mikkelmi2/aipcb/docs/reports/m11.md

# M11 — controlled impedance, card edges, via transitions & high-speed verification: delivery report

**Delivered, and this report is a reconstruction.** All of M11a–M11e, its tests,
`docs/format.md`, `docs/roadmap.md` and [ADR 0010](../decisions/0010-highspeed.md)
were built and committed across five commits (`4599b95`, `fbd048e`, `166fa4f`,
`e33b0ce`, `1e0a6a2`) by one session, which was then terminated by an
infrastructure failure — an API session limit — at the moment it said *"Now the
performance measurements:"*. This report was written afterwards, in a separate
pass over a clean tree at `1e0a6a2`, by someone who did not write the code.

Everything below is either **measured here, on a quiet machine, in this pass**, or
attributed to the ADR and the commit messages that the implementing session wrote.
Where the two disagree, the measurement wins and the disagreement is stated. Where
something could not be determined from the repository, it says so rather than
inventing an account. It is not a live record of how the work went, and it should
not be read as one.

## Deviations, stated loudly

Everything not delivered as the specification wrote it, in one place and at the top.

| Item | What happened |
|---|---|
| *"the M11e report runs clean (no reference-plane crossings, stubs under threshold) on everything that routed"* | **Two of twelve pair objects do not run clean.** Reference continuity and via stubs *are* clean — 629.3 mm projected, **0** plane crossings, worst stub **0.000 mm** against a 0.5 mm threshold, width and gap deviation **0.0** on all twelve. Skew is not: `REFCLKN+REFCLKP` comes out **0.292 mm** and `PCIE_RXN+PCIE_RXP` **0.256 mm** against the **0.125 mm** their class declares, and both are *delivered* rather than handed over. Discussed at length under "The skew question" — it is the one place in this milestone where the delivered result sits closest to the marginal delivery the milestone exists to prevent. |
| The `diff-pair` copper sliver | **Not resolved, and it was expected to be.** The kickoff expected M11d rule 1 to close it. Measured here: the routed, unfilled board still carries exactly **one** `copper_sliver` warning. Rule 1 could not have closed it — it applies only to classes naming an `impedance_diff_ohm`, and `diff-pair`'s `lvds` class names none (measured: `standoff` 1.0, `target_ohm` null). Full verdict below. |
| `standoff_k`'s own default | **Unusable on the milestone's own reference board.** The default is 3; `examples/pcie-sata` sets **1.4**, with the arithmetic written into the source. At k = 3 every pair on that board is refused. The rule works — it refuses correctly and names itself in the hint — but a default that no bundled board can take is a default worth flagging. |
| Net-class field names | **Renamed.** The specification writes `impedance_diff`, `max_skew`, `max_uncoupled` and `class: diff_pair`. The implementation spells the unit into each — `impedance_diff_ohm`, `max_skew_mm` (reused from M7), `max_uncoupled_mm` — and does **not** implement `class: diff_pair` at all, because pair-ness already comes from `diff_pair:` on the nets. Recorded in ADR 0010 under "The naming deviation"; repeated here because a reader following the specification will type four field names that do not exist. |
| A KiCad warning that cannot be removed | **`lib_footprint_mismatch` on every card-edge board.** ADR 0010 Decision 2 gives the board outline one author, which means placing the edge footprint without its own `Edge.Cuts`, which means it is no longer byte-identical to its library copy. Measured: `aipcb check examples/pcie-sata` returns **1 DRC warning and 0 DRC errors**, and that warning is this one. There is no version of this that has both. |
| Two contacts on the reference board are not connected at all | **PERST# and the A1–B17 presence-detect strap are absent from the netlist**, not handed over. Both must cross all three lane pairs and a sig/gnd/pwr/sig stackup has no signal layer left to cross on. The source says so in a comment; `docs/roadmap.md` records it. The consequence for the numbers: `90/90 routed` counts 90 connections that exist, and does not count two a real card would need. |
| No pair was handed over | The milestone's own framing was *"a human finishing 2 of 11 pairs manually is success"*. **Eleven of eleven routed as coupled pairs, and nothing reached M9f.** That is a better result than the bar, but it means the reference board does not exercise the hand-over path at all; the two M11d rules that *can* force a hand-over — the standoff corridor and the coupling budget — are proved by purpose-built fixtures in `tests/test_highspeed.py`, not by the shipped example. |
| AC-coupling capacitor *placement* | **Validated and measured, never moved.** `role: ac_coupling` checks that the two capacitors sit level across the pair's travel and reports how far out they are; the placer does not position them. Recorded in ADR 0010 and `docs/roadmap.md`. |
| Impedance derivation covers outer layers only | **Surface microstrip, and nothing checks that you asked for it.** A class routed on an inner layer between two planes is stripline, a different formula, and today it gets a microstrip width back with no warning. No bundled design does this; nothing stops one. Recorded in `docs/roadmap.md`. |
| "M11d is the only permitted stretcher change" | **`src/aipcb/route/stretch.py` was not touched.** The three rules landed in `route/pairs.py` (+425/−10), the coupled-pair path. Not a deviation from the letter — it is narrower than the guardrail allowed — but a reader looking for M11d in the stretcher will find nothing there. |
| Suite runtime | **Up from 13 m 57 s to 20 m 27 s** (1090 tests, up from 968). Measured here, not estimated. The new board is the expensive part — routing `pcie-sata` costs 36 s each time a test class does not have it cached — but the split between it and the 73 new unit tests was not separately measured. |

Nothing else was descoped.

## What was built

| Piece | Where it lives |
|---|---|
| M11a — the IPC-2141 derivation and the Hammerstad one it does not replace | `impedance.py` |
| — resolving a class's geometry against the declared stackup | `highspeed.py`, `model/layout.py` |
| — validating what comes out of it | `checks/impedance.py` |
| M11b — the card edge as a footprint: stripped `Edge.Cuts`, keepout, fab note | `compile/edge.py`, `compile/zones.py` |
| — outline-versus-footprint agreement, and the error that hands the vertices back | `checks/edge.py` |
| M11c — the pair via-transition generator | `route/transition.py`, `model/highspeed.py` |
| — the AC-coupling audit | `checks/accouple.py` |
| M11d — the three stretcher rules | `route/pairs.py` (+425 lines) |
| M11e — the high-speed verification report | `checks/highspeed.py` |

| New module | Lines |
|---|---|
| `tests/test_highspeed.py` | 1387 |
| `src/aipcb/checks/highspeed.py` | 768 |
| `src/aipcb/route/transition.py` | 657 |
| `examples/pcie-sata/design.yaml` | 589 |
| `src/aipcb/compile/edge.py` | 447 |
| `src/aipcb/checks/edge.py` | 356 |
| `src/aipcb/checks/accouple.py` | 238 |
| `src/aipcb/checks/impedance.py` | 205 |
| `src/aipcb/highspeed.py` | 196 |
| `src/aipcb/impedance.py` | 189 |
| `src/aipcb/model/highspeed.py` | 84 |
| `examples/library/highspeed.yaml` | 181 |

New source blocks, all optional: `transitions:`, `role: edge_connector`,
`role: ac_coupling`, and eight net-class fields. No new commands.

## The eleven pairs, one by one

This is what the milestone cares most about, so it is measured rather than read
off the source. One `aipcb check examples/pcie-sata/design.yaml --json`, on the
tree as committed, read out of `summary.routing.pairs` and `summary.highspeed.pairs`.

Eleven declared pairs become **fourteen coupled routing segments** — the PCIe
transmit lane is split in two by its coupling capacitors, and the receive pair and
the reference clock are each split in two by a via transition — which the M11e
report merges back into **twelve pair objects**.

| # | Pair | Class | Layer | Routed as a pair? | Coupled length | Skew / budget | Uncoupled / budget | Wall hugs | Verdict |
|---|---|---|---|---|---|---|---|---|---|
| 1 | `PCIE_TXP/N` (controller → caps) | `pcie_tx` | F.Cu | **yes** | 8.08 mm | 0.000 / 0.125 mm | 0.51 / 6.0 mm | **2** (`U1.17`, `U1.20`) | **routed, flagged** — rule 2, flag stands |
| 2 | `PCIE_TXP_C/N_C` (caps → fingers) | `pcie_tx` | F.Cu | **yes** | 10.07 mm | 0.000 / 0.125 mm | 0.76 / 6.0 mm | — | **routed within all M11d rules** |
| 3 | `PCIE_RXP/N` | `pcie_rx` | B.Cu + F.Cu | **yes** (both segments) | 18.83 mm | **0.256 / 0.125 mm** | 2.54 / 6.0 mm | **1** (`U1.22`) | **routed, over its skew budget** |
| 4 | `REFCLKP/N` | `pcie_rx` | B.Cu + F.Cu | **yes** (both segments) | 16.68 mm | **0.292 / 0.125 mm** | 2.69 / 6.0 mm | **1** (`U1.14`) | **routed, over its skew budget** |
| 5 | `SATA0_TXP/N` | `sata` | F.Cu | **yes** | 30.93 mm | 0.004 / 0.25 mm | 1.13 / 5.0 mm | — | **routed within all M11d rules** |
| 6 | `SATA0_RXP/N` | `sata` | F.Cu | **yes** | 31.10 mm | 0.199 / 0.25 mm | 0.44 / 5.0 mm | — | **routed within all M11d rules** |
| 7 | `SATA1_TXP/N` | `sata` | F.Cu | **yes** | 30.97 mm | 0.049 / 0.25 mm | 0.44 / 5.0 mm | — | **routed within all M11d rules** |
| 8 | `SATA1_RXP/N` | `sata` | F.Cu | **yes** | 31.41 mm | 0.124 / 0.25 mm | 0.45 / 5.0 mm | — | **routed within all M11d rules** |
| 9 | `SATA2_TXP/N` | `sata` | F.Cu | **yes** | 31.30 mm | 0.053 / 0.25 mm | 0.45 / 5.0 mm | — | **routed within all M11d rules** |
| 10 | `SATA2_RXP/N` | `sata` | F.Cu | **yes** | 30.92 mm | 0.021 / 0.25 mm | 0.44 / 5.0 mm | — | **routed within all M11d rules** |
| 11 | `SATA3_TXP/N` | `sata` | F.Cu | **yes** | 31.12 mm | 0.042 / 0.25 mm | 0.44 / 5.0 mm | — | **routed within all M11d rules** |
| 12 | `SATA3_RXP/N` | `sata` | F.Cu | **yes** | 30.93 mm | 0.004 / 0.25 mm | 1.13 / 5.0 mm | — | **routed within all M11d rules** |

Reading it as the milestone asks:

* **Handed over: none.** `summary.routing.handed_over` is empty; `routed` is 90 of
  90 connections, `failed` 0, in **one** negotiation iteration.
* **Routed within all three M11d rules and inside their own class budgets:
  nine of twelve pair objects** — all eight SATA pairs and the connector-side half
  of the PCIe transmit lane.
* **Routed, with M11d rule 2's flag standing: three** — the controller-side
  transmit pair and the F.Cu halves of the receive pair and the reference clock.
  Each leaves the QFN between the ground pads on either side of its escape, each
  was re-tightened once with those pads' clearance inflated, and re-tightening
  cannot move a pad. **This is the outcome rule 2 specifies in so many words**
  ("attempt one re-tighten … if that fails, the flag stands"), and it is the
  correct treatment: the pair is built, the deviation is named, its distance and
  length are in the report.
* **Routed, over a budget its own class declares: two** — the receive pair and the
  reference clock, on skew. These two are *also* among the three above, so the
  arithmetic across the twelve is 9 clean + 1 flagged only for wall-hugging + 2
  flagged for both. That last pair of pairs is not so easily defended, and it gets
  its own section.
* Every one of the twelve carries its derived geometry **exactly**: 0.2888 mm /
  0.15 mm on the 85 Ω classes, 0.2390 mm / 0.2 mm on the 100 Ω one, with a measured
  width and gap deviation of **0.0** read back off the copper.

The acceptance clause asked for *"≥ the SATA pairs route and tighten within all
M11d rules with 0 DRC violations"*. All eight SATA pairs do, and so do four more
segments; **0 DRC errors** on the filled board.

### The skew question, and whether the treatment is defensible

The specification's own wording is *"any pair that cannot meet the rules is handed
over via M9f with reasons, never delivered marginal"*. Two pairs are delivered
outside a number their class declares, so it is worth being explicit about which
side of that line they fall on.

**What is measured.** Half-conductor lengths, read off the router's own record:

| Pair | Positive half | Negative half | Out of length | Budget | As a fraction of the run |
|---|---|---|---|---|---|
| `REFCLKP/N` | 21.2157 mm | 20.9241 mm | **0.2916 mm** | 0.125 mm | 1.4 % |
| `PCIE_RXP/N` | 20.7427 mm | 20.9982 mm | **0.2555 mm** | 0.125 mm | 1.2 % |

They are exactly the two pairs a via transition splits, and they are the only two
pairs on the board over budget. The transition column itself is *not* the
asymmetry: the four signal vias sit symmetric about the point the source named to
within 7 µm (`REFCLKN` at +0.2749/−0.0072 mm from centre, `REFCLKP` at
−0.2749/+0.0072 mm). What the transition costs is the splay to the opened-out
0.55 mm via pitch at each end plus the two fan-outs it creates where there was one,
and `_match_lengths` reports there is no fan-out leg long enough to meander the
difference into.

**The case for the treatment being correct.** Skew is not one of M11d's three
rules. The three that force a hand-over are the standoff corridor, the wall-hugging
flag and the uncoupled budget; skew is an M11e *reporting* item, severity warning
by default, promotable to an error with `verify: error` on the class. Nothing was
silenced: six warnings across the two pairs, four `diff-pair-skew` and two
`hs-skew`, all carrying the number. The budget was **not** widened to fit — the
source's own comment records that the SATA class's first draft was 0.127 mm, that
one pair missed it by 49 µm, and that the class was rewritten with an argument
rather than tuned until the warning went away. And, on a first-principles estimate
made here: microstrip on this stackup at εr 4.4, h 0.2104 mm, w 0.2888 mm gives
εeff ≈ 3.25 and a delay of ≈ 6.0 ps/mm, so **0.292 mm is ≈ 1.8 ps against a Gen3
unit interval of 125 ps** — about 1.4 % of a UI. That is a number a link budget
absorbs without noticing.

**The case against.** The class declares 0.125 mm. It is not an inherited default;
somebody wrote it. A pair delivered at 2.3× its own declared budget is a pair the
source and the board disagree about, and the mechanism that exists to make that
disagreement fatal — `verify: error` — was available and not used. The acceptance
clause *"the M11e report runs clean … on everything that routed"* is, on the
measurement, **not met**.

**The verdict this report takes.** The treatment is defensible, and the acceptance
clause is still missed. Those are both true and it is worth keeping them apart. It
is defensible because the failure is loud, quantified, tied to a named cause, and
because the alternative on offer was not "a better pair" but "no PCIe lane at all
on a four-layer stackup" — the pre-M11c behaviour, where a pair that had to change
layer was simply refused. What would make it indefensible is the budget being
edited to 0.3 mm, and it was not. But *"runs clean"* is what the milestone asked
for, and 10 of 12 is not 12 of 12; it belongs in the deviations table, which is
where it is.

The honest framing for anyone reading the board rather than the report: **the eight
SATA pairs are finished work. The PCIe lane is routed, measured and annotated, and
a Gen3 sign-off still wants a human and an SI tool** — which is what
`summary.highspeed.method` says in the report itself: *"rule-based geometry checks,
not electromagnetic simulation"*.

## The `diff-pair` copper sliver: an expectation that was not met

The milestone kickoff told the implementing session that M11d's rules were
*expected* to resolve the known copper sliver on `examples/diff-pair`, and to flag
it prominently if they did not. **They did not.** Measured here rather than
inferred:

| Board | Command | `copper_sliver` |
|---|---|---|
| `diff-pair`, routed, **unfilled** | `aipcb route all` then `kicad-cli pcb drc --severity-all` | **1** (warning, F.Cu) |
| `diff-pair`, routed, **filled** | `aipcb check` | **0** |

The track geometry is unchanged by M11. Why rule 1 could not have touched it, from
the code and from the same measurement run: **M11d applies only to a class that
names an `impedance_diff_ohm`, and `diff-pair`'s `lvds` class names none** — its
pair audit comes back with `standoff: 1.0` and `target_ohm: null`, so the standoff
corridor never ran on that board at all. `docs/roadmap.md` adds that the sliver is
between two **GND** tracks rather than between the pair's halves, which would put
it out of rule 1's reach even on a controlled-impedance board.

That last point is the one thing here I **could not verify independently**: KiCad
9.0.8 reports this violation with an empty `items` array and no position, in both
the JSON and the report format, so DRC does not say which copper it is between.
The claim that it is between two GND tracks is the implementing session's, taken
from `docs/roadmap.md` and `tests/test_routing.py`, and this pass could not confirm
or refute it.

The marker in `tests/test_check_loop.py` — `"diff-pair": frozenset({"kicad-copper-sliver"})`
— is **left standing and must stay standing**. It is a permissive allowance rather
than a required outcome, so it is vacuous under `aipcb check` today (which reads
the filled board, where the pour closes the wedge); it is live in
`tests/test_routing.py::ALLOWED_VIOLATIONS`, which reads the unfilled one. Retiring
it would delete the record of a defect that is still in the copper a fabricator
receives before the pour is drawn. To the implementing session's credit it was not
touched.

## The four `pcie-sata` known issues

`tests/test_check_loop.py` gained a `pcie-sata` entry with four codes and the
reasoning written into the file. Measured here, each one:

| Code | Count | What it is, measured |
|---|---|---|
| `diff-pair-wall-hugging` | **3** | M11d rule 2, flag standing after one failed re-tighten. `PCIE_TXN+PCIE_TXP` beside `U1.17` and `U1.20`, both at **0.261 mm for 0.774 mm**; `REFCLKN+REFCLKP` beside `U1.14` at **0.218 mm for 0.899 mm**; `PCIE_RXN+PCIE_RXP` beside `U1.22` at **0.257 mm for 0.796 mm**. Threshold: closer than 3 × the 0.15 mm gap (0.45 mm) for longer than 5 × it (0.75 mm). All three were re-tightened with the offending pads' clearance inflated; the audit records `retightened: true, resolved_by_retighten: false` for each. **This is the outcome rule 2 specifies. Defensible without qualification.** |
| `diff-pair-skew` | **4** | Two pairs, reported twice each — see the reporting wart below. From `_match_lengths` at 0.251 mm (REFCLK) and 0.249 mm (PCIE_RX); from `measure_skew` over the whole conductor at 0.292 mm and 0.256 mm. |
| `hs-skew` | **2** | M11e restating the whole-conductor numbers — 0.292 mm and 0.256 mm — after meanders. **Closer to a marginal delivery than the wall-hugging flag is, and argued out above.** |
| `kicad-lib-footprint-mismatch` | **1** | The card-edge footprint placed without its own `Edge.Cuts`, so it no longer matches its library copy. The unavoidable price of ADR 0010 Decision 2. It is the board's **only** DRC finding, and it is a warning; DRC errors are 0. |

**A reporting wart found while measuring, not fixed.** The same pair is reported
out of budget **three times, with two different numbers** and no label saying why
they differ. `route/pairs.py::_match_lengths` warns per routed *segment* while it is
still trying to meander (0.251 mm for the reference clock); `measure_skew` then
warns again over the *whole conductor*, via barrels included (0.292 mm for the
same pair); and M11e reports the second number a third time as `hs-skew`. Six
warnings for two pairs. Nothing is wrong with any individual number — they measure
different things — but a reader gets "REFCLKN+REFCLKP is 0.251 mm out of length"
and "REFCLKN+REFCLKP is 0.292 mm out of length" three lines apart with no
explanation. Reported here rather than corrected, because this pass documents and
measures the delivered code rather than changing it.

## Per-pad-instance keying, re-verified against the shared-UUID defect

`docs/roadmap.md` records that pads sharing a *number* share a UUID, and M11's
brief warned this was where an edge connector would bite hardest. Re-measured here
on the boards this milestone actually builds:

| Component | Footprint | Pads | Distinct numbers | Distinct pad UUIDs |
|---|---|---|---|---|
| `J1` (the card edge) | `Connector_PCBEdge:BUS_PCIexpress_x1` | **36** | **36** | **36** |
| `J2`–`J5` (SATA) | `Connector_JST:JST_GH_SM07B-GHS-TB…` | 9 | 8 | **8** |
| `U1` | `Package_DFN_QFN:QFN-48-1EP_7x7mm_P0.5mm` | 65 | 50 | **50** |
| `usb-port`'s `J1`, for comparison | `Connector_USB:USB_Micro-B_Amphenol_10103594-0001LF_Horizontal` | 17 | 6 | **6** |

* **The defect does not bite the card edge at all.** KiCad's PCIe x1 footprint
  numbers every contact distinctly, `A1`–`A18` and `B1`–`B18`, so each finger has
  its own identity in the file as well as in the router. That confirms ADR 0010's
  Finding 4 independently.
* **The defect is still there, on the same board.** Each JST connector has two
  shell tabs both numbered `MP` sharing one UUID, and each QFN has sixteen
  exposed-pad sub-pads numbered `49` sharing one. The router tells them apart
  because `route.obstacles` keys on `reference#index` and never on the UUID.
* **`usb-port` is unchanged**: **31 pads carrying 20 distinct UUIDs**, with twelve
  pads numbered `6` sharing one. Exactly the figure M10 recorded, so nothing in M11
  moved it either way.

### What commit `1e0a6a2` actually found

The commit titled *"the keepout the UUID index had not heard of"* is not about pad
UUIDs. It is about the **one zone in this toolchain that nobody declares**: M11b
puts a pour keepout round a card edge's finger field, generated from the
connector's placement rather than written in `pours:`, and nothing mapped its UUID
back to source. Reproduced here by building the index with and without the fix and
running the same synthetic DRC violation through `checks/kicad_reports.py`:

| Index | Where the violation points | Hint |
|---|---|---|
| **as shipped** | `examples/pcie-sata/design.yaml:451:3`, path `('placement', 'J_PCIE')` | the real edge-clearance hint |
| **without the entry** | nowhere — `loc: None`, `path: ()`, `unmapped_uuids: ['07808365-…']` | *"this item is not one aipcb generated — it was probably added by hand in KiCad"* |

Which is exactly the wrong answer about the one piece of copper geometry the
toolchain invented by itself. The zone is in the board as
`"J1 finger field, kept clear of pour"`, 20.9 × 5.5 mm on `F.Cu` and `B.Cu` with
`copperpour not_allowed`, and its UUID `07808365-5859-56df-bdf7-867032aa3787` is
`element_uuid("zone", "fingers", "J1")` — a function of the source, like every
other generated identity. The defect surfaced when the *full* suite ran, not when
the M11b tests did: it takes a DRC violation landing on that zone to see it.

## What else was verified

### The card edge

Measured on the built board: `J1`'s footprint carries **0** `Edge.Cuts` primitives
(they are stripped), the top-level outline carries 16 `Edge.Cuts` graphics, and
`checks/edge.py` reports *"the board outline reproduces all 11 of the footprint's
edge primitives, to within 0.01 mm"*. The finger keepout is present as described
above; the fab note reads *"36 fingers on B.Cu, F.Cu, set back 1.30 mm from the
card's leading edge. The set-back is where the bevel goes"*. The acceptance case
that the missing-notch error must fail *helpfully* is
`test_a_missing_notch_is_an_error_that_hands_the_vertices_back`, which asserts the
hint contains a pasteable `board:` block.

**Not verified here: that the board "opens correctly in KiCad".** This pass has no
GUI. `kicad-cli`'s ERC and DRC both run to completion on it, and `pcbnew` loads it
to fill it, which is the strongest proxy available headlessly.

### The via transitions

Two, both declared in the source, both on the pairs that arrive on the A-side
fingers (on `B.Cu`) and leave the controller on `F.Cu`:

| Transition | Pair | Pitch → via pitch | Return vias | Furthest | Barrel | Stub |
|---|---|---|---|---|---|---|
| 0 | `REFCLKN+REFCLKP` | 0.4388 → **0.55 mm** | **2 of 2** | 0.9999 mm (budget 1.2) | F.Cu–B.Cu | **0.000 mm** |
| 1 | `PCIE_RXN+PCIE_RXP` | 0.4388 → **0.55 mm** | **2 of 2** | 0.9999 mm (budget 1.2) | F.Cu–B.Cu | **0.000 mm** |

Zero stub is the right answer for an outer-to-outer through via and, per commit
`e33b0ce`, it is the answer that had to be *earned* — see the findings below.

### The AC coupling

`C2`/`C3` couple `PCIE_TXN+PCIE_TXP` to `PCIE_TXN_C+PCIE_TXP_C`, measured at
**1.400 mm apart across the route and level along it to within 0.0000 mm**. Both
halves of both segments come out at identical length (8.5937 mm each side before
the caps, 10.8312 mm each side after), which is what "symmetric entry" means when
it is read off the geometry rather than asserted.

### The M11e report on `pcie-sata`

| Measure | Result | Threshold |
|---|---|---|
| Controlled-impedance track projected onto its declared reference | **629.3 mm** | — |
| Reference-plane crossings (splits, voids, net changes) | **0** | any is a finding |
| Worst via stub | **0.000 mm** on `PCIE_RXN` | 0.5 mm |
| Width deviation, all 12 pair objects | **0.0** | 10 % |
| Gap deviation, all 12 pair objects | **0.0** | 10 % |
| Pairs over their coupling budget | **0** (worst 2.69 mm against 6.0) | per class |
| Pairs over their skew budget | **2** | per class |

Commit `fbd048e` records 550.1 mm of controlled-impedance track; the measurement
here is 629.3 mm, because that commit predates M11c and the two transitions it
adds. Both numbers are right for the tree they were taken on.

### The impedance derivation, checked against a second implementation

The ADR's arithmetic was re-derived here from IPC-2141 by hand rather than trusted:

| Target | Gap | `solve_width` | Independent recomputation of `Zdiff` |
|---|---|---|---|
| 85 Ω | 0.15 mm | **0.2888 mm** | 85.008 Ω |
| 100 Ω | 0.20 mm | **0.2390 mm** | 100.001 Ω |
| 85 Ω | 0.20 mm | **0.3220 mm** | 85.002 Ω |

The module and the hand recomputation agree to three decimal places, and the widths
are the ones the board actually carries. The Hammerstad/IPC disagreement ADR 0010
calls "8 %" measures **8.4 %** at 0.322 mm on this stackup (92.18 Ω against
85.00 Ω). The declared stack sums to 0.1004 mm of copper plus 1.4858 mm of
dielectric plus 0.02 mm of mask = **1.606 mm**, which is the 1.6 mm the source
declares.

### Everything that was already working

Measured in this pass, all eleven examples:

| Example | Build byte-stable | Byte-identical to its golden | `filled_polygon` in build output | Check errors | DRC errors | Routed |
|---|---|---|---|---|---|---|
| `congestion` | yes | yes | 0 | 0 | 0 | 4/4 |
| `diff-pair` | yes | yes | 0 | 0 | 0 | 11/11 |
| `enclosure` | yes | yes | 0 | 0 | 0 | 32/32 |
| `ldo-supply` | yes | yes | 0 | 0 | 0 | 13/13 |
| `led-blinker` | yes | yes | 0 | 0 | 0 | 13/13 |
| `mcu-4layer` | yes | yes | 0 | 0 | 0 | 36/36 |
| `overconstrained` | yes | yes | 0 | 0 | 0 | 1/4¹ |
| `pcie-sata` | yes | yes | 0 | 0 | 0² | 90/90 |
| `qfn-fanout` | yes | yes | 0 | 0 | 0 | 41/41 |
| `routing-demo` | yes | yes | 0 | 0 | 0 | 10/10 |
| `usb-port` | yes | yes | 0 | 0 | 0 | 24/24 |

¹ `overconstrained` is the example that cannot be finished; three connections are
handed over and stay as ratlines, exactly as before M11.
² One DRC *warning*: `lib_footprint_mismatch`, discussed above.

The backward-compatibility claim is stronger than "byte-stable": `git diff
b7d9c5e..HEAD -- tests/golden/` shows **only `tests/golden/pcie-sata/` was added**
and no pre-M11 golden was touched, so all ten earlier examples rebuild
byte-identically to files frozen before this milestone existed. Every example's
build output still contains **zero** `filled_polygon` records, which is M10's
stability policy holding under a new generator.

The only non-`info` diagnostics anywhere outside `pcie-sata` are the two already
known: `qfn-fanout`'s deliberate `plane-fragmented` and `usb-port`'s
`diff-pair-not-coupled` honest refusal.

## Performance

Measured on 2026-08-21 on the tree at `1e0a6a2`, one run each, on all eleven
examples, with nothing else running — no test suite, no other job. KiCad 9.0.8.
This table is what M12 measures regressions against.

### The pipeline, end to end

`aipcb`'s own commands, cold per invocation. `route` and `check` are *incremental*
(`route all` minus `build`, and `check` minus `route all`), because each command
re-runs the stages before it. **M10's numbers in brackets where they exist.**

| Example | `validate` | `build` | route | check | `export` |
|---|---|---|---|---|---|
| `congestion` | 1.75 s *(1.72)* | 1.77 s *(1.78)* | 0.19 s *(0.15)* | 0.75 s *(0.76)* | 2.33 s *(2.30)* |
| `diff-pair` | 2.31 s *(2.34)* | 2.44 s *(2.43)* | 0.58 s *(0.54)* | 2.08 s *(2.18)* | 3.83 s *(3.76)* |
| `enclosure` | 3.58 s *(3.50)* | 3.68 s *(3.54)* | 4.54 s *(4.55)* | 2.22 s *(2.25)* | 5.03 s *(4.93)* |
| `ldo-supply` | 2.90 s *(2.85)* | 2.94 s *(2.97)* | 0.40 s *(0.38)* | 2.15 s *(2.18)* | 4.34 s *(4.27)* |
| `led-blinker` | 2.49 s *(2.49)* | 2.57 s *(2.53)* | 0.75 s *(0.78)* | 2.17 s *(2.18)* | 3.92 s *(3.86)* |
| `mcu-4layer` | 4.19 s *(4.11)* | 4.23 s *(4.17)* | 10.44 s *(10.42)* | 2.74 s *(2.65)* | 5.88 s *(5.80)* |
| `overconstrained` | 1.76 s *(1.74)* | 1.78 s *(1.75)* | 0.24 s *(0.21)* | 0.71 s *(0.82)* | 2.33 s *(2.31)* |
| **`pcie-sata`** | **5.23 s** | **5.29 s** | **36.93 s** | **2.15 s** | **6.91 s** |
| `qfn-fanout` | 2.80 s *(2.78)* | 2.88 s *(2.94)* | 5.71 s *(5.60)* | 2.40 s *(2.44)* | 4.24 s *(4.22)* |
| `routing-demo` | 2.48 s *(2.47)* | 2.54 s *(2.55)* | 0.85 s *(0.78)* | 2.14 s *(2.22)* | 3.91 s *(3.87)* |
| `usb-port` | 3.49 s *(3.43)* | 3.54 s *(3.46)* | 2.83 s *(2.90)* | 2.23 s *(2.21)* | 4.82 s *(4.81)* |
| **total, 11** | **32.98 s** | **33.66 s** | **63.46 s** | **21.74 s** | **47.54 s** |
| the same ten M10 measured | 27.75 s *(27.43)* | 28.37 s *(28.12)* | 26.53 s *(26.33)* | 19.59 s *(19.88)* | 40.63 s *(40.12)* |

**No stage regressed.** On the ten examples M10 measured, `validate` moves +1.2 %,
`build` +0.9 %, `route` +0.8 %, `export` +1.3 % and `check` **−1.5 %**. Every
per-example difference is within 0.15 s; the three largest are `enclosure`'s build
(+0.14 s), `overconstrained`'s checking (−0.11 s) and `qfn-fanout`'s routing
(+0.11 s), which is what one run each on one machine looks like rather than a
trend. A design that names no `impedance_diff_ohm` runs none of M11's new code,
and the numbers say so.

### `pcie-sata`, prominently

It is the most expensive board in the repository by a wide margin — **44.4 s** of
wall clock for `aipcb check`, against 17.4 s for the next one (`mcu-4layer`). Of
that, 39.9 s is the work itself and the remaining ≈4.5 s is interpreter start plus
the cold library resolution every command pays. Where the 39.9 s goes, measured in
one process so the stages are comparable:

| Stage | Time | Share of the 39.9 s in-process check |
|---|---|---|
| `build` | 1.14 s | 2.9 % |
| **routing (total)** | **35.56 s** | **89.1 %** |
| — of which: transition generation (M11c) | 0.027 s | 0.07 % |
| — of which: pair centre-line tightening, first pass (14 calls) | 4.493 s | 11.3 % |
| — of which: **M11d rule 2 wall-hug scans (14 calls)** | **0.014 s** | **0.03 %** |
| — of which: **M11d rule 2 re-tighten rounds (3 calls)** | **0.125 s** | **0.31 %** |
| stitching | 0.034 s | 0.1 % |
| plane analysis (M10d) | 0.013 s | 0.03 % |
| **M11e high-speed analysis** | **0.111 s** | **0.28 %** |
| zone fill (`pcbnew`) | 1.65 s | 4.1 % |
| `kicad-cli sch erc` | 0.39 s | 1.0 % |
| `kicad-cli pcb drc` | 0.89 s | 2.2 % |
| `kicad-cli pcb export gerbers` | 0.19 s | — (export only) |

**What the M11d re-tightening rounds cost: 0.139 seconds**, on a board where three
pairs trip rule 2 — 0.35 % of the check, 0.4 % of the routing. **What the M11e
analysis costs: 0.111 seconds** for 629.3 mm of track projected onto two planes at
50 µm steps, plus the geometry audit, the skew read-back, the stub arithmetic and
the coupling audit. Both are, in practice, free.

**One caveat, and it matters.** M11d **rule 1 is not separable** from the number
above. The standoff corridor is not an extra pass — it widens the corridor handed
to A\*, which changes the congestion penalty and therefore the search on every
controlled-impedance connection. There is no way to time it without routing the
board twice with two different `standoff_k`, and this pass did not change the
example to do so. What *can* be said is that **rule 2 costs 0.14 s** on the
board that trips it three times, and that rule 3's budget check — a maximum over a
list of per-half lengths — is too small to time separately and was not. And that
35.6 s of routing on
a 90-connection four-layer board is in line with `mcu-4layer`'s 10.0 s for 36
connections and `qfn-fanout`'s 5.7 s for 41.

### Where the time goes, all eleven examples

`aipcb`'s own stages on the left, what `kicad-cli` and `pcbnew` cost on the right,
measured in one process so the library caches are warm after the first example —
which is why `build` here is a fraction of the `build` column above. The ≈2.5 s
difference is the same fixed floor M10 identified: resolving parts against KiCad's
on-disk libraries, paid once per process by every command, and still nobody has
looked at it.

| Example | build | route | transitions | stitching | planes | high speed | | fill (`pcbnew`) | ERC | DRC | gerbers |
|---|---|---|---|---|---|---|---|---|---|---|---|
| `congestion` | 0.89 s | 0.18 s | — | — | — | — | | — | 0.20 s | 0.54 s | 0.17 s |
| `diff-pair` | 0.35 s | 0.56 s | — | — | 2 ms | — | | 1.26 s | 0.23 s | 0.57 s | 0.18 s |
| `enclosure` | 0.78 s | 4.49 s | — | 0.02 s | 3 ms | — | | 1.22 s | 0.30 s | 0.67 s | 0.18 s |
| `ldo-supply` | 0.44 s | 0.39 s | — | — | 3 ms | — | | 1.20 s | 0.26 s | 0.59 s | 0.18 s |
| `led-blinker` | 0.11 s | 0.72 s | — | — | 3 ms | — | | 1.20 s | 0.24 s | 0.65 s | 0.19 s |
| `mcu-4layer` | 0.06 s | 10.05 s | — | 0.03 s | 10 ms | — | | 1.62 s | 0.33 s | 0.70 s | 0.19 s |
| `overconstrained` | 0.02 s | 0.20 s | — | — | — | — | | — | 0.20 s | 0.53 s | 0.18 s |
| **`pcie-sata`** | **1.14 s** | **35.56 s** | **0.03 s** | **0.03 s** | **13 ms** | **0.11 s** | | **1.65 s** | **0.39 s** | **0.89 s** | **0.19 s** |
| `qfn-fanout` | 0.28 s | 5.65 s | — | 0.03 s | 6 ms | — | | 1.22 s | 0.26 s | 0.78 s | 0.20 s |
| `routing-demo` | 0.04 s | 0.78 s | — | — | 4 ms | — | | 1.20 s | 0.24 s | 0.63 s | 0.18 s |
| `usb-port` | 0.04 s | 2.78 s | — | 0.03 s | 3 ms | — | | 1.22 s | 0.30 s | 0.61 s | 0.18 s |

Against M10's equivalent table, every column on every pre-M11 example is within
measurement noise of where it was: `mcu-4layer`'s routing 10.20 → 10.05 s,
`qfn-fanout`'s 5.69 → 5.65 s, the fill flat at 1.20–1.65 s everywhere, ERC and DRC
unmoved. The only two entries that changed by more than 0.1 s are `ldo-supply`'s
build (0.32 → 0.44 s) and `qfn-fanout`'s (0.44 → 0.28 s), in opposite directions,
which is what per-process cache ordering looks like rather than a regression in
either.

Three things worth naming:

* **The high-speed analysis is free**, at 0.11 s on the only board that runs it —
  the same order as M10's plane analysis, and for the same reason: it is geometry
  over polygons somebody else already computed.
* **`pcie-sata`'s `build` is genuinely 1.14 s** and not a cache artefact — it is the
  eighth example in that process, so the caches are warm. Twelve components, a
  36-pad edge footprint, a 65-pad QFN and the outline-versus-footprint comparison
  cost more than any other board's build.
* **Routing still dominates everything**, now more than ever: 61.4 s of the 88.1 s
  total across eleven boards, 35.6 s of it one board. M11 did not change that and
  did not make it worse.
* **M10's "fixed ≈2.5 s floor" is not fixed.** Subtracting each warm build above
  from its cold counterpart in the first table gives 0.88 s (`congestion`), 1.76 s
  (`overconstrained`), 2.46–2.60 s (four boards), 2.90 s (`enclosure`), 3.50 s
  (`usb-port`), 4.15 s (`pcie-sata`) and **4.17 s (`mcu-4layer`)**. It tracks how
  many distinct KiCad footprint libraries a design touches, not a constant. It is
  still the largest single cost on **seven of the eleven** examples — everywhere
  routing does not dominate — and it is still unexamined.

## The empirical findings

Eight are in [ADR 0010](../decisions/0010-highspeed.md), written by the session
that measured them. The ones that changed a decision, with what this pass could
confirm:

**The two impedance formulas in this codebase disagree by 8 %** (Finding 1).
Confirmed here at **8.4 %** on the reference stackup. The controlled-impedance path
uses IPC-2141 for both the derivation *and* the audit that later checks it, because
an audit that recomputes the target with a different formula audits the arithmetic
rather than the board. Hammerstad stays on the M8 `estimate_gap` path so no
pre-M11 board changes geometry — which the byte-identical goldens confirm.

**`layout.stackup.layers` was decorative and had to stop being** (Finding 2). The
block had been in the schema since M1 and nothing derived geometry from it; the
uniform-dielectric fallback gives 0.48 mm where the prepreg under `F.Cu` is
0.2104 mm, a factor of 2.3 and a 40 % error in the derived width. A declared stack
is now honoured, and only when it is *complete* — a partial declaration is ignored
rather than half-believed, because it looks authoritative and is not.

**Emitting both outline authors produces a board KiCad rejects** (Finding 3). Two
`invalid_outline: self-intersecting` errors plus ten `copper_edge_clearance` ones,
all twelve gone when the footprint's copy is stripped.

**A return via placed by eye costs the pair its coupling** (Finding 5). Placed at
0.925 mm from the transition centre against the 1.007 mm the pair's corridor needs,
the receive pair could not tighten, fell back to two separately routed nets, and
those took detours that cost eight further pairs their coupling. **82 µm, and 9 of
14 coupled runs.** The generator computes the distance instead of choosing it, and
the shipping board places its return vias at 0.9999 mm.

**KiCad normalises a through via's recorded span — and that is the finding that
made the via-stub number real** (Finding 6; commit `e33b0ce`). A via written
`(layers "F.Cu" "In2.Cu")` with a through drill comes back from `pcbnew` written
`(layers "F.Cu" "B.Cu")`. That is not wrong — a through via *is* drilled the whole
way — but it erases the one thing a stub calculation needs, which is where the
signal stopped. **Every stub measured off the filled board therefore came out at
exactly zero: comfortable, and false.** The stub is now taken from the router's own
record of what it drilled, and the filled board is used only for what it is
authoritative about, which is copper. The 0.000 mm in the table above is now zero
because the barrel really does end where the signal does; it is a corrected
measurement rather than an unchanged one, and a test
(`test_a_transition_to_an_inner_layer_leaves_the_rest_of_the_barrel`) makes the
non-zero case fail if the shortcut ever comes back.

**"Parallel" is load-bearing in rule 2.** The first implementation measured the
length of centre-line inside a feature's skirt, which counts going past the end of
a pad as hugging it — 1.11 mm on the QFN escape where the parallel part is the
pad's own 0.875 mm, under the 1.0 mm threshold. The stretch is now counted only
while the distance holds to within one gap of its closest approach.

**An `Edge.Cuts` arc costs the router its clearance** (Finding 7). Arcs are
approximated by 24 chords, and a chord runs inside its arc by the sagitta — 8.13 µm
on the 0.95 mm keying notch. KiCad reported ten `copper_edge_clearance` errors at
0.1419 mm against 0.1500 mm asked for; 0.1500 − 0.1419 = 0.0081 mm, the sagitta to
two significant figures. `RoutingEnvironment.arc_slack` now adds the worst sagitta
on the board to the edge keep-out.

**A fabricator needs web between holes, not daylight** (Finding 8). Two GND vias
0.3250 mm apart left 0.1255 mm of web against a 0.2495 mm minimum;
`merge_overlapping_holes` merged holes that *overlapped*, and the test is now the
drill plus the minimum web.

## Defects found

Six. Four fixed, two recorded and not chased:

* **An `Edge.Cuts` arc's chord approximation ate the edge clearance.** Fixed
  (Finding 7). Surfaced because `pcie-sata` is the first board to hug an arc.
* **Same-net via merging used overlap where it needed web.** Fixed (Finding 8).
  Surfaced from a DRC violation on the same board.
* **Via stubs measured off the filled board were all zero, and wrongly so.** Fixed
  by reading the router's record instead (Finding 6). Surfaced because a test
  asserted a *non-zero* stub for an inner-layer transition and got zero.
* **The card-edge pour keepout had no source mapping.** Fixed in `1e0a6a2`.
  Surfaced when the full suite ran, not when M11b's own tests did.
* **`_repair` can produce a route that crosses another net.** *Not fixed.* Found on
  `PRSNT` before that net was dropped: the second-pass repair in
  `route/plan.py::_repair` routed it across two already-placed `REFCLK` tracks and
  KiCad reported two `tracks_crossing` errors. The repair builds its private field
  from the base environment *plus* everything placed so far, so the copper it
  crossed *was* in the obstacle set — something between that field and the realized
  geometry is not honouring it. Recorded in `docs/roadmap.md` rather than left as a
  surprise. It does not manifest on any bundled example today: `pcie-sata` runs 16
  `route-repaired` second passes and comes back with 0 DRC errors. **It is router
  work, it is unexplained, and it is the most serious thing in this report that is
  still open.**
* **The skew reporting wart** described above: one pair, three warnings, two
  different numbers, no label. Found in this measuring pass; not fixed, because
  this pass documents rather than changes.

## Deliberately not built

Recorded in [`docs/roadmap.md`](../roadmap.md) and ADR 0010:

* **Electromagnetic simulation and eye-diagram prediction.** M11e is rule-based
  geometry and says so in its own first line, in `summary.highspeed.method` and in
  the README. Exporting geometry to a solver is M12's subject.
* **Full environment-controlled tightening** beyond the three M11d rules.
* **Back-drilling and blind/buried-via optimisation** for stub elimination. The stub
  is measured and reported; removing it is a fabrication process nothing here
  should commit somebody to by default.
* **Placing the AC-coupling capacitors.** Validated and measured, not moved.
* **Unifying the two impedance formulas.** Kept apart deliberately, because
  changing the old one moves the geometry of every board built before M11.
* **Stripline.** An inner-layer pair gets a microstrip width and no warning.

## Suite state

| Check | Result |
|---|---|
| `pytest -q` | **exit 0** — **1089 passed, 1 skipped**, **20 m 27 s** (1090 collected, up from 968) |
| `ruff check .` | **All checks passed** |
| `mypy --strict src/aipcb` | **Success: no issues found in 75 source files** (66 before M11) |

The one skip is `test_sexpr_corpus`'s, as it has been since M1. The suite grew by
**122 tests and 6.5 minutes**; `tests/test_highspeed.py` is new and holds 73 test
methods across thirteen classes, and the rest is the parametrised per-example
classes gaining an eleventh example that takes 36 s to route.

The acceptance cases the specification names each have a fixture built to make the
answer knowable:

| Acceptance case | Test |
|---|---|
| the missing keying notch must fail *helpfully* | `test_a_missing_notch_is_an_error_that_hands_the_vertices_back` — asserts the hint contains a pasteable `board:` block with the notch's own vertices |
| return vias within spec, stub computed against the stackup | `test_return_vias_are_placed_within_spec`, `test_an_outer_to_outer_through_via_has_no_stub`, `test_a_transition_to_an_inner_layer_leaves_the_rest_of_the_barrel` |
| pair-cap-pair as one object, symmetric entry, budget | `test_the_example_couples_symmetrically`, `test_the_pairing_comes_from_the_netlist`, `test_moving_one_capacitor_along_the_route_is_reported` |
| wall-hugging: the re-tighten resolves it, or the flag appears | `test_a_pair_beside_a_wall_is_re_tightened_away_from_it` (a header 1.8 mm away, resolved) and `test_the_wall_hugging_rule_fires_and_says_what_it_found` (the reference board, flag standing) |
| a wrong width warns at validation *and* in the audit | `test_a_deliberately_wrong_width_is_reported_twice`, `test_a_class_may_promote_its_findings_to_errors` |
| the M11d refusals | `test_an_uncoupled_budget_that_cannot_be_met_is_a_refusal`, `test_a_standoff_the_board_cannot_give_refuses_and_names_itself`, `test_the_standoff_applies_only_to_controlled_impedance_classes` |
| the generator regime | `test_a_second_run_into_the_same_directory_is_byte_identical`, `test_the_transition_vias_are_not_duplicated_by_a_second_run`, `test_the_uuid_space_is_a_function_of_the_source` |
| the shared-pad-UUID defect, both ways | `test_the_pcie_fingers_do_not_share_pad_numbers`, `test_the_sata_shells_do_share_one_and_the_router_still_tells_them_apart` |

One existing test class changed deliberately: `TestCheckLoop.KNOWN_ISSUES` gained a
`pcie-sata` entry with four codes and the reasoning written into the file. The
`diff-pair` entry was **not** touched, which is the right call — see the sliver
verdict above.

## What M12 needs to know

M12 is SI simulation, and **it will simulate only the pairs that actually routed**,
so the pair-by-pair table above is its direct input. Concretely:

* **Twelve pair objects are available to simulate**, all coupled, all carrying their
  derived geometry exactly. Nine are inside every budget their class declares; three
  carry a standing wall-hugging flag with the offending feature, its distance and
  the parallel length named; two are over their skew budget by a measured amount.
  Nothing is handed over, so there is no "unrouted pair" case to handle on this
  board — and equally, no example in the repository exercises the M9f hand-over of
  a *controlled-impedance* pair. If M12 needs one, it will have to build it.
* **`summary.highspeed` in `aipcb check --json` is the machine-readable form**, with
  `method` stating in the payload itself that this is not simulation. It carries
  per-pair target and actual width and gap, coupled and uncoupled lengths, skew, the
  reference-gap list and the via-stub list with positions.
* **The reference plane is *declared*, never inferred.** `reference:` on the class;
  `pcie_tx` and `sata` name `In1.Cu` (GND), `pcie_rx` names `In2.Cu` (P3V3, which is
  an AC ground for a decoupled rail and, more usefully, a continuous one). A solver
  wanting the real return path should read that field rather than guessing at the
  nearest plane.
* **The stub number comes from the router, not the board.** Finding 6 above. Any
  M12 code that reads via spans off a `pcbnew`-round-tripped board will get
  `F.Cu`/`B.Cu` for everything and compute a stub of zero for every via on the
  board. This is the single most likely way for M12 to produce a comfortable, false
  number.
* **A board with no `pours:` gets `hs-reference-unchecked` rather than a silent
  pass.** The reference check needs filled copper and therefore ADR 0009's `pcbnew`
  subprocess.
* **`analyse_highspeed(tree, netlist, audits, skew, vias=…, filled=…)` is a pure
  function of a parsed board plus the router's audit records.** It costs 0.11 s on
  the largest board here. A second consumer of the same inputs is cheap.
* **The geometry M12 would export is microstrip only.** Nothing checks that a
  controlled-impedance class is on an outer layer, and an inner-layer pair silently
  gets a microstrip width. If M12 exports geometry for a solver, that is the first
  place the solver and this toolchain will disagree.

Open questions this milestone leaves:

* **`_repair` crossing another net** — unexplained, recorded, not reproducible on
  any bundled example. It is a routing correctness question and it outranks
  everything else on this list.
* **The skew reporting wart** — three warnings, two numbers, one pair.
* **Is 0.125 mm the right intra-pair skew budget for a Gen3 class?** The board
  declares it and misses it by 2.3× on two pairs; the estimate above puts the miss
  at ≈1.8 ps against a 125 ps UI. Either the budget is too tight for what this
  router can deliver through a via transition, or the transition needs to give
  length back. Nobody has decided which, and the report currently just says the
  number.
* **The per-process library-resolution cost**, which M10 called a "fixed ≈2.5 s
  floor". Measured across eleven examples here it is **not fixed**: subtracting the
  warm in-process build from the cold command gives 0.88 s on `congestion`, 2.50 s
  on `ldo-supply`, 3.50 s on `usb-port` and **4.17 s on `mcu-4layer`** — it scales
  with how many distinct KiCad footprint libraries a design touches. It is still the
  largest single cost on seven of the eleven examples, and nobody has looked at it
  in two milestones.
* **Nothing checks that `stackup.planes` and `pours:` agree** — M10 raised it, M11
  made it matter (a `reference:` layer is now validated to be *poured*, which is
  half the check), and it is still not closed in general.
