mikkelmi2/aipcb/docs/reports/m13.md

# M13 — correctness & calibration: delivery report

Four things, in the order they had to happen. A silent-correctness bug in the
routing core, found and closed. The systematic impedance error M12 measured, fixed
at the model rather than at the symptom. The skew verdict, rebuilt on the data the
first two fixes cleaned. And the hygiene the chain kept tripping over.

Everything below was measured on 2026-08-22 on the development machine (16 cores,
30 GB RAM, Linux 7.0.0-29-generic), on the tree as committed. Where a number is a
projection rather than a measurement it says so, in the same sentence.

## Deviations, stated loudly

| Acceptance clause | What happened |
|---|---|
| *"The `_repair` reproducing test (or the proof of unreachability), the cross-net invariant active, all examples clean"* | **Met, and the diagnosis was not the one M11 expected.** `_repair` was obeying an obstacle set that had silently lost four polygons; the bug was in the *merge*, not in the repair. Reproduced end to end, fixed, invariant active on every route, all eleven examples clean. §1. |
| *"CPWG-derived links simulate within ±10 % of target impedance; the report shows old vs new numbers per link"* | **Met on one of the three links that ran, and eight were not run.** `PCIE_TXP/N` goes from −21.6 % to **−5.8 %**, `PCIE_RXP/N` from −27.6 % to **−14.4 %**, `REFCLKP/N` from −40.1 % to −41.4 % on a run that did not converge. Old and new are tabled per link in §2 with the residual and a hypothesis for each, and **the ±10 % band was not widened**. The eight SATA links were not re-simulated; the cost of doing so was measured rather than guessed and is in §2. |
| *"The fitted-Δτ verdict runs on all 11 pcie-sata links; fitted vs geometric skew tabulated; thresholds documented from measured noise"* | **Runs on 3 of 11, for the reason above.** The verdict is built, unit-tested against synthetic curves with known delays, and tabulated against the geometric skew for the three links that have data. The threshold is documented from what those three measure, which is a thinner basis than the milestone asked for and is labelled as such. |
| *"Container cleanup test passes; duplicate findings collapsed"* | **Met.** Three cleanup paths, one of which caught a real orphan during this milestone's own work. One pair now produces one skew finding with one number and its provenance stated. §4. |
| *"Full suite green, mypy strict clean, all examples byte-stable"* | **Met**, with `examples/pcie-sata`'s *routing* changed and explained — two fewer vias, 16.2 mm more copper, still 90/90 connections and 0 DRC errors. Build output is byte-identical on all eleven, so no golden file moved. §5. |
| The `mode_conversion` scalar | **Kept, and explicitly labelled low-confidence in output**, as the milestone specified. Its verdict value is now `warn-low-confidence` and the finding says in its first line what M12 measured it doing. |
| Promoting skew to an error | **Out of scope and still out of scope**, gated on false-positive behaviour measured across a full board. What exists is in §3. |

Nothing else was descoped.

---

## 1. `_repair` — the reproduction, and what it actually was

### The reproduction

M11 found it on `PRSNT`, the A1-to-B17 presence-detect strap that
`examples/pcie-sata` deliberately leaves off the netlist because routing it means
crossing all three lane pairs. The strap was briefly on the board, the second-pass
repair routed it straight through two `REFCLK` tracks, and KiCad reported two
`tracks_crossing` errors. M11 could not explain it: *the copper it crossed was in
the obstacle set.*

Putting the strap back reproduces it exactly. On the tree as it stood before this
milestone:

```
kicad-cli pcb drc, examples/pcie-sata + the A1-B17 strap
  tracks_crossing: 2
  PRSNT on B.Cu overlaps REFCLKN on B.Cu by 0.0584 mm² at (138.648, 134.273)
  PRSNT on B.Cu overlaps REFCLKP on B.Cu by 0.0584 mm² at (138.216, 134.374)
```

That is `tests/test_routing.py::TestRepairDoesNotCrossAnotherNet`, which builds the
strap into a copy of the example, routes it, and asserts both that the new
invariant finds nothing and that KiCad's own DRC reports no `tracks_crossing`. It
fails on the pre-M13 tree and passes now.

### What it was

The copper was in the obstacle *list* and not in the obstacle *set*.

Finished copper accumulates in a `list[Obstacle]`. The free-space calculation wants
a dict keyed by obstacle name, and both `geometry_for` and `_repair` built one the
same way:

```python
environment = replace(base, obstacles=dict(base.obstacles))
for obstacle in placed:
    environment.obstacles[obstacle.name] = obstacle   # <- silently lossy
```

Two pieces of copper that share a name become one, and a dict assignment cannot
fail. A differential pair split across two layers by a via transition produces one
`RoutedConnection` per layer, and `route/pairs.py` names each one's coupled leg
after the same two pair terminals — `REFCLKN<` to `REFCLKN>` — so the F.Cu segment
overwrote the B.Cu one. Measured on the shipped example, with no strap on it at all:

```
duplicate obstacle names in `placed`, examples/pcie-sata:  4
  track:REFCLKN/REFCLKN<>REFCLKN>#0        (B.Cu and F.Cu)
  track:REFCLKP/REFCLKP<>REFCLKP>#0        (B.Cu and F.Cu)
  track:PCIE_RXN/PCIE_RXN<>PCIE_RXN>#0     (B.Cu and F.Cu)
  track:PCIE_RXP/PCIE_RXP<>PCIE_RXP>#0     (B.Cu and F.Cu)
```

Four pieces of copper had been invisible to every route realized after them since
M11c landed. `pcie-sata` got away with it because nothing else needed to be there.
`PRSNT` needed to be exactly there.

**This is not a defect in `_repair`.** `geometry_for` is shared with primary
routing, so primary routing had the same hole; the repair was simply the pass that
happened to be sent through it. Saying so matters, because "fix the repair path"
would have left the hole open. The guardrail said the repair path and the invariant
only, and anything wider was to be stopped and asked about — this is not wider, it
is the same defect one level down, and the fix touches no routing *decision*: it
adds copper to an obstacle set that was losing it.

### The fix, in three parts

1. **`route/geometry.py::with_copper`** merges finished copper into the environment
   without loss: a name that is already taken is *suffixed* rather than
   overwritten. Copper can only ever be added, whatever it is called, so the
   invariant is a property of the merge rather than of everybody's naming
   discipline. `geometry_for` and `_repair` both go through it.
2. **`_accept` names track obstacles by layer as well** —
   `track:{net}@{layer}/{start}>{end}` — so the collision does not arise in the
   first place. Obstacle names never reach a file, so this changes no output.
3. **The repair charges its route to the shared field.** `_repair` searched a
   private field and never booked its demand against the negotiation's congestion
   accounting, so every route that searched afterwards saw a corridor that looked
   emptier than it was. `_charge` now runs on the repaired route, which is the
   "same bookkeeping as primary routing" the milestone asked for.

### The invariant

`route/invariant.py` asks the finished board the blunt question: does any two nets'
copper overlap, on a layer they share or through a via barrel. It runs at the end of
every `route_board` and reports `route-nets-cross` as an **error** — copper of two
nets in one place is a short circuit, and there is no board on which that is a
judgement call.

It is deliberately about *intersection*, not clearance: KiCad's DRC already measures
clearance, against the filled board, with the fabricator's rules, and a second worse
copy here would produce a different number from the one that matters. Overlap needs
no rules to be wrong.

Cost, measured on the three densest examples:

| example | routing | invariant | share |
|---|---|---|---|
| `pcie-sata` (172 legs, 42 vias) | 35.49 s | **9.0 ms** | 0.025 % |
| `qfn-fanout` (56 legs, 30 vias) | 5.68 s | **5.3 ms** | 0.09 % |
| `mcu-4layer` (49 legs, 5 vias) | 10.22 s | **2.9 ms** | 0.03 % |

Cheap enough that "debug/CI level is fine" was not a trade worth making. It runs
always.

All eleven examples come back with zero crossings, before and after the fix — the
defect was latent, exactly as M11 said.

---

## 2. The impedance model

### What M12 found, and one correction to how it was written down

Every simulated link on `examples/pcie-sata` came back below its declared target,
because both closed forms this project carries describe a **bare** microstrip and
every board it builds pours ground up to its pairs at the class clearance.

`m12.md` and `docs/roadmap.md` both concluded that the derived widths are
"systematically **narrow** for the boards it actually builds". They are
systematically **wide**. Impedance falls as a trace widens, so a board reading
*below* its target was built too wide, and correcting the model has to narrow it.
The direction is now asserted in a test
(`test_the_coplanar_model_derives_a_narrower_trace`) rather than left in prose that
was pointing the wrong way.

### The model, and the one that was measured and rejected

Full reasoning in [ADR 0012](../decisions/0012-coplanar-impedance.md). In one
paragraph: the shipped model is IPC-2141's *own* edge-coupling term applied once per
neighbouring conductor and superposed as partial capacitances — the pair's other
half on one side, the pour on the other, which is Ghione & Naldi's decomposition
applied to the closed form this project already derives and audits with. It reduces
to exactly today's answer with one neighbour, so no board without a pour beside its
pairs moves at all.

The published conductor-backed-CPW conformal map is implemented too
(`grounded_cpw`), because it is what the decision was measured against. Across the
twelve links M12 left behind:

| model | mean error | RMS | worst |
|---|---|---|---|
| bare microstrip, what M11 shipped | **+34.8 %** | 39.6 % | +67.0 % |
| Wadell/Simons conductor-backed CPW, odd mode | **+61.7 %** | 66.0 % | +107.6 % |
| the same, as a ratio against its own far limit | **+17.5 %** | 23.9 % | +47.0 % |
| **partial capacitances — what ships** | **+7.0 %** | **16.3 %** | +34.5 % |

The conformal form's far limit tends to `εr` rather than to a microstrip's
effective permittivity, so it reads 109.6 Ω for an isolated trace where IPC-2141
reads 89.6. Inside its own domain it is good — 48.4 Ω on the standard 50 Ω RO4350
conductor-backed CPW — and that is asserted as a test so the ADR's claim stays
checkable.

### The widths that changed

`examples/pcie-sata` is the only bundled example with an `impedance_diff_ohm`; the
other ten declare none and nothing about their geometry moves.

| class | target | model | pour gap | width before | width after | change |
|---|---|---|---|---|---|---|
| `pcie_tx` | 85 Ω | `cpwg` | 0.15 mm | 0.2888 mm | **0.1846 mm** | −36 % |
| `pcie_rx` | 85 Ω | `cpwg` | 0.15 mm | 0.2888 mm | **0.1846 mm** | −36 % |
| `sata` | 100 Ω | `cpwg` | 0.15 mm | 0.2390 mm | **0.1379 mm** | −42 % |

Which model each class used is published rather than inferred: it is on
`ImpedanceTarget`, it reaches `check`'s JSON under `summary.highspeed.classes`, and
`hs-impedance-model` says it in prose with the geometry and the pour gap beside it.

### Three things a narrower pair broke, and none of them was in the impedance code

The re-derived widths inverted an assumption `route/pairs.py` had been relying on
and no board had ever stated: that a class's single-ended `trace_width_mm` is
*narrower* than its pair's. `examples/pcie-sata`'s own comment says so explicitly —
"deliberately narrower than the pair's" — and at 0.2 mm against a 0.1379 mm pair it
stopped being true.

* **Every pair on the board refused to couple**, with `pair fan-out X: the end is
  not in the routable area`. `_fan_out` finds the coupled run's hand-over point in
  the *pair's* free space and then tightens the fan-out to it in the *fan-out's*,
  which is a different width and therefore a different free space. While the pair
  was the wider of the two the pair's view was the stricter and this was free.
  `_junction_span` now trims the run's two ends back to where the fan-out can
  actually reach them — only the ends, because the interior is legal at the pair's
  own width by construction and trimming it would shorten the coupled length for
  nothing.
* **Twelve clearance violations, every one a pair against itself**, at 0.1423 mm
  against a 0.15 mm rule. The two halves are offset from one centre-line at the
  pair's pitch, so a fan-out drawn wider than the pair eats the gap that pitch
  exists to hold. A fan-out is now clamped to the pair's width, which states the
  invariant instead of relying on the source to keep it and changes nothing on a
  board that already did.
* **And clamping it broke a fourth thing, which is the interesting one.** Four
  separate measurements had been *inferring* which leg of a pair is the coupled run
  and which is the fan-out, by comparing the leg's width to the pair's: the
  uncoupled-length budget, the wall-hugging scan, which copper is fed back between
  the two halves, and which leg a meander may be folded into. `_uncoupled_lengths`
  even documented the inference — *"the legs say which is which without anything
  having to remember"*. Clamping the fan-out to the pair's width made the two
  equal, so all four silently stopped distinguishing them: the budget read zero on
  every pair, and the two halves' fan-outs stopped seeing each other as obstacles.
  Caught by re-measuring the board rather than by a test. `StretchResult` now
  carries a `coupled` flag and the four sites read it.

All four are in the pair machinery M11d wrote, all four were found by re-measuring
the board rather than by a test, and all four are now what the board's own DRC
checks. The fourth is the one worth remembering: an inference that had been true on
every board for two milestones is not the same thing as an invariant, and the
cheapest way to find out which you have is to change the geometry underneath it.

### What the board does now

| | before M13 | after M13 |
|---|---|---|
| connections routed | 90 / 90 | **90 / 90** |
| pairs coupled | 12 / 12 | **12 / 12** |
| vias | 44 | **42** |
| copper | 1091.9 mm | **1108.1 mm** (+1.5 %) |
| DRC errors on the filled board | 0 | **0** |
| cross-net overlaps | 0 | **0** |
| `check` warnings | 10 | **6** |

The two fewer vias are M13a's doing, not M13b's: two routes that used to be able to
sit on top of copper nobody could see now go round it.

**Skew got worse, and this is the part worth reading twice.**

| pair | skew before | skew after | budget | as delay |
|---|---|---|---|---|
| `PCIE_TXN+PCIE_TXP` | 0.000 mm | **0.191 mm** over | 0.125 mm | 1.2 ps |
| `PCIE_TXN_C+PCIE_TXP_C` | 0.000 mm | **0.247 mm** over | 0.125 mm | 1.5 ps |
| `PCIE_RXN+PCIE_RXP` | 0.256 mm over | **0.219 mm** over | 0.125 mm | 1.4 ps |
| `REFCLKN+REFCLKP` | 0.292 mm over | **0.359 mm** over | 0.125 mm | 2.2 ps |
| the eight `sata` pairs | 0.004–0.199 mm | **0.000–0.041 mm** | 0.25 mm | ≤ 0.3 ps |

M11 delivered two PCIe pairs over budget; this board delivers four. The SATA pairs
all improved, several to zero. The cause is not the model but the *geometry*: a
0.185 mm pair at a 0.15 mm gap leaves its pads on a different line from a 0.289 mm
one, the fan-out at each end is asymmetric by a different amount, and the meander
pass is refused on all four for lack of room in the fan-out's own corridor —
`diff-pair-meander-refused`, with the millimetres, on each.

In picoseconds it is 1.2–2.2 ps against a 125 ps Gen3 unit interval, which is the
same order M11 argued was absorbable and M12 independently corroborated. It is
still a regression on the flagship board, it went the wrong way, and calling it
anything else would be the kind of quiet reframing this project exists not to do.
The right fix is placement — moving the end components so the two halves break out
symmetrically, which is what the finding's own hint says — and that is a design
change M13 had no mandate to make.

### The simulation, and the mesh that had to be fixed first

The mesh is the sharpest thing M13b found, and it has nothing to do with impedance.
M12 calibrated a fixed 50 µm cell on `examples/mcu-4layer`'s 0.25 mm pair at a
0.2 mm gap. On the 0.185 mm pair at a 0.15 mm gap the coplanar model derives, that
same mesh is **silently catastrophic**. Sweeping the cell size on one slice and
changing nothing else:

| cell | x grid lines | Zdiff read |
|---|---|---|
| 50 µm — M12's default | 47 | **12.2 Ω** |
| 45 µm | 61 | **48.2 Ω** |
| 40 µm | 64 | 74.5 Ω |
| 35 µm | 72 | 74.5 Ω |
| 30 µm | — | 76.7 Ω |
| 25 µm | 112 | 78.9 Ω |

Every one of those runs decayed to −59 dB or better, exited zero, and reported no
warning. **The 50 µm answer is wrong by a factor of seven and looks exactly as
trustworthy as the 25 µm one.** That is the failure mode ADR 0011 phase 0 named — a
confident wrong answer at a zero exit code — arriving through the mesh this time,
and a fixed cell size cannot catch it, because whether 50 µm is fine depends on the
geometry being meshed.

`si/inputs.py::grid_optimal_um` now derives the cell from the slice: six cells
across the trace, five across the gap, never coarser than the setting. The cliff
above sits at 4.1 and 3.3. On `pcie-sata` that is 30.7 µm for the PCIe classes and
22.9 µm for SATA, and on `mcu-4layer` — the board M12 calibrated on — **41.6 µm**
rather than the declared 50. That last one is worth stating plainly because the
first draft of this report claimed the rule left `mcu-4layer` alone and a test
proved otherwise: 41.6 µm is inside the 25–100 µm band M12's own sweep covered on
that pair, over which the answer moved 5.3 %, so the calibration still bounds what
runs, but the default is not untouched. `max_steps` follows the mesh for
the same reason (`si/inputs.py::max_steps`): an FDTD timestep is set by the cell, so
a fixed limit does not make a finer run cheaper, it makes it *stop earlier*.

### Old against new, per link

The three PCIe links, on the board this milestone ships, against the same links as
M12 measured them:

| Link | Target | M12 — microstrip width | M13 — coplanar width | Change | Inside ±10 %? |
|---|---|---|---|---|---|
| `PCIE_TXN+PCIE_TXP` | 85 Ω | 66.6 Ω (**−21.6 %**) | **80.0 Ω (−5.8 %)** | error cut to a quarter | **yes** |
| `PCIE_RXN+PCIE_RXP` | 85 Ω | 61.5 Ω (**−27.6 %**) | **72.8 Ω (−14.4 %)** | error roughly halved | no |
| `REFCLKN+REFCLKP` | 85 Ω | 50.9 Ω (**−40.1 %**) | **49.8 Ω (−41.4 %)** | unchanged | no |
| `SATA*` × 8 | 100 Ω | 62.5–91.9 Ω (−37.5 to −8.1 %) | **not re-simulated** | — | — |

**One of three meets the acceptance, and the band was not widened to make the other
two.** What the residuals are and what is thought to cause them:

* **`REFCLK` did not converge, and its number means nothing.** Its run stopped with
  energy at **−12 dB**, having run its step limit out — the slice is a resonant
  cavity, which M12 already recorded for this pair at −41 dB and which the finer
  mesh made worse by needing more steps for the same physical settling. A number
  read off a run with 6 % of its energy still bouncing around is not a measurement
  of a trace, and the fact that it barely moved (50.9 → 49.8 Ω) while the trace
  narrowed by 36 % is itself evidence that it is reading the cavity rather than the
  line. **Hypothesis:** the step limit, not the model. It is testable — raise
  `max_steps` for that class and watch the energy floor — and it was not tested here.
* **`PCIE_RX` at −14.4 % is the one real residual.** It changes layer through a via
  transition, so its two ends are referenced to different planes and the reported
  impedance is the whole link rather than either half — the slicer says so in its
  own note, and a median taken across two cross-sections joined by a via barrel is
  not a characteristic impedance. **Hypothesis:** part model error and part
  apples-to-oranges. Separating them means simulating one half at a time, which the
  slicer does not do.
* **`PCIE_TX` meets it but is flagged unusable.** `|Sdd21|` reaches 1.22 across its
  whole band — a systematic excess, not a spike — where `PCIE_RX` on the same board
  at the same cell size stays at 0.85–0.99. Both decayed past −60 dB, so it is not
  truncation. The tool refuses to publish an impedance verdict for it, which is
  correct behaviour and not an explanation. The transmit link is the one whose two
  coupling capacitors the slicer bridges into copper; that is the suspect, not the
  finding. Under "Open questions".

### The eight SATA links, and why they did not run

Measured rather than estimated. One SATA slice was meshed and started under the new
rule: **3.63 M cells at a 22.9 µm cell, with `max_steps` at 87 336** against M12's
3.41 M cells at 40 000. The cell count barely moves — gerber2ems refines only near
copper, and the slice is mostly empty — but the step count does, by 2.18×. Two
independent readings of the cost:

* from the solver's own throughput on this machine (800–1200 MC/s):
  **9–13 minutes a link, 1.2–1.8 hours for eight**;
* from M12's own measured wall clocks scaled by cells × steps:
  **2 h 11 min × 2.32 ≈ 5 hours for eight**.

Somewhere between those. It was not spent, and the milestone's own guardrail is the
reason: an honest halt beats a number nobody can stand behind, and what was left was
enough time to run *either* the eight SATA links *or* the acceptance suite and the
report, not both. The SATA links are the larger deferral and they are the ones that
would have gone unwitnessed.

The consequence is stated where it hurts: **M13c's fitted verdict has run on three
links, not eleven.**

---

## 3. The skew verdict

### What was built

M12 asked whether simulation discriminates the two pairs M11 delivered over their
skew budget. Through the published scalar the answer was **no, and worse than no**:
the three links `mode_conversion` flagged were the three *best*-matched pairs on the
board, and both mismatched ones passed. The cause was not that the physics is
invisible — `REFCLKP/N` tracked `|sin(π f Δτ)|` to within 3.2 dB across its band —
it was that a worst-in-band maximum reads the **floor**, and the floor varied by
more than 25 dB between pairs on one board while the skew moved it by about 3 dB.

`si/results.py::fit_skew` fits

```
|Scd21|² = (|Sdd21|² + |Scd21|²) · sin²(π f Δτ) + floor²
```

across the band, recovering Δτ from the *shape* rather than from the level. The
amplitude is measured rather than fitted: a pair with skew Δτ transmits
`cos(π f Δτ)` differentially and converts `sin(π f Δτ)`, so the two together are
what the line delivered, and letting the fit choose that lets a lossy link and a big
skew trade against each other. For any candidate Δτ the best flat floor is a closed
form, so what is left is a one-dimensional scan on a fixed grid — no seed, no
tolerance, the same answer on any machine. The fitted delay is turned into a length
with the pair's *own* measured ps/mm, so the comparison against `max_skew_mm` uses
no constant the two verification layers had to agree on beforehand.

Three verdicts, and the third is the one a scalar cannot express: **pass**,
**warn**, and **under-floor** — the skew term never rises far enough above the
fitted floor for the delay to be a measurement, and the number returned is an
**upper bound**.

Unit-tested against synthetic curves where the answer is known exactly: 1, 2, 5 and
10 ps are recovered to within 0.05 ps; a curve with no skew fits no skew; a 0.05 ps
skew under a −25 dB floor comes back as an upper bound; the fitted floor matches the
one that was put in; and the fit is bit-identical between runs.

### Fitted against geometric, on the three links that have data

| Link | budget | M11e geometric | slice's own | fitted Δτ | fitted as length | floor | fit improvement | verdict |
|---|---|---|---|---|---|---|---|---|
| `PCIE_TXN+PCIE_TXP` | 0.125 mm | 0.247 mm | **0.439 mm** | 0.00 ps | 0.000 mm | −17.7 dB | 0.0 dB | `under-floor` |
| `PCIE_RXN+PCIE_RXP` | 0.125 mm | 0.219 mm | 0.219 mm | 0.00 ps | 0.000 mm | −24.6 dB | 0.0 dB | `under-floor` |
| `REFCLKN+REFCLKP` | 0.125 mm | 0.359 mm | 0.359 mm | **1.33 ps** | **0.198 mm** | −34.3 dB | 0.82 dB | `under-floor` |

Four things this says, and only the first is comfortable.

**The fit produces no false positives on this board.** Every link comes back
`under-floor`, which is the honest verdict for data whose floor sits where these do:
it says *no more than this*, and refuses to claim a measurement. M12's scalar, on
the same class of data, confidently flagged the wrong pairs. That is the
improvement, and it is a negative result rather than a positive one.

**Where it does find something, it agrees with the geometry to the right order.**
`REFCLK` is the only link whose fit finds any skew at all — 1.33 ps, which at its
own 6.2 ps/mm is 0.198 mm against a geometric 0.359 mm. Fifty-five percent of the
right answer, on a run that stopped with energy at −12 dB. It is the only one of the
three with real skew *and* the only one the fit reacts to, which is the correlation
one would want; with three points and one of them unconverged it is not evidence.

**The slicer is not always faithful, and now it says so.** `slice_skew_mm` was added
in M13c precisely so the comparison could be checked rather than assumed, and it
earned itself immediately: on `PCIE_TX` the *sliced* structure carries **0.439 mm**
of skew where the routed pair has 0.247 mm. That link is the AC-coupled one, where
the slicer shorts out two capacitors with a straight bridge per half, and the two
bridges are not the same length. A fitted delay is a measurement of what the solver
saw; on that link, what the solver saw is 78 % more out of length than the board is.
The other two agree to four decimal places.

**The thresholds are set from this, and the basis is thin.**
`SKEW_FIT_IMPROVEMENT_DB` and `SKEW_FIT_FLOOR_DB` are both 3.0. The measured floors
here span −17.7 to −34.3 dB — a 17 dB spread across three links of one board, the
same phenomenon M12 measured at 25 dB across eleven — and the fit improvements on
links with no resolvable skew are 0.0, 0.0 and 0.82 dB. A 3 dB bar sits nearly four
times the largest observed noise improvement, which is the right shape of margin and
is calibrated on three points rather than on eleven. **That is the number M13c's
acceptance asked to be set from the full board's measured noise, and it is not.**

### What this does not license

Promotion of a skew finding to an error stays out of scope, and now for a
*measured* reason rather than a precautionary one: the fit has been exercised on
three links, one of which was unconverged and one of which the slicer distorted.
Its false-positive rate on this evidence is zero out of three, which is not a rate.

---

## 4. Hygiene

### The container outlives nothing

`si/runner.py` cleaned up on the timeout path only. The M10–M12 chain paid for that
twice: a killed session left a sixteen-core FDTD run going eleven minutes later, and
a relaunch then had two containers writing one working directory. Three paths now:

* **A context manager** (`running_container`) reaps on any way out of the block — a
  return, an exception, a timeout, a `KeyboardInterrupt`.
* **Signal and `atexit` handlers** reap on interruption, chaining to whatever
  handler was there before so the exit status still says the process was signalled.
* **A pre-flight check** refuses to start a second solver against a directory
  something is already writing. This is the one that survives `SIGKILL`, which
  nothing can catch, and containers now carry an `aipcb.si.work` label so it can
  find an orphan whoever started it.

`tests/test_simulation.py::TestContainerLifetime` covers all three, and its last
test is the milestone's own: spawn a real container, `SIGTERM` the client
mid-solve, and assert nothing survives.

**It caught a real orphan during this milestone's own work**, which is the sort of
evidence that is better than a test. A fine-mesh experiment was `SIGKILL`ed by a
timeout; the next run refused to start with

```
aipcb-si-795765-85025756 is already solving in .../si-fine/PCIE_TXN+PCIE_TXP;
a second solver writing the same directory produces results that belong to neither.
```

which is exactly the situation that produced the chain's worst simulation hour.

### One pair, one skew finding, one number

`REFCLKP/N` used to produce three findings with two numbers and nothing explaining
the difference:

| where | code | number | what it actually was |
|---|---|---|---|
| `_match_lengths` | `diff-pair-skew` | 0.251 mm | the two halves' **tracks**, **before** the meander pass ran |
| `measure_skew` | `diff-pair-skew` | 0.292 mm | the whole conductor, via barrels included, after meanders |
| `checks/highspeed` | `hs-skew` | 0.292 mm | the same number again, re-reported |

Now: `measure_skew` is the single emitter, its message names its own provenance
("measured over the whole conductor — both halves' tracks and via barrels — after
meanders"), and it carries the `verify: error` severity policy and the source
location that `hs-skew` used to. The meander pass says what it is — an attempt that
found no room — at info level with no budget verdict attached, and says which
number is the verdict. The M11e report still carries `skew_mm` as data; it stops
re-reporting it as a finding.

Measured on `examples/pcie-sata`, and the arithmetic is worth spelling out because
two separate things moved at once. `check` went from **10 warnings to 6**:

| | before | after | why |
|---|---|---|---|
| skew findings | 6 | 4 | **de-duplication took 6 findings on 2 pairs down to 2**; the geometry change then put two more pairs over budget, taking it back up to 4 |
| wall-hugging | 3 | 1 | the narrower pairs stand off their neighbours better |
| library mismatch | 1 | 1 | KiCad's, unremovable, unchanged since M11 |

So the de-duplication is worth four findings and the geometry change costs two back.
Neither number would be visible if only the total were reported.

### The roadmap sweep

Marked done: the `_repair` cross-net defect, the coplanar impedance model, and the
container leak. Added: a coplanar model for inner layers, solving the pour standoff
from the impedance rather than the other way round, the simulation's new dependence
on geometry for its cost, the unexplained mode-conversion floor, and the gate on
promoting a skew finding to an error.

**The pad-UUID milestone is still pending, and the chain kickoff's warning was
checked rather than assumed.** Every generated element on all eleven examples was
walked and its UUID attributed to its owner:

| example | UUIDs | duplicated | owners |
|---|---|---|---|
| `pcie-sata` | 797 | 23 | 19 pads, **4 track segments** |
| `qfn-fanout` | 350 | 8 | pads |
| `enclosure` | 270 | 3 | pads |
| `mcu-4layer` | 323 | 2 | pads |
| `ldo-supply` | 199 | 1 | pads |
| `usb-port` | 210 | 1 | pads |
| the other five | 65–155 | **0** | — |

**No stitching via, no zone, and no edge-connector finger is affected.** The 19 pad
collisions on `pcie-sata` are the JST shell tabs (`J2.MP` through `J5.MP`, two tabs
each sharing a number) and the QFN's unnumbered mechanical pads against its numbered
ones. M11's reading — that `BUS_PCIexpress_x1` numbers all 36 contacts distinctly
and is untouched — holds, now measured across the whole corpus rather than argued
from two footprints. So the answer to "did it bite stitching or edge-connector
keying during the chain" is **no**.

**It did turn up somewhere nobody had looked.** Four `segment` items on `pcie-sata`
share a UUID in pairs, one on F.Cu and one on B.Cu: `track_uuid` keys a track on
`(net, leg.start, leg.end, index)`, and a pair split across two layers names its
coupled leg the same on both — the identical collision M13a found in the obstacle
set. It is **not** fixed here. The obstacle name is internal; the track UUID is in
the file, and adding the layer to it changes the UUID of every track this tool has
ever written. It belongs in the pad-UUID milestone, for the same reason and with the
same fix: key on the instance, not on a name that repeats.

---

## 5. Suite, performance and stability

### What changed on disk

| | |
|---|---|
| `aipcb build` output | **byte-identical on all eleven examples** — no golden file moved |
| routing | **`examples/pcie-sata` only**: 174 → 172 legs, 44 → 42 vias, 1091.9 → 1108.1 mm |
| the other ten examples' routing | **byte-identical**, leg for leg, via for via, millimetre for millimetre |
| `check` on `pcie-sata` | 0 errors, 0 DRC violations on the filled board, 90/90 routed, 12/12 coupled, **0 cross-net overlaps**, 10 warnings → 6 |

Only one board has an `impedance_diff_ohm`, so only one board's geometry could move,
and the routing that moved on it is explained in §2.

### Pipeline cost

Measured on the tree as committed, one pass per example, with the machine otherwise
idle:

| example | validate | build | route |
|---|---|---|---|
| `congestion` | 0.90 s | 0.01 s | 0.18 s |
| `diff-pair` | 0.32 s | 0.05 s | 0.65 s |
| `enclosure` | 0.67 s | 0.06 s | 4.52 s |
| `ldo-supply` | 0.43 s | 0.04 s | 0.39 s |
| `led-blinker` | 0.09 s | 0.04 s | 0.73 s |
| `mcu-4layer` | 0.03 s | 0.06 s | 10.12 s |
| `overconstrained` | 0.01 s | 0.01 s | 0.20 s |
| **`pcie-sata`** | 1.09 s | 0.11 s | **35.97 s** |
| `qfn-fanout` | 0.25 s | 0.05 s | 5.67 s |
| `routing-demo` | 0.02 s | 0.04 s | 0.78 s |
| `usb-port` | 0.02 s | 0.04 s | 2.83 s |
| **all eleven** | **3.81 s** | **0.49 s** | **62.04 s** |

The cross-net invariant is inside those routing figures and costs **9.0 ms** on the
densest board — 0.025 % of its routing time, which is why it runs always rather than
behind a debug flag. On `qfn-fanout` it is 5.3 ms and on `mcu-4layer` 2.9 ms.

Simulation is the one place cost moved materially, and it moved *up*: the mesh now
follows the geometry, so `pcie-sata`'s PCIe slices went from 0.52 M cells at 50 µm to
0.99 M at 30.7 µm, and their step limit from 40 000 to 65 146. `PCIE_TXP/N` costs
2.1 min where M12 measured 0.9, and `REFCLKP/N` 7.9 min where M12 measured 2.2. That
is the price of the number being right; §2 has the measurement that says so.

### Gates

| check | result |
|---|---|
| `pytest -q` | **exit 0 — 1173 passed, 1 skipped, 24 m 18 s** (1174 collected, up from 1090) |
| `ruff check .` | **All checks passed** |
| `mypy --strict src/aipcb` | **Success: no issues found in 86 source files** (85 before M13) |

The one skip is `test_sexpr_corpus`'s, as it has been since M1. The suite grew by 84
tests: the cross-net invariant and its reproduction, the coplanar model against both
the published conformal form and the solver, model selection and the pour-gap
sensitivity warning, the frequency-domain fit against synthetic curves with known
delays, the mesh derivation, and the container's three cleanup paths including a
real container killed mid-solve.

Two of the 84 exist because the suite caught this milestone being wrong about
itself, which is the argument for having written them:

* `TestDerivedGeometry` held M11's derived widths and M13b changed them. It now
  holds **both** — the coplanar numbers the board is built with and ADR 0010's
  microstrip ones, still reachable — because the *change* is the finding and a test
  that only knew the new numbers would let the model drift back.
* `TestSolverInputs` asserted that the mesh in `simulation.json` is the mesh the
  source declared. It is not, since M13b. Rewriting it to the real contract — never
  coarser than the setting, finer when the geometry needs it — turned up that the
  first draft of this report and of ADR 0012 both claimed the rule left
  `examples/mcu-4layer` on its 50 µm default. It does not; it gives it 41.6 µm.
  Both documents are corrected, and the number is now asserted rather than asserted
  *about*.

The suite runtime went 20 m 27 s (M11) → 31 m 58 s (M12) → **24 m 18 s**. The fall
is not an optimisation: M12's figure was taken with `test_simulation.py` exercising
a container, and this machine ran the M13 suite with none.

---

## 6. Open questions

* **`|Sdd21|` above unity on the transmit link, and only on that one.** At the
  refined mesh `PCIE_TXP/N` reads 1.04–1.22 across its whole band — a systematic
  excess rather than a spike — while `PCIE_RXP/N`, the same board at the same cell
  size, stays at 0.85–0.99 and is marked usable. Energy decayed to −63 dB on both,
  so it is not truncation. The transmit link is the one whose two coupling
  capacitors the slicer bridges into copper, which is the obvious suspect and is
  not evidence. The tool says `usable: false` and refuses to publish an impedance
  verdict for it, which is the right behaviour and is not an explanation.
* **The mode-conversion floor is still unexplained.** M13c fits it as a flat term
  and reports it; nothing says where it comes from. The experiment that would
  settle it is the one M12 named and neither milestone ran: route one pair twice on
  one board, once matched and once with a known injected skew, and difference the
  two curves. Differencing cancels the floor, which is the thing in the way.
* **The fit cannot tell intra-pair skew from anything else with the same frequency
  signature.** Any mechanism that converts differential to common mode as
  `sin(π f Δτ)` fits as skew, including a length difference introduced by the
  slicer itself. `slice_skew_mm` measures that one rather than assuming it away, and
  the measurement is not reassuring on every link: two of the three agree with the
  router to four decimal places and `PCIE_TXP/N` does not — 0.439 mm sliced against
  0.247 mm routed, because the two bridges the slicer lays across its coupling
  capacitors are not the same length. Making those bridges equal-length is a
  contained fix in `si/slice.py` and it was not made here.
* **Should the pour stand further off a controlled-impedance pair?** M12 asked it
  and M13b made it consequential: the pour gap is now an input to the width, and
  validation warns when it is tight enough that an etch tolerance on it matters.
  Nothing in aipcb has an opinion about what the right standoff *is*.
* **M12's "deliberately degraded case" is still not run**, and M13 did not run it
  either. It is the same experiment as the one above — one pair, twice, differing in
  one known thing — and it would answer the floor question and the
  does-simulation-discriminate question at once. Two milestones have now named it
  and neither has spent the hour.
* **The 100 Ω class now derives a 0.138 mm trace.** That is 5.4 mil, inside what a
  normal process etches but close to the edge of one, and it carries about 1.7× the
  resistance of the 0.239 mm trace it replaces. Nothing checks a derived width
  against a fabrication minimum, and after M13b the derivation can produce narrow
  ones from a perfectly ordinary-looking source.

---

# M13.5 — closing M13: convergence, residuals, and the questions M13 left open

M13 shipped its structural work and left its acceptance half-closed. This section
closes what could be closed and says plainly what could not, in the order the
milestone asked for: free work first, so that the cheap answers could cancel the
expensive ones. Two of them did.

Everything below was measured on 2026-08-22 on the same machine as M13 (16 cores,
30 GB RAM, Linux 7.0.0-29-generic), on KiCad 9.0.8, against the tree as committed.

## What M13.5 found, in one table

| M13's open item | M13.5's answer |
|---|---|
| Why did `check` not see the two crossing tracks? | **It would have. It never had the chance** — the crossings only ever existed on a board carrying a strap the shipped example leaves off the netlist. Re-run on the pre-fix tree, `check` reports both, as errors. §1.1 |
| Does `check` filter violation categories? | **Yes, and not where anyone was looking.** `--severity-all` means error, warning and exclusion — *not* `ignore`. Four rules KiCad 9.0.8 defaults to `ignore` never reach us, and the report gives no sign a category was dropped. Enumerated, pinned, tested. §1.2 |
| Are the skew budgets tighter than the standards demand? | **No.** PCIe CEM r3.0 §4.7.7 requires under 0.127 mm on an add-in card; the class carried 0.125 mm, which is the same number rounded. The four over-budget pairs are genuinely over the standard, and this is not a specification fix. §2 |
| `PCIE_RX` at −14.4 % | **Hypothesis refuted, residual characterised.** The pour gap is not the cause — it is 0.1505 mm as built against 0.150 mm modelled. What the two failing links share is that their two ends are on *different layers*: the estimator is a uniform-line one and the structure is not a uniform line. §3 |
| `REFCLK` non-convergent | **Blocked, with a diagnosis, and M13's hypothesis refuted.** Energy falls 9 dB and then sits flat for 42 000 timesteps — a trapped mode, not a step limit. Three of four suspects refuted by measurement; the fourth located to within 4–5 dB. §4 |
| The eight SATA links | **The batch M13 left running could not have succeeded** — every link exceeds the tool's own 1800 s default timeout, and it reported `failed 1800.0 s` rather than a number. Re-run with the timeout raised; coverage is stated exactly rather than claimed. §5 |

An unplanned finding, from the measurement in §3 rather than from any of the
questions: **`aipcb check` was not a function of the source.** Checking one unchanged
design three times into one `--out` directory took it from 1108 mm of copper and
90/90 routed to 2462 mm and 59/90, inventing a clearance error on the way. Found,
explained and fixed. §1.4

## Acceptance, clause by clause

| Clause | What happened |
|---|---|
| *"The check-visibility finding: explained, fixed if a gap existed, with the deliberate-crossing test in the suite"* | **Explained, and the gap was not the one the question assumed.** `check` reports a deliberate crossing as an error and always could; what it cannot see is any rule KiCad holds at `ignore`, which `--severity-all` excludes. Four such rules enumerated and pinned. Six tests added, including the deliberate crossing. §1 |
| *"Skew budgets verified against the actual standards, corrected or confirmed, the four pairs' status resolved as spec-fix or scoped roadmap item"* | **Verified against PCIe CEM r3.0 §4.7.7 and Serial ATA r3.5 Tables 54/57. PCIe corrected to the standard's own 0.127 mm (from 0.125, geometry-neutral); SATA confirmed at 0.25 mm.** No spec fix was available — the four pairs are genuinely 1.5–2.8× over the requirement, and they are a scoped roadmap item with the numbers attached. §2 |
| *"RX: hypothesis tested and outcome recorded (closed or characterised)"* | **The pour-gap hypothesis is refuted by measurement (0.1505 mm built against 0.150 modelled) and the residual is characterised, not closed.** The two links that miss the band are exactly the two whose ends are on different layers, and the estimator assumes a uniform line. The output now says so. §3 |
| *"REFCLK: converged with a meaningful number, or blocked-with-diagnosis at the stated iteration budget"* | **Blocked-with-diagnosis, at five of a budget of eight stated before the first run.** The divergence signature is a flat plateau, not a slow decay, which refutes M13's own recorded hypothesis. Three of four suspects refuted by measurement; the fourth located to within 4–5 dB. §4 |
| *"The M13 impedance and fitted-skew tables updated to full 11-link coverage (with whatever numbers are honest)"* | **Not met: 4 of 11 simulated, 1 of those 4 usable.** Two measured reasons rather than a scheduling one. First, a SATA link exceeds `aipcb simulate`'s own 1800 s default timeout, so M13's batch reported `failed 1800.0 s` rather than results. Second — and this is why the remaining seven were not simply queued — the one that did run came back `usable: false` at `\|Sdd21\| = 1.33`, making it **three non-physical extractions out of four links** on this geometry. The tables carry the coverage they have and say so in the same sentence. §5 |
| *"Suite green, mypy strict clean, byte-stable, committed and pushed"* | **Met.** §6. `.kicad_pcb` and `.kicad_sch` byte-identical on all eleven; `.kicad_pro` moved on all eleven, by the four pinned severities and nothing else. |
| Guardrail: *"no stretcher, router, or meander work"* | **Honoured.** No routing code was touched and no copper moved. The one behavioural fix outside measurement is `check` building fresh, which the guardrail's "check-integrity fixes" clause covers and which §1.4 justifies. |

---

## 1. What `check` can and cannot see

### 1.1 The crossing tracks: the pipeline was not the problem

M13a's fix was confirmed by KiCad reporting 2 `tracks_crossing` before and 0 after,
and the obvious next question was why a board the chain had checked repeatedly had
been carrying two shorts. It had not been.

`PRSNT` is not in `examples/pcie-sata`'s netlist. The strap exists only in the
reproduction M11 built by hand and M13a turned into a test, so no board `check` ever
ran on had `PRSNT` copper on it, and none of them had a crossing. M13's own report
says as much in passing — *"all eleven examples come back with zero crossings,
before and after the fix — the defect was latent"* — and the latency is the whole
answer.

Measured rather than argued. A worktree at `61e9129`, the commit before M13a, with
the strap added to the source and the *real* `aipcb check` run over it:

```
aipcb check, examples/pcie-sata + the A1-B17 strap, on the pre-M13a tree
  error    kicad-tracks-crossing            x2
  ...
  errors: 2      drc ran: True   counts: {'error': 2, 'warning': 1}
  raw kicad violations: {'tracks_crossing': 2, 'lib_footprint_mismatch': 1}
```

Two errors, correct category, correct severity, mapped back to the source like
everything else. **There was no gap here**, and `tests/test_check_loop.py::
TestNothingIsSilentlyFiltered::test_two_crossing_tracks_are_reported_as_an_error`
is what stops that answer from rotting: it lays two tracks of different nets across
each other on `routing-demo` and asserts an error comes back out of the real
`run_drc` with a hint attached.

### 1.2 The filter that is real, and is one level down

Asking the question properly turned up a different answer to it.

`kicad-cli pcb drc --severity-all` does not mean *all severities*. The report it
writes says what it included:

```
included_severities: ['error', 'warning', 'exclusion']
```

`ignore` is not in that list. A rule KiCad holds at `ignore` is dropped **inside
KiCad**, before any JSON reaches this project, and nothing in the report admits that
a category was suppressed — `included_severities` reads the same either way.

Proven by making a real violation disappear. Two crossing tracks on `routing-demo`,
then `tracks_crossing` pinned to `ignore` in the project file:

| | reported |
|---|---|
| as generated | `kicad-shorting-items` ×1, `kicad-solder-mask-bridge` ×3, **`kicad-tracks-crossing` ×1**, 5 errors |
| `tracks_crossing: ignore` | `kicad-shorting-items` ×1, `kicad-solder-mask-bridge` ×3, — , 4 errors |

Same `included_severities` both times. One error fewer, and no explanation anywhere.

**So which rules is KiCad 9.0.8 holding at `ignore`?** Nothing in `kicad-cli` will
say, and `pcbnew`'s Python bindings do not expose the severity map (checked). Two
independent readings instead:

* KiCad ships 37 project templates and demos that carry a full `rule_severities`
  map, giving a catalogue of **60 DRC rule names** and what KiCad writes for each.
  Four come out `ignore`: `footprint_filters_mismatch` (37 of 37),
  `missing_courtyard` (29), `npth_inside_courtyard` (26), `pth_inside_courtyard`
  (25).
* Then measured directly, by building a board that violates the rule and running
  DRC with and without the pin:

| rule | violations built | reported by default | reported when pinned |
|---|---|---|---|
| `missing_courtyard` | 6 footprints stripped of their courtyard | **0** | 6 |
| `pth_inside_courtyard` | 14 through-holes inside a courtyard | **0** | 14 |

`missing_courtyard` is the one that matters. `courtyards_overlap` is how a placement
is checked for legality, and a footprint with no courtyard opts out of it silently —
so the rule that would have told you the check is not running is itself not running.

**The fix.** Every generated `.kicad_pro` now pins
`aipcb.compile.project.DRC_SEVERITIES`: those four rules at `warning`, unconditional,
whether or not the design needs any other rule changed. It is `warning` and not
`error` because all four are advisory about how a board was drawn.

**What it changed on the corpus: one finding, on the flagship board.** All eleven
examples were re-run with the four rules pinned:

| example | newly visible |
|---|---|
| ten of the eleven | nothing |
| `pcie-sata` | `footprint_filters_mismatch` ×1, warning, on `U1` |

And it is a true positive. `U1`'s *symbol* is a connector stand-in — KiCad ships none
for a PCIe-to-SATA controller, which the example's own header says — so its footprint
filters read `Connector*:*_1x??_*` while the part declares
`Package_DFN_QFN:QFN-48-1EP_7x7mm_P0.5mm_EP5.15x5.15mm`. KiCad has been able to say
"that symbol was not meant for that footprint" the whole time and was holding the
rule at `ignore`. It is now in `KNOWN_ISSUES` with that explanation rather than
suppressed.

The first pass at this measurement said "nothing, anywhere", and it was wrong: it
counted `payload["violations"]` and a schematic-parity finding arrives in
`payload["schematic_parity"]`. The suite caught it — `test_examples_check_clean`
failed on `pcie-sata` — which is the second time in two milestones that the tests
have caught the report being wrong about its own measurement.

The rule names are written down in the test suite as `KICAD_DRC_RULES` with the
version and the date attached, per ADR 0009's discipline, because they are KiCad's
and they will move.

### 1.3 Two other things the enumeration turned up

**A hint that had never once fired.** `_HINTS` was keyed on `courtyard_overlap`.
KiCad's rule is `courtyards_overlap`, plural. From M4 to M13.5 the hint for the most
common placement violation was attached to a rule name that does not exist. Fixed,
and `test_every_hint_names_a_rule_kicad_actually_has` now checks every key against
the catalogue.

**Copper outside the board outline is invisible to DRC.** Measured on 9.0.8: the
same two crossing tracks, moved outside `Edge.Cuts`, produce no `tracks_crossing`,
no `clearance` and no `copper_edge_clearance` — only `track_dangling`, which is
about their ends rather than about where they are. Nothing in aipcb puts copper
there and this is not a bug report; it is a test
(`test_copper_outside_the_outline_is_invisible_to_drc`) so that a change which
starts to would not be verified by a DRC that cannot see it.

### 1.4 The one that was actually broken: `check` was not a function of the source

The step-3 measurement below wanted the pour gap along each pair, so it ran `check`
into a directory and read the filled board. The first attempt crashed after the
board was written; the second ran into the same directory and produced a board with
three long straight tracks on it that no router had drawn.

That is not a measurement artefact. Checking the same unchanged design repeatedly
into one `--out` directory:

| run | copper | routed | DRC errors |
|---|---|---|---|
| 1 | 1108.4 mm | 90 / 90 | 0 |
| 2 | **1852.7 mm** | **68 / 90** | **1** (`clearance`) |
| 3 | **2462.3 mm** | **59 / 90** | **1** |

`check` routes the board it builds and writes the copper into it. The next build
read that copper back, and `compile/preserve.py` says in its own header that
`segment`, `via` and `zone` items are *"never generated, and so always belong to a
human"* — so it kept them, and the router then routed the design again on top of
them.

**That sentence was true when it was written and stopped being true twice**: at M7,
when routing started writing segments and vias, and at M10, when the source started
declaring zones. Nothing noticed, because nothing had ever checked the same design
twice into one place. It is the same failure mode this repository's `CLAUDE.md`
warns about for external tools, arriving from inside.

The fix is one argument: `check` builds with `fresh=True`. A check is a question
about the source, so it has to be a function of the source alone. Preserving a
human's edits across a rebuild is still `aipcb build`'s job and is untouched.
`TestCheckIsAFunctionOfTheSource` asserts the board, the routing summary and the DRC
counts are identical across two consecutive checks; before the fix it fails on the
first assertion.

---

## 2. The skew budgets, against the standards themselves

M13 turned two over-budget pairs into four and the milestone asked whether the
budgets were the problem. They are not, and the answer took no simulation at all.

### PCIe

**PCI Express Card Electromechanical Specification, Revision 3.0 (2013-07-21),
§4.7.7, "Skew within the Differential Pair":**

> The differential pair shall be routed such that the skew within differential
> pairs is less than 0.127 mm (5 mils) for the add-in card and 0.254 mm (10 mils)
> for the system board.

`examples/pcie-sata` is an add-in card — it has PCIe edge fingers and lives in a
slot — so **0.127 mm** is the number. The class carried 0.125 mm, which is the
standard's figure rounded down with nothing recording what it was rounded from. The
source now says 0.127 with §4.7.7 quoted beside it. Checked before making the
change: routing is byte-identical at both values (same SHA-256 over the whole
board), so this moved no copper and did not invalidate the simulation batch that was
running at the time.

**So the four pairs are genuinely over the standard**, by 1.5× to 2.8×:

| pair | as built | PCIe CEM add-in-card limit | over by |
|---|---|---|---|
| `PCIE_TXN+PCIE_TXP` | 0.191 mm | 0.127 mm | 1.50× |
| `PCIE_TXN_C+PCIE_TXP_C` | 0.247 mm | 0.127 mm | 1.95× |
| `PCIE_RXN+PCIE_RXP` | 0.219 mm | 0.127 mm | 1.72× |
| `REFCLKN+REFCLKP` | 0.359 mm | (see below) | — |

**This is not a specification fix, and one argument has to be withdrawn.** M11 and
M12 both reached for "1.2–2.2 ps against a 125 ps unit interval is absorbable", and
M13 repeated it. §4.7.7's stated rationale is common-mode conversion and therefore
**EMI**, not timing: 0.127 mm is about 0.8 ps in this laminate, so the standard is
already asking for something far tighter than a timing argument would produce, and
answering it with a timing argument answers a question it is not asking. The four
pairs need geometric work — placement, so the two halves break out symmetrically —
and that is on the roadmap with these measurements attached, not done here.

**REFCLK is not covered by §4.7.7 at all**, and the check turned up a second thing.
§4.7's budgets are the *Link's* — the data lanes. The reference clock is routed
"according to best-known clock routing rules", and §2.1.1 says its timings assume
**nominal 100 Ω** differential. `examples/pcie-sata` carries REFCLK in the `pcie_rx`
class at **85 Ω**. That is a real mismatch between the board and the standard, it is
not a skew question, and fixing it means giving REFCLK its own net class — a
geometry change M13.5 had no mandate to make. On the roadmap, and §4 below reads
REFCLK's simulated impedance in that light.

### SATA

**Serial ATA Revision 3.5 Gold (2020-07-01) gives no intra-pair skew figure for a
PCB trace**, which is the first useful thing to know: the number usually quoted as
"the SATA skew spec" is one of three other things.

| what | where | limit |
|---|---|---|
| `tskewTx` — the transmitter's own differential skew, at the mated connector | Table 54, Gen1i/Gen2i/Gen3i | **20 ps max** |
| `tskewRx` — what a receiver must tolerate | Table 57, Gen3i | 30 ps |
| mated cable assembly intra-pair skew | §6.12 | ≤ 10 ps |

A board trace between silicon and connector spends out of the first. The class
budget of 0.25 mm is about **1.6 ps** in this laminate — under a twelfth of the
transmitter's entire budget. So the budget is conservative by design rather than
wrong, it is **confirmed rather than loosened**, and the eight SATA pairs meet it
with room to spare at 0.000–0.041 mm as built. The class comment now carries the
table numbers instead of the rule of thumb it used to cite.

### One more thing the standard says, which changes how §3 reads

**PCIe CEM r3.0 §4.7.8:** an 8.0 GT/s data pair's PCB differential impedance "must
be in the range of **70 Ω to 100 Ω**". The project's own ±10 % band on an 85 Ω
target is 76.5–93.5 Ω — *tighter than the standard*. `PCIE_RX` at 72.8 Ω misses the
project's band and sits inside the standard's. That does not make the residual
uninteresting, and §3 does not treat it as closed; it does mean the board this
milestone is arguing about would pass the requirement it was designed against.

---

## 3. `PCIE_RX` at −14.4 %: one hypothesis, refuted, and what the residual actually is

The milestone asked for **one** hypothesis, tested with the minimum simulation.
Two were available for free and both were answered without starting a solver.

### The pour gap is not the cause

The coplanar model is handed `clearance_mm` — 0.15 mm — as the gap to the pour. What
the built board has, measured off the filled copper by sampling each pair's
centre-line every 0.1 mm and taking edge-to-edge distance to the `GND` pour on the
same layer:

| pair | layer | as-built width | pour gap: min | median |
|---|---|---|---|---|
| `PCIE_TXP/N` | F.Cu | 0.1846 mm | 0.1505 mm | 0.1505 mm |
| `PCIE_RXP/N` | B.Cu | 0.1846 mm | 0.1505 mm | 0.1505 mm |
| `PCIE_RXP/N` | F.Cu | 0.1846 mm | 0.1505 mm | 0.1518–0.1558 mm |
| `REFCLKP/N` | B.Cu | 0.1846 mm | 0.1505 mm | 0.1505 mm |
| all eight `SATA*` | F.Cu | 0.1379 mm | 0.1505 mm | 0.1505 mm |

**0.1505 mm against a modelled 0.150 mm, on every pair and every layer** — 0.3 %
out, in the direction that would make the impedance *higher* rather than lower. The
widths are the derived ones to four decimal places. The model's inputs are the
board's geometry, and the hypothesis is refuted.

A second free check went with it: `pcie_tx` sits on F.Cu over In1 and `pcie_rx` on
B.Cu over In2, and if those two dielectrics differed the two classes could not
correctly derive the same width. The stackup is symmetric — `prepreg_top` and
`prepreg_bottom` are both 0.2104 mm of 7628 — so that is not it either.

### What the two failing links do share

Read off the solver inputs rather than argued:

| link | port layers | reference planes | result |
|---|---|---|---|
| `PCIE_TXN+PCIE_TXP` | 0, 0, 0, 0 | 1, 1, 1, 1 | 80.0 Ω, **−5.8 %** |
| `PCIE_RXN+PCIE_RXP` | **3, 0, 3, 0** | **2, 1, 2, 1** | 72.8 Ω, −14.4 % |
| `REFCLKN+REFCLKP` | **0, 3, 0, 3** | **1, 2, 1, 2** | 49.8 Ω, −41.4 % (unconverged) |
| `SATA*` × 8 | 0, 0, 0, 0 | 1, 1, 1, 1 | §5 |

**The two links whose two ends are on different layers are exactly the two that miss
the band, and the ones that stay on one layer do not.** Two out of two, and nought
out of one among the PCIe links that keep both ends on F.Cu.

That matters because of what the estimator is.
`si/results.py::analyse` reads a **median input impedance** over a band trimmed to a
whole number of standing-wave periods. That recovers the characteristic impedance of
a *uniform* line from the ripple its own length puts on the input impedance. A link
that changes layer half way along is not a uniform line: it is roughly 2.6 mm on
F.Cu over In1, a via barrel, and 16.8 mm on B.Cu over In2 — a cascade of two
sections referenced to two different planes. The median of what port 1 sees through
that is not either section's Z₀, and calling it one is a category error rather than
an inaccuracy.

The slicer already knew — its own note on both slices says *"the pair changes layer,
so its two ends are referenced to different planes; the impedance reported is the
whole link, not either half"* — but the number went out to the report and the ±10 %
verdict anyway, and M13's table presented it as a trace impedance beside `PCIE_TX`'s.

### The measurement that would have settled it, and why it cannot

The S-parameters are already on disk, so a TDR — the step response of Γ_dd,
inverse-transformed — costs nothing and separates a cascade into its sections. It
was run. It cannot answer this question:

* the sweep stops at 8 GHz, so the step's rise time is ~63 ps, which is **4.5–5 mm**
  of spatial resolution in this laminate;
* the F.Cu section is **2.6 mm** long.

The section under suspicion is half the size of the smallest thing the data can
resolve. What the profiles do show is that neither link has any sustained region at
72.8 Ω — both sit near 87–88 Ω at the port and swing above it — which is consistent
with two ~85 Ω sections and a discontinuity, and is not evidence enough to say so.

### Outcome: characterised, open, and no longer mislabelled

The residual is **not closed**. What changed is that it is no longer reported as a
trace impedance:

* `si/slice.py` gains `Slice.spans_layers` and `Slice.spans_planes`, both in
  `slice.json`;
* `Metrics.spans_layers` carries it into `result.json`;
* and a link whose ends are on different layers now emits, in its own output, *"the
  two ends of this pair are on different layers, so the span measured here contains
  a via transition and a change of reference plane; the impedance below is the whole
  link's and is not the characteristic impedance of either section"*.

The number is still published, because it is a real measurement of the whole link.
What stops is offering it as something to compare against a fabricator's coupon.

Verified end to end by re-running `aipcb simulate` over M13's own three PCIe
directories. Every slice digest still matches, so all three are cache hits and the
whole thing costs no solver time at all:

```
PCIE_RXN+PCIE_RXP   spans_layers=True    budget=0.127   Z=72.78
    -> the two ends of this pair are on different layers, so the span measured
       here contains a via transition and a change of reference plane; ...
PCIE_TXN+PCIE_TXP   spans_layers=False   budget=0.127   Z=80.05
REFCLKN+REFCLKP     spans_layers=True    budget=0.127   Z=49.78
    -> ...
```

`result.json` is now rewritten on a cache hit as well as on a fresh run. The metrics
are recomputed every time — they are derived from the S-parameters, not from the
run — so a stored copy that was written by older analysis code was quietly
disagreeing with what the tool would say today. Every cached result on this machine
was still claiming there was nothing unusual about a link that changes layer. The
`digest` and the `run` block are the run and do not move.

**What would actually close it** is a slicer that can cut one side of a transition
and port it on its own — which is the thing M13 said the slicer does not do, still
does not do, and is now on the roadmap with the reason written next to it. The
cheaper half-step, and the one worth doing first, is to widen the sweep: at 20 GHz
the TDR resolution would be under 2 mm and this would be a five-minute question.

---

## 4. `REFCLK`: blocked, with a diagnosis, and M13's hypothesis refuted

**The iteration budget was set at eight reduced-settings runs before any were
started**, per the milestone. Five were used. What they bought is a diagnosis rather
than a converged number, so REFCLK's simulation is recorded as
**blocked-with-diagnosis** and the −41.4 % in M13's table stays what it was: a number
read off a run with 6 % of its energy still in the box.

### What "does not converge" actually looks like, from data M13 already had

Nobody had plotted it. The solver logs on disk carry an energy sample every few
hundred timesteps, and the shape settles the question before any new run:

| | `PCIE_TXN+PCIE_TXP` (converges) | `REFCLKN+REFCLKP` (does not) |
|---|---|---|
| peak energy | 9.25e-16 at ts 11 661 | 1.45e-15 at ts 15 488 |
| then | −8.8, −24.3, −26.7, −36.2, −41.0, −47.6, −52.8, −58.6, **−64.3 dB** | −6.1, −8.8, −9.2, −9.0, −8.8, −9.2, −9.1, −9.4, −8.6, −10.2, −9.1, **−10.2 dB** |
| shape | monotonic exponential decay over ~40 000 steps | **falls 9 dB, then flat for 42 000 steps** |

REFCLK does not decay slowly. It decays for about 7 000 timesteps, loses roughly 90 %
of its peak energy — the part that leaves through the ports — and then **stops**. The
remaining tenth sits in the box, oscillating between −8.3 and −10.8 dB, for the
entire rest of the run.

**This refutes M13's stated hypothesis.** M13 wrote: *"the step limit, not the model.
It is testable — raise `max_steps` for that class and watch the energy floor."* It is
not the step limit. Forty thousand more steps of a flat line is a flat line, and the
evidence for that was already in the log file M13 wrote. Raising `max_steps` would
have cost about eight minutes a run and produced the same −10 dB.

What it is, is a **trapped mode**: about a tenth of the injected energy is in a
resonance with no path to a port and nothing to dissipate it. FDTD in a lossless
structure will hold that forever.

### The iterations, and the rule that made them cheap

Reduced-settings iteration was mandatory, and two of the three levers the milestone
named turned out not to exist:

* **A coarser mesh is not available.** `si/inputs.py::grid_optimal_um` is defined as
  *never coarser than the setting*, so raising `grid_optimal_um` in the source does
  nothing — the geometry's own demand wins. Setting it to 60 µm left the cell at
  30.7 µm and, because `max_steps` scales with the ratio, quietly multiplied the step
  limit by 1.95 instead. That is correct behaviour and it means the mesh cannot be
  used as a reduced setting from the design file.
* **A narrower band breaks the measurement rather than cheapening it.** Sweeping to
  4 GHz produced `"the swept band is shorter than one standing-wave period on this
  pair"` and a group delay of **−35 ps** over 19.7 mm of conductor — the tool's own
  "the ports are not measuring the trace" note, correctly fired.

What does work is the step limit, applied to an already-generated slice. Every run
below re-exports the same slice with one thing changed and `max_steps` cut, so the
mesh, the band, the ports and the stackup are byte-identical to M13's own run.

| # | what changed | steps | energy at ts ≈ 20 000 | verdict |
|---|---|---|---|---|
| i1 | `grid_optimal_um` 60, band 0.1–4 GHz | 15 635 | — | **the levers do not work**; band too narrow to measure |
| i2 | *nothing* — control at reduced steps | 20 000 | −6.96 dB | reproduces M13's trace **sample for sample** |
| i3 | all 17 foreign-net items deleted | 20 000 | −5.87 dB | no better than the control |
| i4 | the same, run long enough to see the plateau | 48 000 | **−10.11 dB at ts 47 916** | **plateaus exactly as the control does** (−10.22 dB at ts 64 372) |
| i5 | `In2.Cu` tied to `GND`, foreign copper kept | 48 000 | see below | the last suspect |

i2 is worth its two and a half minutes on its own: its energy trace is
value-for-value identical to the first 20 000 steps of M13's full run, which is what
makes the reduced runs admissible as evidence at all.

### What has been ruled out, and at what cost

**Foreign floating copper in the slice: not the trap.** REFCLK's slice carries the
whole transmit quartet — `PCIE_TXN`, `PCIE_TXP`, `PCIE_TXN_C`, `PCIE_TXP_C`, twelve
segments — with the AC-coupling capacitors *not* bridged, because the slicer bridges
only the pair under test. Each is an open-ended conductor over ground with no port
and no loss, which is a textbook half-wave resonator in the middle of the swept band,
and it was the obvious suspect. Deleting all seventeen foreign items changes the
energy trace by under 1 dB and does not change the plateau. Two runs, about five
minutes.

**Boundary proximity: not the trap, and free.** All three PCIe slices put their pair
exactly **1.592 mm** from the outline — it is the launch margin, uniform by
construction — so the link that converges and the link that does not are equally far
from the wall. No simulation needed.

**The step limit: refuted before spending anything**, from the trace above.

### What is left, and what M13.5 did with it

The structural difference between `REFCLKP/N` and `PCIE_RXP/N` — same class, same
width, same gap, same layers, one converges and one does not — is what remains:

| | `REFCLKN+REFCLKP` | `PCIE_RXN+PCIE_RXP` |
|---|---|---|
| slice | 5.260 × 25.297 mm | 4.435 × 25.297 mm |
| `GND` vias inside the slice | **5** | **7** |
| planes | `GND` on F.Cu, B.Cu, In1.Cu · `P3V3` on In2.Cu | the same |
| final energy | **−10.2 dB** | −49.9 / −61.3 dB |

`In2.Cu` carries `P3V3` and, inside the slice, is connected to nothing at all: a
floating plate between two grounded ones, with the pair's own via barrel passing
through its antipad. That is the classic way to excite a parallel-plate mode, and
the only thing that damps it is stitching — of which REFCLK's window has five vias
and RX's has seven.

### i5: the floating plane holds some of it, and not all of it

`In2.Cu`'s zone was renamed from `P3V3` to `GND` in the slice — one net, nothing else
touched, so the plate stops floating and joins the two that are already grounded.

| | control (i2/i4 and M13's run) | i5, `In2.Cu` tied to `GND` |
|---|---|---|
| ts 20 000 | −7.48 dB | −8.66 dB |
| ts 24 000 | −8.88 dB | **−14.11 dB** |
| ts 32 000 | −8.34 dB | −14.18 dB |
| ts 45 000 | −9.98 dB | −15.07 dB |
| final | **−10.2 dB** | **−14.1 / −15.6 dB** |

**It is worth about 4–5 dB, and it is still a plateau.** The floating plane holds a
share of the trapped energy — roughly two thirds of what was stuck comes out once it
is grounded — and something else holds the rest. Convergence needs about −40 dB;
this is −15.

So the honest position, at five of eight budgeted iterations:

> **`REFCLKN+REFCLKP` is blocked, with a diagnosis.** The −41.4 % in M13's table is
> read off a run with 6 % of its energy still in the box and remains unusable. The
> failure is a trapped resonance, not an insufficient step limit — which is the
> opposite of what M13 recorded. Of the four suspects the milestone named, three are
> refuted by measurement (step limit, foreign copper in the slice, boundary
> proximity) and the fourth — a resonant structure inside the slice — is confirmed as
> *present* and only partly located: the un-grounded `In2.Cu` plane accounts for
> 4–5 dB of it.

Stopping here rather than spending the remaining three iterations is deliberate. The
next experiment is a board question rather than a solver one — REFCLK's slice has
**five** `GND` stitching vias where `PCIE_RXP/N`'s has **seven**, for the same
transition depth through the same stack — and answering it properly means changing
copper, which this milestone was told not to do. It is on the roadmap with this
measurement attached.

### One observation that is not evidence, and is worth writing down

M12 simulated the same pair at a 50 µm mesh on a wider trace and its energy reached
**−41.2 dB**. M13's run reaches −10.2. Three things changed between them — the mesh
(50 → 30.7 µm), the trace (0.289 → 0.185 mm) and the routing (44 → 42 vias) — so
this attributes to nothing. It is recorded because it means the trapped mode is not
a permanent feature of this geometry: there is a configuration of this same pair, on
this same board, that does converge, and M12 has it.

---

## 5. The eight SATA links, and the cost that made them impossible

M13 deferred the eight SATA links and left a batch running for them. **That batch
could not have succeeded**, and finding out why is the useful part of this section.

### The batch M13 left running failed, twice, at exactly 1800.0 s

It was still going when this session opened, an hour and fifty minutes in, with
nothing to show:

```
simulating pcie-sata into .../final
  SATA0_RXN+SATA0_RXP      failed  1800.0 s
  SATA0_TXN+SATA0_TXP      failed  1800.0 s
```

1800 s is `si/runner.py::DEFAULT_TIMEOUT_S`. Every SATA link was going to hit it.

**Why the estimate was wrong.** M13 measured the slice — 3.63 M cells at 22.9 µm,
`max_steps` 87 336 — and projected 9–13 minutes a link from the solver's throughput.
Two things the projection missed:

* **a pair is two solver runs, not one.** gerber2ems excites each half of the pair
  in turn, so the 87 336 steps are paid twice;
* **throughput is not 800–1200 MC/s on a slice this size.** Measured here on a
  SATA slice: **335 MC/s with the machine to itself**, 237 MC/s while anything else
  was running. In the units that matter it is **79 timesteps a second**.

So a SATA pair is 174 672 timesteps at 79 steps a second — **about 37 minutes on an
idle sixteen-core machine**, against a per-pair budget of 30. The projection was out
by a factor of three to four, and the failure mode was not "slow" but "reported
nothing at all": a timeout produces no `result.json`, so the next run re-slices and
starts again from zero.

The arithmetic that matters for anyone planning the next batch: **eight SATA links
is about five hours**, and it is five hours whether or not the timeout is set high
enough to let them finish.

Nothing warns about this before a batch starts, and everything needed to warn is
known at slice time: the cell count, the step limit and the machine's own measured
throughput are all in hand before the container is launched. On the roadmap.

### Where the eleven links stand

The batch was relaunched with `--timeout 7200` on the tree as committed. The geometry
is byte-identical to M13's — the only source change is §2's skew budget, and that was
checked to move no copper *before* it was made — so every slice digest still matches
and the three PCIe links come back as cache hits at no solver cost at all.

**One SATA link was re-simulated before the machine was needed for the suite, and
it came back unusable.** That is the more useful half of this section:

```
SATA0_RXN+SATA0_RXP   3 216 s   Zdiff 165.15 ohm against a 100 ohm target (+65.1 %)
                                energy -33.9 dB, |Sdd21| = 1.33, usable: false
```

(3 216 s and not the 37 minutes projected above because the test suite was running
beside it for most of that; the 79 timesteps a second the projection uses was
measured with the machine to itself. Either way it is past 1800 s.)

`|Sdd21|` above unity is more energy out than went in, so the extraction is not
physical and the tool refuses to publish an impedance verdict for it — correctly.
Two things about it are worth stating plainly.

**It is off in the opposite direction from every M12 number.** M12's SATA links read
62.5–91.9 Ω against 100 — *below* target, which is what the bare-microstrip model
error predicts. This reads 165 Ω. That is not a model error in either direction; it
is an extraction that has stopped meaning anything.

**And it is now three links out of four.** On the M13b geometry, of everything
simulated to date:

| link | `usable` | why not |
|---|---|---|
| `PCIE_RXN+PCIE_RXP` | **true** | — |
| `PCIE_TXN+PCIE_TXP` | false | `\|Sdd21\|` 1.23 |
| `REFCLKN+REFCLKP` | published as `warn` | `\|Sdd21\|` 1.13, energy −12 dB |
| `SATA0_RXN+SATA0_RXP` | false | `\|Sdd21\|` 1.33, energy −34 dB |

M13 recorded the transmit link's `|Sdd21| > 1` as a single odd result with the
AC-coupling bridges as its suspect. **It is not a single odd result.** Three of the
four links measured on this geometry fail the same physical sanity check, and the
one that passes is the one whose energy decayed furthest (−61 dB). The common thread
is incomplete decay, not coupling capacitors — which puts it in the same family as
§4 rather than in the family M13 filed it under, and makes "simulate the other seven
SATA links" the wrong next move. **The next move is to find out why energy stopped
leaving these slices after M13b changed the mesh and the trace width**, because
until that is answered a bigger batch buys more unusable numbers at 37 minutes each.

This is on the roadmap, and it is the single most consequential thing M13.5 found in
§§4–5.

**Coverage is not eleven, and saying otherwise would be the reframing this project
exists not to do.** What is measured, and what is not:

| Link | Target | M12 | M13 | M13.5 | spans layers? | inside ±10 %? |
|---|---|---|---|---|---|---|
| `PCIE_TXN+PCIE_TXP` | 85 Ω | 66.6 Ω (−21.6 %) | **80.0 Ω (−5.8 %)** | unchanged, cached | no | **yes**, but `usable: false` (\|Sdd21\| 1.23) |
| `PCIE_RXN+PCIE_RXP` | 85 Ω | 61.5 Ω (−27.6 %) | **72.8 Ω (−14.4 %)** | unchanged, cached; now labelled | **yes** | no — and §3 says what the number is |
| `REFCLKN+REFCLKP` | 85 Ω | 50.9 Ω (−40.1 %) | 49.8 Ω (−41.4 %) | **blocked-with-diagnosis**, §4 | **yes** | no, and the number is not a measurement |
| `SATA0_RXN+SATA0_RXP` | 100 Ω | 91.9 Ω (−8.1 %) | not run | **165.2 Ω, `usable: false`** | no | **no verdict** — the extraction is not physical |
| `SATA*` × 7 | 100 Ω | 62.5–91.9 Ω | not run | **not run** | no | — |

**So the acceptance clause "all 11 links" is not met, at 4 of 11 simulated and 1 of
those 4 usable.** The seven that did not run are about **four and a half hours** of
solver time at the measured rate, and on the evidence of the one that did, that time
would mostly buy `usable: false`.

### The fitted-vs-geometric table, at the coverage it actually has

M13c's acceptance asked for this on all eleven links and got three. M13.5 does not
change that number, so the table below is M13's three with the corrected budget —
and the honest headline is that **the fit still has three points and one of them is
unconverged, so its false-positive rate is still nought out of three, which is still
not a rate.**

| Link | budget | geometric | slice's own | fitted Δτ | fitted as length | floor | fit improvement | verdict |
|---|---|---|---|---|---|---|---|---|
| `PCIE_TXN+PCIE_TXP` | 0.127 mm | 0.247 mm | **0.439 mm** | 0.00 ps | 0.000 mm | −17.7 dB | 0.0 dB | `under-floor` |
| `PCIE_RXN+PCIE_RXP` | 0.127 mm | 0.219 mm | 0.219 mm | 0.00 ps | 0.000 mm | −24.6 dB | 0.0 dB | `under-floor` |
| `REFCLKN+REFCLKP` | 0.127 mm | 0.359 mm | 0.359 mm | **1.33 ps** | **0.198 mm** | −34.3 dB | 0.82 dB | `under-floor` |
| the eight `SATA*` | 0.25 mm | 0.000–0.041 mm | — | — | — | — | — | not simulated |

Two things M13.5 adds to it rather than to the numbers.

**The budget column is now the standard's**, not a rounded version of it (§2), and it
moves no verdict: 0.219 mm was over 0.125 and is over 0.127.

**The geometric column is the one worth trusting on the four PCIe pairs**, and §2 is
why. The fit says `under-floor` on all three, which is the correct refusal for data
whose floor sits at −17 to −34 dB; the router's own measurement says 0.191–0.359 mm
against a standard that asks for 0.127. The verification layer that can currently
answer the question is the geometric one, and the frequency-domain one is not yet
able to contradict it — which is a thinner claim than "they agree", and is what the
evidence supports.

---

## 6. What changed, what it cost, and the gates

### Output

| | |
|---|---|
| `.kicad_pcb` and `.kicad_sch` | **byte-identical on all eleven examples** |
| `.kicad_pro` | **moved on all eleven** — the four pinned `rule_severities`, and nothing else. Goldens regenerated; the diff is six added lines per project |
| routing | **unchanged on all eleven** — `examples/pcie-sata` stays at 90/90 connections, 12/12 coupled, 42 vias, 1108.1 mm, 0 DRC errors, 0 cross-net overlaps |
| `examples/pcie-sata/design.yaml` | `max_skew_mm` 0.125 → 0.127 on the two PCIe classes, with PCIe CEM r3.0 §4.7.7 quoted; the SATA class's skew comment replaced with SATA 3.5's own table numbers. **No copper moved** — verified by SHA-256 over the routed board at both values before the edit was made |

`check` on `pcie-sata` now reports **7 warnings and 0 errors** where M13 reported 6
and 0, measured:

| code | count |
|---|---|
| `hs-skew` | 4 |
| `diff-pair-wall-hugging` | 1 |
| `kicad-lib-footprint-mismatch` | 1 |
| **`kicad-footprint-filters-mismatch`** | **1 — new, and §1.2 is why** |

That one warning is the only behavioural change to `check`'s output anywhere in the
corpus. Four rules were promoted out of `ignore` across eleven examples and exactly
one of them had anything to say.

### Source

| file | what |
|---|---|
| `compile/project.py` | `DRC_SEVERITIES`, pinned into every generated project |
| `checks/kicad_reports.py` | `courtyards_overlap` spelling fixed; hints for `tracks_crossing`, `shorting_items` and the three courtyard rules |
| `checks/loop.py` | `check` builds `fresh=True` |
| `si/slice.py` | `Slice.spans_layers`, `Slice.spans_planes`, both into `slice.json` |
| `si/results.py`, `si/run.py` | `Metrics.spans_layers`, and the note a layer-spanning link now carries |

### Gates

| check | result |
|---|---|
| `pytest -q` | **exit 0 — 1 181 passed, 1 skipped, 30 m 31 s** (1 182 collected, up from 1 174) |
| `ruff check .` | **All checks passed** |
| `mypy --strict src/aipcb` | **Success: no issues found in 86 source files** |

The one skip is `test_sexpr_corpus`'s, as it has been since M1. The 30 m 31 s is not
comparable to M13's 24 m 18 s: a SATA solver was running beside it for the first
forty per cent of the run, which is stated here rather than quietly reported as a
regression.

The suite grew by **eight**, and every one of them exists because something in this
milestone was found by measuring rather than by testing:

| test | what it holds |
|---|---|
| `test_two_crossing_tracks_are_reported_as_an_error` | the milestone's own: two nets' copper in one place comes back as an error, with a hint |
| `test_copper_outside_the_outline_is_invisible_to_drc` | the limit of that claim, pinned so a change that starts putting copper there is noticed |
| `test_a_footprint_without_a_courtyard_is_reported` | the gap that was real, and is closed |
| `test_the_project_pins_the_rules_kicad_would_ignore` | the pins are unconditional, on a design that needs no other rule changed |
| `test_every_hint_names_a_rule_kicad_actually_has` | catches the `courtyards_overlap` class of mistake against KiCad 9.0.8's own 60-rule catalogue |
| `test_checking_twice_changes_nothing` | `check` is a function of the source; fails on the first assertion before §1.4's fix |
| `test_which_pairs_span_layers_is_a_property_and_not_prose` | which links span layers is readable, not inferred from a sentence |
| `test_a_layer_spanning_link_says_its_number_is_not_a_trace_impedance` | the caveat is attached, and the number itself is untouched by it |

### Simulation time spent, per step, against M12's baseline

M12's eleven links cost **7 837 s of solver time — 2 h 11 min**. M13.5's spend, by
the milestone's own work order:

| step | what it needed | solver time |
|---|---|---|
| 1 — check visibility | building boards and running `kicad-cli` | **0 s** |
| 2 — skew budgets | reading two published standards | **0 s** |
| 3 — the `PCIE_RX` residual | measuring the built board, and a TDR over S-parameters already on disk | **0 s** |
| 4 — `REFCLK` convergence | five reduced-settings runs: 319 s, 150 s, 137 s, 1 178 s, 957 s | **2 741 s — 46 min** |
| 5 — the SATA links | one link re-simulated; three cached PCIe links re-analysed at no cost | **3 216 s — 54 min** |

**Three of the five steps cost nothing**, which was the point of the ordering the
milestone imposed: the pour-gap hypothesis, the boundary-proximity suspect and M13's
own step-limit hypothesis were all settled by measuring something that already
existed. The one step that cost is the one that had to.

The reduced-settings rule is why step 4 is 46 minutes and not several hours. M13's
one full REFCLK run is 474 s; the whole diagnostic campaign is 2 741 s, and two of
its five runs — the two that refuted M13's own hypothesis and the foreign-copper
one — cost **150 s and 137 s** between them, because they ran 20 000 steps on a
slice that had already been generated. Iterating at full cost would have been about
eight minutes a hypothesis at best and, for the two long runs, forty.

The i1 line is worth reading as a cost as well as a result: 319 s spent discovering
that two of the three reduced-settings levers the milestone named do not exist on
this tool. That is the cheapest way to find it out and it is written down in §4 so
nobody spends it again.

---

## 7. What M13.5 leaves open

* **`REFCLK`'s trapped mode is located to within 4–5 dB, and not fully.** The
  floating `In2.Cu` plane holds about two thirds of what is stuck — grounding it in
  the slice moves the plateau from −10 dB to −15 dB — and something else holds the
  rest. The next experiment is a board question rather than a solver one: REFCLK's
  slice carries **five** `GND` stitching vias around its transition where
  `PCIE_RXP/N`, which converges to −50 dB through the same stack, carries **seven**.
  Testing it means changing copper, which is why M13.5 stopped.
* **The impedance estimator assumes a uniform line and nothing enforced it.** M13.5
  made a layer-spanning link *say* its number is the whole link's. It did not make
  the tool able to measure either section, and it did not stop the ±10 % verdict
  being taken against a number the estimator does not apply to. Widening the sweep to
  20 GHz would let a TDR separate them from data the existing pipeline already
  produces; that is the cheap half and it was not done.
* **Energy is not leaving these slices, and it is not one link's problem.** Three
  of the four links measured on the M13b geometry report more energy out than went
  in. §4 shows one of them trapping a tenth of its energy in a resonance; §5 shows
  the pattern is general. Nothing in M13.5 explains why M13b's change of mesh and
  trace width should have done this, and it is the question that gates every
  remaining simulation on this board.
* **`aipcb simulate` has no cost model.** M13 projected 9–13 minutes a SATA link and
  the real figure exceeds the tool's own 1800 s default timeout. The slice knows its
  cell count and its step limit before the container starts, so it could say so.
* **The four over-budget PCIe pairs still need geometry.** M13.5 confirmed the budget
  against the standard rather than moving it, which converts an open question into a
  scoped piece of work and does not do the work.
* **`preserve.py`'s premise is fixed where it bit and not where it lives.** `check`
  no longer merges, so the corruption is gone; the module still says `segment`, `via`
  and `zone` are "never generated" and `aipcb build` still believes it. A build over
  a routed board will preserve aipcb's own copper as though a human drew it. Nothing
  in the corpus does that today, and it is the next place this premise will bite.
* **M12's "deliberately degraded case" is still not run.** Three milestones have now
  named it. It would settle the mode-conversion floor and the
  does-simulation-discriminate question at once, and it is still an hour nobody has
  spent.

---

# M13.6 — one hypothesis, one invariant: slice grounding and check idempotence

M13.5 left three findings pointing the same way: `REFCLK` trapping a tenth of its
energy in a resonance, three of four impedance extractions non-physical, and a
SATA batch that could not finish inside its own timeout. The milestone named one
suspect — **the slice generator drops the stitching vias, so every simulation runs
against a board that does not exist** — and asked for it to be tested against the
artifacts rather than against the code.

It was, and the answer is **half of each**. The mechanism is real — the slicer
does lose stitching vias, 22 of the 41 that lie inside the eleven slice windows,
and on four slices including `REFCLK` it loses every one — but it loses them to a
half-millimetre clip band rather than to anything that deletes them, and it says
nothing when it does. The premise is wrong: `In2.Cu` is a `P3V3` **supply** plane
by declaration, no stitching via ties it on the board either, and what actually
leaves it floating in the model is that the slice cuts away its supply, its pads
and its decoupling. Two defects, sitting on top of each other, and neither one is
the whole of what the brief described.

Fixing both closes `REFCLK`. Fixing either alone does not.

## What M13.6 found, in one table

| question | answer |
|---|---|
| Do the slices drop M10's stitching vias? | **Yes — 22 of 41, and all of them on four slices.** `REFCLK`'s slice has two stitching vias inside its window on the board and carries none. Not by deletion: `_assemble` keeps a via only if its centre is inside the rectangle *inset by 0.5 mm*, and unlike the launch corridor, which drops vias and reports how many, this band reports nothing. §2.1 |
| Is `In2.Cu` tied to ground on the real board? | **No, and it was never meant to be.** The design declares `In2.Cu` a `P3V3` *supply* plane, and the `stitching:` block ties `GND` between `F.Cu` and `B.Cu`. The brief's premise was wrong about this board, and no amount of stitching would have grounded that plane. §2.1 |
| Then what leaves it floating? | **The cut.** A supply plane is a reference because it is decoupled to ground, and the slice keeps neither the decoupling, nor the pads, nor the supply. On all eleven slices `In2.Cu` touches no via, no pad and no port — 79 to 367 mm² at no defined potential — while the `pcie_rx` class names it as its `reference:`. §2.2 |
| Does fixing them close `REFCLK`? | **Yes, and only both together.** Four runs at 32 000 steps, one change at a time: control plateaus at −7 to −10 dB, a boundary fence alone at −9.5 to −10.8, tying `In2.Cu` alone at −13.6 to −15.1 (which reproduces M13.5's i5 independently), and the two together decay −9.8 → −18.8 → −29.3 → **−39.9 dB and still falling**. §2.3 |
| Is `check` a function of its source? | **Yes, on the flagship board too**, and the sweep found no sibling. `check` ×3 on `pcie-sata` gives byte-identical boards; `build`, `export --build-dir`, `simulate --dry-run` and `sync-placement` all repeat exactly. §1 |

## Acceptance, clause by clause

| Clause | What happened |
|---|---|
| *"Idempotence test in the suite (check × 3 identical), sibling sweep done, reverification note written"* | **Met.** Three-run tests on `usb-port` and on `pcie-sata`; four siblings swept and **no other command found reading its own output**; `docs/reports/reverification-note.md` written, and it re-measures the flagship's published figures rather than asserting they were fine. A guard test fails if a twelfth command joins without declaring which side of the line it is on. §1 |
| *"The grounding hypothesis tested against artifacts with the outcome recorded — confirmed-and-fixed, or refuted-with-next-hypothesis-tested"* | **Confirmed in mechanism, refuted in premise, and both halves fixed.** 22 of 41 stitching vias were being lost to a silent clip band, all of them on four slices including `REFCLK`; and `In2.Cu` is a `P3V3` supply plane that no stitching via ties on the board either, left floating in every slice by the cut. §2 |
| *"Both probe links physical, or an honest stop with diagnosis"* | **Both physical.** `REFCLK` decays 63.7 dB where it plateaued at 10.2, and `SATA0_RX` goes from 165.15 Ω / `usable: false` to 108.26 Ω with every verdict passing. §3 |
| *"If batched: 11/11 links with physical extractions (`\|Sdd21\| ≤ 1` everywhere), tables updated, REFCLK convergence story closed"* | **Batched, and met at ten of eleven.** All eleven ran, both tables are at full coverage for the first time, and `REFCLK` is closed — energy −63.7 dB against −10.2, and the run ends on decay rather than on the step limit. `PCIE_TX` remains `usable: false` at 1.220, and §4.3 is what that turned out to mean. On the literal `≤ 1`: no run this pipeline produces meets it, including its known-good ones, and §3.3 says why. §4 |
| *"Timeout parameterized from measured runtimes"* | **Met.** `simulation.timeout_s`, defaulting to 7200 s, with the three measurements it is sized from written beside the constant and the design carrying it explicitly. `--timeout` now overrides the design rather than shadowing a constant. §6 |

## 1. The idempotence invariant, and the sweep for siblings

Free, and first, because it guards everything the rest of the milestone measures.

### 1.1 `check` three times, on the board the drift was found on

M13.5 fixed `check` and pinned it with a two-run test on `examples/usb-port`. Two
runs is not the invariant: the pre-fix drift *grew* on every repeat — 1108 mm,
1853 mm, 2462 mm — so a fix that stopped only the first repeat would have passed.
Three runs is what says the answer is stationary, and `pcie-sata` is where the
drift was measured.

```
aipcb check examples/pcie-sata/design.yaml --out <one directory>, three times
  run 1   sha256 0e8f21b1...   1108.092 mm   90/90   42 vias   0 errors, 7 warnings   44.82 s
  run 2   sha256 0e8f21b1...   1108.092 mm   90/90   42 vias   0 errors, 7 warnings   44.56 s
  run 3   sha256 0e8f21b1...   1108.092 mm   90/90   42 vias   0 errors, 7 warnings   44.47 s
```

Byte-identical boards, and the same numbers M13 and M13.5 both published — which
is the useful part: **the flagship board's recorded figures were not taken on an
accumulated board.** `docs/reports/reverification-note.md` says which measurements
could have been, what it took to trigger, and what supersedes what.

Two tests now hold this: `test_checking_three_times_changes_nothing` on `usb-port`
(the cheap one, in the default suite) and
`test_checking_the_flagship_board_three_times_changes_nothing` on `pcie-sata`
(behind `AIPCB_FULL_CORPUS=1`, because it is 45 s a run).

### 1.2 The sibling sweep: four other commands, and nothing else broken

The defect class is *a command reading its own previous output as input*, and the
way it hides is that nobody runs the same command twice into the same place. So
every command that writes into a directory a later run may read was run twice or
three times into one directory and its output compared.

| command | the way it could bite | measured |
|---|---|---|
| `build --out X` ×3 | since M10 the source declares zones, and `preserve.py` calls a zone a human's | **identical**. The UUID guard holds: an item whose UUID the fresh board already carries is ours, so declared zones do not double |
| `export --out Y --build-dir X` ×3 | `--build-dir` keeps the intermediate board a later run reads | **identical** board and, modulo KiCad's own creation-date stamp, identical fabrication files |
| `simulate --out X --dry-run` ×3 | `--out` keeps the slice, the solver inputs and the fabrication package, overwritten in place | **identical** slice bytes, identical `slice.json`, identical digest. This one matters more than it looks: the digest is the cache key, so a slice that moved between two runs of one design would hand back a cached number measured on different geometry |
| `sync-placement` ×2 | it reads a board and could rewrite the source | **writes nothing**, and says the same thing twice |

**No sibling was found.** That is the honest result and it is worth stating
plainly: the M13.5 defect was specific to `check` routing the board it built.

What is new is not a fix but a *guard*. `tests/test_idempotence.py` carries the
four tests above plus
`test_the_sweep_covers_every_command_that_writes_where_it_reads`, which reads
`aipcb --help` and fails if a command appears that is neither covered by a two-run
test nor declared read-only. A twelfth command cannot join quietly.

## 2. The grounding hypothesis: confirmed in mechanism, refuted in premise

### 2.1 What the slices actually contain

The eleven slices were regenerated (`aipcb simulate --dry-run`, no solver) and
measured rather than reasoned about. Each slice board was filled with KiCad's own
filler — the same `pcbnew` path `export` uses, so this is the copper the Gerbers
carry — and every via pad intersected against every zone's filled polygon.

`REFCLKN+REFCLKP`, the convergence case, as generated before M13.6:

| via | net | size | `F.Cu/GND` | `In1.Cu/GND` | `B.Cu/GND` | `In2.Cu/P3V3` |
|---|---|---|---|---|---|---|
| (136.775, 125.024) | GND | 0.4 | 100 % | 100 % | 100 % | **0 %** |
| (138.625, 124.976) | GND | 0.4 | 100 % | 100 % | 100 % | **0 %** |
| (139.300, 124.800) | GND | 0.4 | 100 % | 100 % | 100 % | **0 %** |
| (137.949, 144.124) | GND | 0.4 | 0 % | 55 % | 0 % | **0 %** |
| (138.629, 144.118) | GND | 0.4 | 0 % | 57 % | 0 % | **0 %** |
| (137.975, 124.993) | REFCLKN | 0.4 | — | — | — | **0 %** |
| (137.425, 125.007) | REFCLKP | 0.4 | — | — | — | **0 %** |

(Percentages are the overlap of the via's pad with that layer's fill.)

The **size** column is the whole finding, and it is the one M13.5 walked past. M10
drills its stitching at 0.6 mm; a fanout or transition via is 0.4 mm. Every ground
via in `REFCLK`'s slice is 0.4 mm. **The slice contains none of M10's stitching
vias at all** — the "five `GND` vias" M13.5 counted, and this milestone's brief
inherited, are transition vias that happen to be on the ground net.

Counted against the routed board, over all eleven slices:

| | inside a slice rectangle, on the board | reached the slice |
|---|---|---|
| **stitching vias** (0.6 mm) | 41 | **19** |
| other `GND` vias (0.4 mm) | 51 | 39 |
| all `GND` vias | 92 | 58 — of which 4 were removed by the launch corridor, **which says so**, and 30 went silently |

And per slice, for the stitching alone:

| slice | in the rectangle | in the slice | |
|---|---|---|---|
| `PCIE_RXN+PCIE_RXP` | 2 | **0** | converges; reads −14.4 % |
| `PCIE_TXN+PCIE_TXP` | 0 | 0 | none were there to lose |
| `REFCLKN+REFCLKP` | 2 | **0** | the non-convergent one |
| `SATA1_TXN+SATA1_TXP` | 4 | **0** | and no ground via of any size |
| `SATA2_RXN+SATA2_RXP` | 3 | **0** | |
| `SATA0_TXN+SATA0_TXP` | 8 | 3 | |
| `SATA3_RXN+SATA3_RXP` | 7 | 3 | |
| the remaining four | 15 | 13 | |

**So the hypothesis is confirmed in its mechanism.** The slice generator does drop
stitching vias, 22 of 41 of them, and on four slices — `REFCLK` among them — it
drops every one. The mechanism is not the one the brief guessed at, though: no
code deletes them. `_assemble` keeps a via when its centre lies inside the slice
rectangle *inset by 0.5 mm*, and a via in that band is simply never picked up. The
launch corridor drops vias too and reports how many; this band reports nothing, so
`REFCLK`'s slice said `0 via(s) were removed` while carrying none of the stitching
inside its own window.

**The premise underneath the hypothesis is wrong, and that matters more.** The
brief says "On the real board, In2 is not floating — M10's stitching vias tie it to
ground." The design says otherwise, in two places:

```yaml
planes:
  - layer: In2.Cu
    net: P3V3
    reason: Supply distribution, and the reference for the two pairs that land on
      the A-side fingers and therefore run on B.Cu.

stitching:
  - net: GND
    between: [F.Cu, B.Cu]
```

`In2.Cu` is a **supply** plane, deliberately, and the stitching grid ties `GND`.
No via on this board ties `In2.Cu` to ground and none was ever meant to. What ties
it on the assembled board is its own net — the supply, the controller's power
pins, and the decoupling across it — and the slice keeps none of the three. So the
dropped stitching is real and is *not* what leaves `In2.Cu` floating. Those are two
separate defects that happen to sit on top of each other.

### 2.2 The two defects, stated separately

**One: the clip band eats real vias, silently.** Thirty `GND` vias, 22 of them
stitching, across eleven slices. `SATA1_TX` is where it shows: its slice is
7.638 mm tall, M10's grid is anchored at multiples of 8 mm in board coordinates,
its window fell between two rows, and all four stitching vias inside its rectangle
were in the clip band. That model went to the solver with its `F.Cu` pour, its
`B.Cu` pour, its `In1.Cu` plane and its `In2.Cu` plane **mutually isolated** — four
sheets of copper where the board has one conductor, under a 100 Ω microstrip whose
reference was connected to nothing at all.

**Two: a plane the slice cannot connect is left floating.** On all eleven slices
`In2.Cu` carries `P3V3` and touches no via, no pad and no port — between 79 and
367 mm² of copper at no defined potential, between two grounded planes, with the
pair's own via barrel through its antipad. The `pcie_rx` net class, which carries
`PCIE_RX` *and* `REFCLK`, names that exact layer as its `reference:`. The slice was
simulating the two layer-spanning links over a return path that was not connected
to anything, and no amount of stitching would have fixed it, because stitching is
`GND` and this plane is not.

### 2.3 The next hypothesis, and the four runs that settled it

The evidence gives the hypothesis the milestone anticipated: **the slice boundary
cuts the plane's ground tie, and how many ties survive is decided by where a
7.6 mm window happens to land on an 8 mm grid.** Two candidate treatments, and the
discipline of M13.5's RX work says to test them one at a time, at reduced steps, on
a slice that has already been generated:

* **a boundary fence** — a ring of `GND` vias just inside the slice outline, which
  is the standard way to terminate a model cut out of a larger board, and which
  makes the number of ties a property of the geometry instead of a coincidence;
* **tying the declared planes** — `In2.Cu`'s zone renamed to `GND`, which is
  M13.5's i5 generalised from one experiment to a rule.

All four runs below are the same `REFCLK` slice with one thing changed and
`max_steps` cut from 65 146 to 32 000. Energies are the final sample of each of
the two excitations:

| # | change | at ts 20 000 | 24 000 | 28 000 | final | shape |
|---|---|---|---|---|---|---|
| e0 | *nothing* — control | −6.7 / −8.0 | −8.2 / −7.7 | −8.1 / −7.7 | **−7.5 / −9.9** | plateau |
| e1 | fence only | −6.4 / −7.5 | −10.0 / −6.3 | −10.8 / −8.9 | **−9.6 / −9.5** | plateau |
| e3 | `In2.Cu` tied only | −9.3 / −12.0 | −13.7 / −14.6 | −12.7 / −14.4 | **−13.6 / −15.1** | plateau |
| e2 | **fence and tie** | −9.8 / −9.6 | −18.8 / −20.3 | −29.3 / −29.5 | **−39.9 / −39.5** | **still falling** |

Four runs, 888 s of solver time — 15 minutes — and they say something neither
alone would have.

**e0 reproduces the control**, which is what makes the rest admissible: −6.7 to
−8.0 dB at ts 20 000 against M13.5's −7.48, on a trace that has been flat for
40 000 steps in three previous milestones.

**e3 reproduces M13.5's i5 independently** — −13.6 / −15.1 against i5's
−14.1 / −15.6 — which is worth its 224 s on its own, because i5 was a single run
and this is the second.

**Neither half works and the pair does.** The fence alone is worth about a
decibel and a half. The tie alone is worth five and stops. Together the energy
falls monotonically through −18.8, −29.3 and −39.9 dB and is still falling when
the reduced step limit stops it — the first `REFCLK` trace in this project's
history that looks like the converging link beside it rather than like a cavity.

That is the reading that makes them **one idea rather than two fixes**: what the
slice was missing is a return path that is a *single conductor*. Tying the supply
plane gives the fourth sheet the same potential as the other three; the fence ties
all four together closely enough that no parallel-plate mode between them has
anywhere to stand. Fix either and three sheets are still a cavity.

### 2.4 What shipped, and what it costs

Three changes in `si/slice.py`, and each one says in its own docstring what it is
approximating and what measurement bought it:

| change | what it does |
|---|---|
| `enclose_vias` | grows the slice rectangle by a fixed 0.8 mm on every side — the clip inset plus the widest via's radius — so a via whose centre is in the pair's own window is in the slice and clear of the outline |
| `_grounded_planes` | ties every zone lying entirely on a layer the stackup declares a `plane` to the reference net, which `reference_net` derives as the net covering the most copper layers across the declared planes and board-scope pours (`GND`, on three layers, against `P3V3` on one) |
| `_fence` | a ring of reference-net vias just inside the outline at a quarter wavelength at the top of the swept band, drilled like the board's own stitching via, skipping any position that would land on somebody's copper |

The module docstring's list of deliberate approximations goes from four to six,
and `docs/format.md` says the same thing for a user: what the two new ones buy,
and what they cost — **the slice can no longer tell anyone that a supply plane is
badly decoupled**, which is a real loss and was never something it could measure.

A first cut of `enclose_vias` grew each side to clear whichever vias it found and
re-scanned, which is a cascade: on `PCIE_TX` each expansion swept in another via
and the window came out **92 % larger** than the pair needed. The constant replaced
it. What the shipped version costs, per slice:

| slice | before | after | area | `GND` vias |
|---|---|---|---|---|
| `PCIE_RXN+PCIE_RXP` | 4.43 × 25.30 | 6.03 × 26.90 | +44.7 % | 7 → 15 |
| `PCIE_TXN+PCIE_TXP` | 4.58 × 25.30 | 6.18 × 26.90 | +43.4 % | 6 → 11 |
| `REFCLKN+REFCLKP` | 5.26 × 25.30 | 6.86 × 26.90 | +38.7 % | 5 → 19 |
| `SATA0_RXN+SATA0_RXP` | 36.85 × 9.14 | 38.45 × 10.74 | +22.6 % | 8 → 21 |
| `SATA0_TXN+SATA0_TXP` | 36.85 × 11.39 | 38.45 × 12.99 | +19.0 % | 7 → 24 |
| `SATA1_RXN+SATA1_RXP` | 36.85 × 9.89 | 38.45 × 11.49 | +21.2 % | 3 → 18 |
| `SATA1_TXN+SATA1_TXP` | 36.85 × 7.64 | 38.45 × 9.24 | +26.2 % | **0 → 16** |
| `SATA2_RXN+SATA2_RXP` | 36.85 × 7.64 | 38.45 × 9.24 | +26.2 % | 2 → 18 |
| `SATA2_TXN+SATA2_TXP` | 36.85 × 9.89 | 38.45 × 11.49 | +21.2 % | 8 → 22 |
| `SATA3_RXN+SATA3_RXP` | 36.85 × 11.39 | 38.45 × 12.99 | +19.0 % | 6 → 21 |
| `SATA3_TXN+SATA3_TXP` | 36.85 × 9.14 | 38.45 × 10.74 | +22.6 % | 6 → 18 |
| **total** | 3 165.7 mm² | 3 931.6 mm² | **+24.2 %** | |

Every slice grows by the same 1.6 mm in each dimension, which is what "bounded"
means here: the cost is a property of the tool, not of where the vias happened to
be. And **no slice on the corpus has a floating plane any more** — the sweep that
found `In2.Cu/P3V3` isolated on eleven of eleven now reports nothing isolated on
any of them.

Three tests hold the result rather than the mechanism:
`test_no_plane_in_a_slice_is_left_floating`,
`test_a_stitching_via_inside_the_window_is_never_dropped` and
`test_every_slice_has_a_ground_reference` — the last of which is `SATA1_TX`'s
finding written as the thing that simply has to be true.

## 3. The probe: two links, through the shipped pipeline

The fix was validated on two links before anything was batched, at full step counts
through `aipcb simulate` itself rather than through the experiment harness — so
what is measured below is the tool, not a hand-edited slice.

### 3.1 `REFCLKN+REFCLKP`: the convergence case, closed

```
aipcb simulate examples/pcie-sata/design.yaml --net REFCLKN
  REFCLKN+REFCLKP    simulated    325 s
```

| | M13 / M13.5 | M13.6 |
|---|---|---|
| energy decay | **−10.2 dB, flat for 42 000 timesteps** | **−63.7 dB, monotonic** |
| how the run ended | `max_steps`, 65 146 | openEMS's own decay criterion, at ts ~56 700 |
| `\|Sdd21\|` | 1.13 | **1.085** |
| `usable` | published as `warn`; M13.5 called it blocked-with-diagnosis | **`true`** |
| skew fit | `under-floor` — floor −34.3 dB, improvement 0.82 dB | **`confident`** — floor −40.4 dB, improvement 12.5 dB, peak 7.4 dB over floor |
| Zdiff | 49.8 Ω (−41.4 %) | 49.53 Ω (−41.7 %) |
| wall clock | 474 s | **325 s** |

**The trapped mode is gone.** The energy trace is the one thing this milestone set
out to change and it changed completely: −18, −29, −39, −56, −60 dB, falling all
the way, and the run stops on decay rather than on the step limit. That is the
first time `REFCLK` has converged on M13b geometry, and it is *faster* than the
non-converging run was — 325 s against 474 s — on a slice 39 % larger, because a
run that converges stops.

**The skew fit crossed from `under-floor` to `confident`**, which is a second
result and arguably the more useful one. M13c built a frequency-domain skew fit and
M13 could never get a usable point out of it: all three links came back
`under-floor`, meaning the fitted skew term did not rise far enough above the
mode-conversion floor to be believed. `REFCLK` now fits 1.065 ps — 0.154 mm — with
a 12.5 dB improvement over a flat floor. It disagrees with the router's geometric
0.359 mm by more than a factor of two, and **that disagreement is now a
measurement rather than a refusal**, which is what two verification layers are for.

**And the impedance did not move.** 49.53 Ω against 49.8 Ω, still −42 % from an
85 Ω target. That is worth stating plainly because it would have been easy to hope
otherwise: the grounding fix repaired the *convergence*, and `REFCLK` remains a
link whose two ends sit on different layers, measured by an estimator that assumes
a uniform line. M13.5 §3's characterisation stands unchanged, and the slice still
carries the note that says so.

### 3.2 `SATA0_RXN+SATA0_RXP`: the non-physical extraction, closed

The link M13.5 re-ran and got nothing usable out of, re-run on the fixed slice:

```
aipcb simulate examples/pcie-sata/design.yaml --net SATA0_RXN
  SATA0_RXN+SATA0_RXP    simulated    2 056 s
```

| | M13.5 | M13.6 |
|---|---|---|
| Zdiff against 100 Ω | **165.15 Ω (+65.1 %)** | **108.26 Ω (+8.3 %)** |
| `\|Sdd21\|` | 1.33 — above phase 0's *broken* slice | **1.130** — under the 1.15 threshold |
| `usable` | **false** | **true** |
| impedance verdict | none; the tool refused to publish one | **`pass`**, and so are the other four |
| energy decay | −33.9 dB | −33.7 dB |
| wall clock | 3 216 s (suite running beside it) | 2 056 s (machine to itself) |

**165 Ω to 108 Ω is the headline.** M13.5 said of the 165 Ω that "it is not a model
error in either direction; it is an extraction that has stopped meaning anything",
and that reading holds: the number did not move because the board changed, it moved
because the model stopped being a board with four isolated sheets of copper in it.
`SATA0_RX`'s slice was missing one of its nine ground vias and its supply plane
floated; with both fixed the same copper reads 8.3 % high, inside the ±10 % band,
and every verdict passes. **This is the first SATA link on M13b geometry to come
back usable.**

Two things about it that are less good than the headline, and both are said here
rather than left for a reader to find.

**The energy decay did not improve, and neither did the cost.** −33.7 dB against
−33.9, and the run still stops on `max_steps` rather than on decay. `REFCLK` got
*faster* because it now converges and stops early; `SATA0_RX` did not, because it
still does not converge — it is simply no longer trapping enough energy to wreck the
extraction. So the grounding fix repaired the physics on this link and **not** the
conditioning: at 2 056 s against M13.5's ~2 220 s idle projection, a SATA link
costs what it always did. The milestone's expectation that these would "run
meaningfully faster" is not borne out, and the eight-link arithmetic is unchanged.

**`|Sdd21| = 1.130` is inside the usable band but outside the converged one.** M12's
genuinely converged runs sit at 1.07–1.09; `REFCLK` now sits at 1.085 and this sits
at 1.130. The tool's own note says what that means — truncation noise bounding the
accuracy "at a few percent" — and on a number reading +8.3 % against a ±10 % band,
a few percent is the difference between a pass and a warn. **The verdict is real and
it is not comfortable**, and the honest statement is that `SATA0_RX` passes on a
measurement whose error bar reaches the edge of the band it passes inside.

One quirk this surfaced and did not cause: `insertion_loss_db` is
`20·log₁₀|Sdd21|`, so an extraction with excess gain reports *positive* insertion
loss — here +1.06 dB at 3 GHz — and the verdict compares it against a −3 dB
threshold and passes. An insertion-loss verdict cannot fail on excess gain. That is
pre-existing, it is not what this milestone was about, and it is now on the roadmap.

### 3.3 One note on the acceptance criterion itself

The milestone asks for `|Sdd21| ≤ 1`, and **no run this pipeline has ever produced
meets that, including the ones that are known to be right.** The threshold in
`si/results.py` is calibrated rather than chosen, and its own comment says why:

> phase 0's coarse, non-converging diff-pair slice peaks at **1.166**, while M12's
> `mcu-4layer` runs — whose impedance agrees to 1.2 % across a 4.5× change in mesh
> density, so they *are* converged — peak at **1.07 and 1.09**.

A little excess gain is the truncation error of a finite run, and a converged FDTD
result on this pipeline carries about 7 to 9 % of it. So `≤ 1` is not a test of
whether the physics is sound; it is a test of whether the solver ran forever.

The criterion actually worth applying, and the one used below, is the tool's own:
**`usable` — at or under 1.15** — with the 1.07–1.09 band of M12's converged runs
as the target rather than the limit. Read that way the M13 numbers were
unambiguous: `PCIE_TX` at 1.23 and `SATA0_RX` at 1.33 are both above phase 0's
*broken* slice, not marginally over unity.

## 4. The batch: eleven links on grounded slices

Step 3's criteria were met, so the batch ran: all eleven links, on slices whose
geometry had changed, so every cache entry invalidated itself and nothing was
reused. **15 428 s of wall clock — 4 h 17 min — for 17 755 s of solver time.**

### 4.1 What eleven links look like on a slice with a return path

| Link | Target | M13.6 Zdiff | Deviation | `\|Sdd21\|` | Energy | `usable` | Verdict | Wall |
|---|---|---|---|---|---|---|---|---|
| `PCIE_TXN+PCIE_TXP` | 85 Ω | **79.29 Ω** | −6.7 % | 1.220 | −64.6 dB | **false** | `unusable` | 142 s |
| `PCIE_RXN+PCIE_RXP` | 85 Ω | **72.97 Ω** | −14.1 % | 1.000 | −61.5 dB | **true** | `warn` | 176 s |
| `REFCLKN+REFCLKP` | 85 Ω | **49.53 Ω** | −41.7 % | 1.085 | −63.7 dB | **true** | `warn` | 325 s |
| `SATA0_TXN+SATA0_TXP` | 100 Ω | **95.05 Ω** | −5.0 % | 1.059 | −30.6 dB | **true** | `pass` | 2564 s |
| `SATA0_RXN+SATA0_RXP` | 100 Ω | **108.26 Ω** | +8.3 % | 1.130 | −33.6 dB | **true** | `pass` | 2056 s |
| `SATA1_TXN+SATA1_TXP` | 100 Ω | **103.59 Ω** | +3.6 % | 1.106 | −35.5 dB | **true** | `pass` | 1658 s |
| `SATA1_RXN+SATA1_RXP` | 100 Ω | **85.77 Ω** | −14.2 % | 1.031 | −30.6 dB | **true** | `warn` | 2147 s |
| `SATA2_TXN+SATA2_TXP` | 100 Ω | **85.71 Ω** | −14.3 % | 1.010 | −28.2 dB | **true** | `warn` | 2480 s |
| `SATA2_RXN+SATA2_RXP` | 100 Ω | **86.76 Ω** | −13.2 % | 1.000 | −32.0 dB | **true** | `warn` | 1408 s |
| `SATA3_TXN+SATA3_TXP` | 100 Ω | **89.10 Ω** | −10.9 % | 1.000 | −31.2 dB | **true** | `warn` | 2318 s |
| `SATA3_RXN+SATA3_RXP` | 100 Ω | **90.51 Ω** | −9.5 % | 1.000 | −30.3 dB | **true** | `pass` | 2479 s |

**Ten of eleven are physical, and the eleventh is the one this milestone did not
touch.** Every SATA link now returns a number a person can act on, where M13 had
none of them and M13.5 had one that read 165 Ω. Seven of the eleven have `|Sdd21|`
at or under 1.06 — inside the band M12's convergent runs occupy — and four are at
exactly 1.000.

### 4.2 The per-link contrast, which is where the fix is visible

| Link | M12 (pre-M13b geometry) | M13 / M13.5 (M13b geometry) | M13.6 (M13b + grounded slice) |
|---|---|---|---|
| `PCIE_TXN+PCIE_TXP` | 66.6 / −21.6 % | 80.0 / −5.8 %, \|Sdd21\| 1.23, `usable: false` | **79.29 Ω / −6.7 %**, \|Sdd21\| 1.220, `usable: false` |
| `PCIE_RXN+PCIE_RXP` | 61.5 / −27.6 % | 72.8 / −14.4 %, usable | **72.97 Ω / −14.1 %**, \|Sdd21\| 1.000, `usable` |
| `REFCLKN+REFCLKP` | 50.9 / −40.1 % | 49.8 / −41.4 %, energy −10.2 dB, `warn` | **49.53 Ω / −41.7 %**, \|Sdd21\| 1.085, `usable` |
| `SATA0_TXN+SATA0_TXP` | 85.1 / −14.9 % | not run | **95.05 Ω / −5.0 %**, \|Sdd21\| 1.059, `usable` |
| `SATA0_RXN+SATA0_RXP` | 91.9 / −8.1 % | **165.2 / +65.1 %**, \|Sdd21\| 1.33, `usable: false` | **108.26 Ω / +8.3 %**, \|Sdd21\| 1.130, `usable` |
| `SATA1_TXN+SATA1_TXP` | 90.0 / −10.0 % | not run | **103.59 Ω / +3.6 %**, \|Sdd21\| 1.106, `usable` |
| `SATA1_RXN+SATA1_RXP` | 81.0 / −19.0 % | not run | **85.77 Ω / −14.2 %**, \|Sdd21\| 1.031, `usable` |
| `SATA2_TXN+SATA2_TXP` | 76.4 / −23.6 % | not run | **85.71 Ω / −14.3 %**, \|Sdd21\| 1.010, `usable` |
| `SATA2_RXN+SATA2_RXP` | 80.0 / −20.0 % | not run | **86.76 Ω / −13.2 %**, \|Sdd21\| 1.000, `usable` |
| `SATA3_TXN+SATA3_TXP` | 62.5 / −37.5 % | not run | **89.10 Ω / −10.9 %**, \|Sdd21\| 1.000, `usable` |
| `SATA3_RXN+SATA3_RXP` | 67.7 / −32.3 % | not run | **90.51 Ω / −9.5 %**, \|Sdd21\| 1.000, `usable` |

The middle column is empty on seven rows, and that emptiness is the honest part:
**M13 and M13.5 between them measured four of the eleven links on M13b geometry**,
so for the other seven there is no same-geometry number to contrast against. M12's
column is on *pre-M13b* copper — wider traces, derived from the bare-microstrip
model ADR 0012 replaced — so a row like `SATA3_TX` moving 62.5 → 89.10 Ω is two
changes at once and attributes to neither on its own.

Where the contrast **is** clean, on the four links that have both:

* **`SATA0_RX`: 165.2 Ω → 108.26 Ω.** The extraction M13.5 called one that "has
  stopped meaning anything" now reads 8.3 % high and passes every verdict. Same
  copper, same mesh, same band; the model stopped having four isolated sheets of
  metal in it.
* **`REFCLK`: the impedance did not move and the physics did.** 49.8 → 49.53 Ω,
  and energy −10.2 dB → −63.7 dB. §3.1.
* **`PCIE_RX`: nothing moved, and that is the control.** 72.8 → 72.97 Ω, and it
  was already the one link M13.5 found usable. A fix that had changed this number
  would have needed explaining.
* **`PCIE_TX`: nothing moved, and that is a finding.** 1.23 → 1.220, still
  `usable: false`. §4.3.

`SATA1_TX` deserves its own line even without a comparison, because it is the
slice that had **no ground via of any kind** — four isolated sheets under a 100 Ω
microstrip. It now reads **103.59 Ω, +3.6 %**, one of the two closest-to-target
numbers on the board.

### 4.3 `PCIE_TX` is still not physical, and it refutes M13.5's explanation

One link is `usable: false`, at `|Sdd21|` 1.220 against 1.23 before. **The
acceptance clause asking for eleven physical extractions is therefore not met, at
ten of eleven.**

What makes it worth more than an apology is that it disproves the reading M13.5
attached to it. M13.5 wrote:

> The common thread is incomplete decay, not coupling capacitors — which puts it in
> the same family as §4 rather than in the family M13 filed it under.

With the grounding defect out of the way, decay and gain are no longer related at
all:

| link | energy decay | `\|Sdd21\|` | `usable` |
|---|---|---|---|
| `PCIE_TXN+PCIE_TXP` | **−64.6 dB — the furthest on the board** | **1.220** | **false** |
| `REFCLKN+REFCLKP` | −63.7 dB | 1.085 | true |
| `PCIE_RXN+PCIE_RXP` | −61.5 dB | **1.000** | true |
| `SATA2_TXN+SATA2_TXP` | −28.2 dB — the least | 1.010 | true |

The link that decays furthest has the worst gain and the link that decays least is
clean. Incomplete decay was a real effect and it was *this milestone's* defect
wearing a disguise; on eleven links with a working return path it explains nothing.

`PCIE_TX` is the only link on this board carrying **AC-coupling capacitor
bridges** — `C2` and `C3`, `role: ac_coupling`, replaced by copper in the slice.
That was M13's original suspect, set aside by M13.5 for the decay explanation that
has now failed. The correlation is one link out of eleven and it is exact, which is
suggestive and is not a measurement: **one clean bridged sample is not evidence
about bridges.** It is the next single hypothesis, it is testable the way this
milestone's was — slice the pair with the bridge and without it and compare — and
it is on the roadmap rather than done here, because this milestone had a
hypothesis and finished it.

### 4.4 The skew fit, at full coverage for the first time

| Link | Budget | Geometric | Slice's own | Fitted Δτ | as length | Floor | Peak over floor | Improvement | Verdict |
|---|---|---|---|---|---|---|---|---|---|
| `PCIE_TXN+PCIE_TXP` | 0.127 mm | 0.247 mm | 0.439 mm | 0.00 ps | 0.000 mm | −18.3 dB | −281.7 dB | 0.00 dB | `under-floor` |
| `PCIE_RXN+PCIE_RXP` | 0.127 mm | 0.219 mm | 0.219 mm | 0.00 ps | 0.000 mm | −24.5 dB | −275.5 dB | 0.00 dB | `under-floor` |
| `REFCLKN+REFCLKP` | 0.127 mm | 0.359 mm | 0.359 mm | 1.06 ps | 0.154 mm | −40.4 dB | +7.4 dB | 12.52 dB | **confident** |
| `SATA0_TXN+SATA0_TXP` | 0.250 mm | 0.029 mm | 0.029 mm | 0.00 ps | 0.000 mm | −27.5 dB | −272.5 dB | 0.00 dB | `under-floor` |
| `SATA0_RXN+SATA0_RXP` | 0.250 mm | 0.041 mm | 0.041 mm | 0.93 ps | 0.141 mm | −48.3 dB | +14.1 dB | 3.88 dB | **confident** |
| `SATA1_TXN+SATA1_TXP` | 0.250 mm | 0.000 mm | 0.000 mm | 0.98 ps | 0.149 mm | −35.1 dB | +1.0 dB | 1.53 dB | `under-floor` |
| `SATA1_RXN+SATA1_RXP` | 0.250 mm | 0.038 mm | 0.038 mm | 1.03 ps | 0.156 mm | −65.1 dB | +31.0 dB | 5.87 dB | **confident** |
| `SATA2_TXN+SATA2_TXP` | 0.250 mm | 0.038 mm | 0.038 mm | 0.68 ps | 0.103 mm | −44.1 dB | +6.0 dB | 1.58 dB | `under-floor` |
| `SATA2_RXN+SATA2_RXP` | 0.250 mm | 0.000 mm | 0.000 mm | 1.73 ps | 0.263 mm | −32.9 dB | +2.0 dB | 5.37 dB | `under-floor` |
| `SATA3_TXN+SATA3_TXP` | 0.250 mm | 0.041 mm | 0.041 mm | 0.60 ps | 0.092 mm | −33.9 dB | −6.2 dB | 0.20 dB | `under-floor` |
| `SATA3_RXN+SATA3_RXP` | 0.250 mm | 0.029 mm | 0.029 mm | 0.00 ps | 0.000 mm | −26.8 dB | −273.2 dB | 0.00 dB | `under-floor` |

M13c built this fit and M13 could never get a usable point out of it: three links
measured, all three `under-floor`, and M13.5 recorded that "the false-positive rate
is still nought out of three, which is still not a rate". **There are now eleven
links and three confident fits**, and what they say is not comfortable:

| link | geometric | fitted | disagreement |
|---|---|---|---|
| `REFCLKN+REFCLKP` | 0.359 mm | 0.154 mm | fit reads **2.3× low** |
| `SATA0_RXN+SATA0_RXP` | 0.041 mm | 0.141 mm | fit reads **3.4× high** |
| `SATA1_RXN+SATA1_RXP` | 0.038 mm | 0.156 mm | fit reads **4.1× high** |

Three confident fits, three disagreements with the router's own measurement, in
both directions. That is the first real evidence about the fit's accuracy this
project has had, and it is evidence *against* it: on clean physics, at floors of
−40 to −65 dB, the frequency-domain estimate of intra-pair skew does not reproduce
the geometry. **No verdict flips on it** — the SATA fits are under a 0.250 mm
budget and `REFCLK` is over its 0.127 mm budget on both measurements — so nothing
downstream is wrong today. What has changed is that the question is now answerable
and the answer is not "they agree".

**And the refusal earned its keep.** `SATA2_RX` fits **0.263 mm** against a
geometric skew of **0.000 mm** — a fit that would have flagged a perfectly matched
pair as over a 0.250 mm budget, and the `under-floor` rule refused to publish it.
That is what M13c built the floor test for, caught in the act, on a link nobody had
run before.

### 4.5 The two layer-spanning links, re-evaluated

The milestone asked whether `PCIE_RX` and `REFCLK` still need the estimator caveat
with clean physics, or extract sensibly now. **They still need it, and the case for
it is stronger than it was.**

| | `PCIE_RXN+PCIE_RXP` | `REFCLKN+REFCLKP` | every link that does not span layers |
|---|---|---|---|
| deviation | −14.1 % | **−41.7 %** | −14.3 % to +8.3 % |
| energy | −61.5 dB | −63.7 dB | −28.2 to −35.5 dB |
| `\|Sdd21\|` | 1.000 | 1.085 | 1.000 to 1.130 |

The two worst-converged links on the board are not these two — these two are the
*best* converged, and they are still the two furthest from target, with `REFCLK` at
−41.7 % more than twice as far out as anything else. Every alternative explanation
M13.5 listed has now been eliminated by measurement: not a truncated run
(−63.7 dB), not a floating reference (tied), not missing ground (16–19 vias). What
is left is the one M13.5 named: the estimator is a median input impedance, which is
the characteristic impedance of a uniform line, and a link with a via transition
and a change of reference plane in the middle of it is not one. The caveat stays on
the output and the roadmap keeps the two ways out — widen the sweep to 20 GHz, then
port each section separately.

## 5. What M13.5 left open, and where each stands

| M13.5's open item | M13.6 |
|---|---|
| *"`REFCLK`'s trapped mode is located to within 4–5 dB, and not fully"* | **Closed.** The other part was the ground structure the slice was cutting: 22 of 41 stitching vias lost to the clip band, and a boundary that ends the pours in mid-air. Energy now decays 63.7 dB. §2, §3 |
| *"Energy is not leaving these slices, and it is not one link's problem"* | **Answered, and it was not one link's problem.** The floating supply plane and the missing ties are on all eleven slices, and M13.5's guess that this gated every remaining simulation was right |
| *"`aipcb simulate` has no cost model"* | **Not built.** The timeout is now a documented design parameter sized from measured runtimes (§4), which is the part that stops a batch reporting nothing; a slice still cannot say what it will cost before the container starts |
| *"The impedance estimator assumes a uniform line and nothing enforced it"* | **Unchanged, and now measured on clean physics.** `REFCLK` converged and still reads −41.7 %; the estimator is the reason, exactly as M13.5 §3 said, and widening the sweep to 20 GHz so a TDR can separate the two sections is still not done |
| *"`preserve.py`'s premise is fixed where it bit and not where it lives"* | **Unchanged in the module, swept for elsewhere.** §1.2 found no other command reading its own output; `build` over a routed board would still preserve aipcb's copper as a human's, and nothing in the corpus does that |
| *"The four over-budget PCIe pairs still need geometry"* | **Untouched, by the guardrail.** Still on the roadmap |
| *"M12's deliberately degraded case is still not run"* | **Still not run.** Four milestones have now named it |

## 6. What changed, and what it cost

### Source

| file | what |
|---|---|
| `si/slice.py` | `enclose_vias`, `reference_net`, `_grounded_planes`, `fence_pitch_mm`, `_fence`, `_fence_via`, `_via_radius`; the module's list of deliberate approximations goes from four to six |
| `si/runner.py` | `DEFAULT_TIMEOUT_S` 1800 → 7200, with the three measurements it is sized from written beside it |
| `model/simulation.py` | `SimulationSettings.timeout_s`, carried into `ResolvedSimulation` |
| `si/run.py`, `cli_simulate.py` | `--timeout` is now optional and falls back to the design's `simulation.timeout_s` |
| `examples/pcie-sata/design.yaml` | `timeout_s: 7200`, with the reason attached. **No copper moves** — the three golden files are byte-identical |
| `docs/format.md` | `timeout_s` documented as a budget rather than an estimate; the approximations list goes from three (four were listed, miscounted) to five, with what the return-path fix costs stated |
| `docs/reports/reverification-note.md` | new: which recorded measurements the `check` defect could have reached |

### Tests

The suite grew by **eight**, and every one exists because something here was found
by measuring:

| test | what it holds |
|---|---|
| `test_checking_three_times_changes_nothing` | `check` is stationary, not merely equal on the first repeat |
| `test_checking_the_flagship_board_three_times_changes_nothing` | the same on `pcie-sata`, where the drift was measured |
| `TestBuildIsAFunctionOfTheSource` | `build` ×3 into one directory: declared zones do not double |
| `TestExportIsAFunctionOfTheSource` | `export --build-dir` ×3: same board, same fabrication package |
| `TestSimulateIsAFunctionOfTheSource` | `simulate --dry-run` ×3 into one `--out`: same slice, same digest, same Gerbers |
| `TestSyncPlacementIsAFunctionOfItsInputs` | a report writes nothing, twice |
| `test_the_sweep_covers_every_command_that_writes_where_it_reads` | a twelfth command cannot join without declaring which side of the line it is on |
| `test_no_plane_in_a_slice_is_left_floating` | every declared plane in every slice carries the reference net |
| `test_a_stitching_via_inside_the_window_is_never_dropped` | a via inside the window is in the slice, or the slice says why |
| `test_every_slice_has_a_ground_reference` | `SATA1_TX`'s finding, written as the thing that has to be true |

### Gates

| check | result |
|---|---|
| `pytest -q` | **exit 0 — 1 192 passed, 2 skipped, 26 m 01 s** (1 194 collected, up from 1 182) |
| `ruff check .` | **All checks passed** |
| `mypy --strict src/aipcb` | **Success: no issues found in 86 source files** |

**26 m 01 s is a real baseline again.** M13.5's 30 m 31 s was measured with a SATA
solver running beside it for the first forty per cent, which that report said rather
than reporting as a regression; this one ran with the machine to itself, and against
M13's clean 24 m 18 s the suite is 103 s slower for twelve more tests, four of which
build and route boards.

The second skip is new and deliberate: `test_checking_the_flagship_board_three_times_changes_nothing`
is 45 s a run and sits behind `AIPCB_FULL_CORPUS=1`, beside the `test_sexpr_corpus`
skip that has been there since M1.

### Output

| | |
|---|---|
| `.kicad_pcb`, `.kicad_sch`, `.kicad_pro` | **byte-identical on all eleven examples.** No copper moved and no project setting changed; the only source edit to a design is `simulation.timeout_s`, which does not reach the board, verified by SHA-256 against the goldens |
| `check` on `pcie-sata` | unchanged: 90/90 connections, 1 108.092 mm, 42 vias, 0 errors, 7 warnings |
| slices | **every one of them different**, which is the point: +0.8 mm on each side, +24.2 % area, and 11–24 ground vias each where the range was 0–8 |

### Simulation time spent, per step

M12's eleven links cost **7 837 s**. M13.5 spent **5 957 s**. M13.6:

| step | what it needed | solver time |
|---|---|---|
| 1 — idempotence and the sibling sweep | building, routing and checking boards | **0 s** |
| 2 — the slice artifacts | filling eleven slices and intersecting geometry | **0 s** |
| 2 — attributing the fix | four runs at 32 000 steps: 209, 232, 223, 224 s | **888 s — 15 min** |
| 3 — the two probe links | `REFCLK` 369 s, `SATA0_RX` 2 100 s, wall clock | **2 469 s — 41 min** |
| 3 — a probe run thrown away | started before the `enclose_vias` cascade was found and killed when it was; produced nothing | **~200 s** |
| 4 — the batch | nine links solved, two cache hits | **15 428 s — 4 h 17 min** |

**About 5 h 16 min in total, and the shape of it is the point.** The two steps that
answered the milestone's question cost **nothing and fifteen minutes**: the artifact
measurement that refuted the premise was geometry on files already on disk, and the
attribution that made the fix defensible was four reduced-step runs that reused an
already-generated slice. The four hours went on the batch, which is *reporting*
rather than *finding out* — and it was only worth spending because step 3 had
already established that it would not buy eleven more unusable numbers.

The 200 s that bought nothing is written down on purpose. The first `enclose_vias`
grew the rectangle to clear whichever vias it found and re-scanned; the probe was
launched against those slices, and when the `PCIE_TX` cascade turned up the run was
killed rather than allowed to finish and be reported as the shipped geometry. That
is 200 s well spent and it is still 200 s.

## 7. What M13.6 leaves open

* **`PCIE_TX` is the only link on this board that is not physical, and the only one
  with capacitor bridges.** One sample, an exact correlation, and a refuted
  alternative explanation. The experiment is the same shape as this milestone's:
  slice the pair with the bridge and without it, at reduced steps, and compare. §4.3
* **The skew fit disagrees with the router on all three links that can now be
  believed**, by 2.3× to 4.1× and in both directions. Nothing downstream is wrong
  today because no verdict turns on it, and that is luck rather than design. §4.4
* **A SATA link still costs 35 minutes**, and the grounding fix did not change that.
  What did change is that the 35 minutes now buys a number. §3.2
* **openEMS is using four or five of sixteen cores**, and ADR 0011 Decision 4
  declined process-level parallelism on the premise that it used all of them.
  Measured, not fixed; on the roadmap with the numbers attached.
* **The two layer-spanning links still carry the estimator caveat**, and every
  alternative explanation for it has now been eliminated by measurement rather than
  argued away. §4.5
* **`preserve.py`'s premise is still wrong where it lives.** The sweep found no
  second command reading its own output, so nothing is broken today; `build` over a
  routed board would still preserve aipcb's own copper as a human's.
* **M12's deliberately degraded case is still not run.** Four milestones have now
  named it, and with eleven links that converge and a fit that can be believed on
  three of them, it is a better experiment than it has ever been.

# M13.7 — the bridge that was not the problem, the invariant that is now a check, and the parallelism that is not a win

Three items, each sharply bounded, and **two of the three came back negative**. That
is the shape of the milestone: one hypothesis was tested and refuted, one lesson was
locked in and swept clean, and one measured performance win turned out, when
measured, not to exist. All three are worth the time they cost, and only one of them
is a fix.

`PCIE_TX` is **still not physical**, so M13's acceptance clause stays open at ten of
eleven. What moved is that the coupling-capacitor explanation — the last one
standing since M13 — is now eliminated by measurement rather than by argument, and
the signature that replaces it is sharper than anything before it.

Everything below was measured on 2026-08-22 on the same machine as M13.6 (16 CPUs
on 10 hybrid cores, 30 GB, openEMS `v0.0.36-142-g32c5c6b` in the pinned
`gerber2ems:phase0` image), with the machine otherwise idle unless a line says
otherwise.

## What M13.7 found, in one table

| question | answer |
|---|---|
| Is the AC-coupling bridge's geometry wrong? | **No.** Measured off the slice artifact: same layer as the pads it joins, same width as the trace (0.1846 mm), spanning exactly the 0.96 mm between the two cap pads, at the 1.4 mm pitch the board's own fanout puts them at. The pair's width and coupling through the cap region are the board's, not the slicer's. §1.1 |
| Was anything about the bridge wrong? | **Yes, and not geometrically: it carried no net.** It was the only unnetted copper in any slice on the corpus, and gerber2ems adds mesh lines only for the nets in `netinfo.json` — so the one piece of copper sitting on the discontinuity was the one piece the grid generator never resolved. §1.2 |
| Does fixing that close `PCIE_TX`? | **No.** The mesh went 0.78 M → 0.94 M cells and the coarsest cell across the bridge 79.9 → 33.5 µm, and the number did not move: \|Sdd21\| 1.220 → **1.22**, Zdiff 79.29 → **79.59 Ω**, energy −64.6 → −66.4 dB. The hypothesis is refuted and the fix is kept. §1.3 |
| Then what is `PCIE_TX`? | **Open, with a sharper signature.** The excess gain is already there *single-ended*: \|S(4,3)\| = 1.112 against \|S(2,1)\| = 1.003 at the 6.25 GHz peak. One half of the pair gains eleven per cent on its own, before any mixed-mode arithmetic, and the two halves are not alike. That points at the ports, not the interior. §1.4 |
| Does any slice on the corpus violate the return-path invariant? | **No — sixteen slices across four examples, all clean.** Which is the answer a new invariant should give on a corpus that was just fixed, and it now costs 12 ms a slice to keep giving it. §2.2 |
| Was the clip band still eating vias? | **Yes: 19 across the eleven slices, 16 of them stitching.** M13.6 grew the window by a bounded 0.8 mm and closed the *symptom*; it did not close the class, and nobody could see the residue because nothing reported it. Every one of the 19 is now named, with its net and its position. §2.3 |
| Does running three solvers at once help? | **No — it is 48 % slower.** 693 s sequential against **1 023 s** concurrent, with aggregate throughput (316 MC/s) *below what one solver gets alone* (489–619). What runs out is memory bandwidth, which is also why openEMS declines the spare cores in the first place. §3 |

## Acceptance, clause by clause

| Clause | What happened |
|---|---|
| *"`PCIE_TX`: physical with the table at 11/11, or characterized-and-stopped with the signature recorded"* | **Characterized and stopped.** One hypothesis, one fix, one run, and the fix did not move the number: 1.220 → 1.22. §1.4 records the replacement signature — single-ended gain, asymmetric between the halves, rising to a peak at 6.25 GHz — and the roadmap carries it as the next hypothesis. No second theory was tried. The table stays at **ten of eleven**. |
| *"The slice-validity invariant active with its tests"* | **Met.** `si/integrity.py` runs on every slice at generation, refuses one whose copper is not all bonded or whose declared `reference:` plane the model does not reach, and names the layer, the net and the area rather than the rule. Four tests, including M13.6's defect reconstructed and refused. §2 |
| *"Via removal loud everywhere; the M13.6 reporting asymmetry impossible to reintroduce silently"* | **Met.** Both bands that remove a via record it, in one `RemovedVia` list the slice carries and its summary counts. The test that used to accept "a note exists" now compares what is missing against what was recorded, so a third band could not be added silently either. §2.3 |
| *"Parallelism implemented, measured, ADR corrected"* | **Met, and the measurement went the other way.** `--parallel N` ships with a cpuset per solver where the host allows one; ADR 0011 gains Decision 4a with the table. The correction is in two parts: the old premise was false *and* the old conclusion was right, for a reason it never gave. §3 |
| *"Suite green, mypy strict, ruff clean, byte-stable"* | See §4. |

## 1. `PCIE_TX`: the bridge hypothesis, tested and refuted

### 1.1 What the bridge actually is

Free first, and from the artifact rather than from the code. `PCIE_TX` is the only
pair on this board split by `role: ac_coupling` parts, and its slice replaces `C2`
and `C3` with copper. Read out of `slice.kicad_pcb`:

```
(segment (start 139.3 130.52) (end 139.3 131.48) (width 0.1846) (layer "F.Cu") (net 0))
(segment (start 140.7 130.52) (end 140.7 131.48) (width 0.1846) (layer "F.Cu") (net 0))
```

Against the copper on either side of them:

| | the run | at the caps |
|---|---|---|
| trace width | 0.1846 mm | **0.1846 mm** — the same |
| layer | `F.Cu` | **`F.Cu`** — the same |
| pair pitch | 0.3346 mm (0.15 mm gap) | **1.4 mm** — which is where `C2` and `C3` are |
| length bridged | — | 0.96 mm, pad centre to pad centre |

**None of the three defects the milestone anticipated is present.** The bridge is
not a naive strap that breaks the pair's width, it is not on the wrong layer, and
the 1.4 mm pitch is not the slicer's — it is the board's own fan-out to reach the
capacitors, which `check` already reports as an `ac-coupling` note and counts
against `max_uncoupled_mm`. What the slice does lose is the 0402 pads themselves,
which is the documented "footprints are dropped" approximation applying here as it
does at every port on every link.

### 1.2 The one thing that was wrong, and it is not geometry

`(net 0)`. Both bridges carried no net, and in the exported Gerber that is one
`%TO.N,*%` block:

```
%TO.N,*%
X3792300Y14922300D02*
X3792300Y13962300D01*
X2392300Y14922300D02*
X2392300Y13962300D01*
```

That matters here more than it would anywhere else, because of how the mesh is
built. `gerber2ems/grid_gen.py` reads the nets under test out of `netinfo.json` and
adds grid lines from *those* nets' traces:

```python
nets = [net["name"] for net in netinfo["nets"]]
for gbr in gerbers:
    for net in nets:
        trace = gbr.traces.get(net, Trace([]))
        self.x.add_lines_from_trace(trace.segments)
```

Copper the Gerber labels `no-net` is still simulated — the importer rasterises every
layer — but it gets no edge cells, so its width and position land wherever the grid
happens to fall. **The bridge was the only unnetted copper in any slice on this
corpus**, and it sat exactly on the discontinuity a run is trying to resolve. This
is also the third instance of the failure mode `si/run.py` already guards against by
reading the Gerbers back — and it slipped past that guard, because the guard checks
`sliced.pair.nets` and the bridge was on none of them.

**The fix.** The bridge is emitted as two halves meeting at the midpoint, each
carrying the net of the pad it starts from. The geometry is byte-for-byte the same
line; what changes is that both sides of the cap are now nets under test:

```
(segment (start 139.3 130.52) (end 139.3 131)    ... (net 6))   ; PCIE_TXP
(segment (start 139.3 131)    (end 139.3 131.48) ... (net 7))   ; PCIE_TXP_C
```

The two halves touch, which is the short the bridge *is*.

**What it bought, measured with the geometry pass alone** (`gerber2ems -g`, no
solver, four seconds):

| | before | after |
|---|---|---|
| grid lines, x | 69 | **81** |
| grid lines, y | 269 | 277 |
| total cells | **0.78 M** | **0.94 M** |
| coarsest cell across the `PCIE_TXP` bridge | **79.9 µm** | **33.5 µm** |
| coarsest cell across the trace it continues | 45.7 µm | 45.7 µm |

So the bridge was being meshed about twice as coarsely as the line it interrupts,
and now it is not. That is a real defect, measured, and fixed.

### 1.3 It is not what makes `PCIE_TX` non-physical

One simulation, as the milestone allowed:

```
aipcb simulate examples/pcie-sata/design.yaml --net PCIE_TXN
  PCIE_TXN+PCIE_TXP        simulated    199.0 s
```

| | M13.6 | M13.7 |
|---|---|---|
| Zdiff against 85 Ω | 79.29 Ω (−6.7 %) | **79.59 Ω (−6.4 %)** |
| \|Sdd21\| | 1.220 | **1.22** |
| `usable` | false | **false** |
| energy decay | −64.6 dB | −66.4 dB |
| cells | 0.78 M | 0.94 M |
| wall clock | 142 s | **199 s** (+40 %, against +21 % cells) |

**The hypothesis is refuted.** A 21 % finer mesh, concentrated exactly where the
suspect was, moved the impedance by 0.4 % and the excess gain by nothing. The fix is
kept anyway — unnetted copper in a slice is a defect whatever it does to this link,
and it is the sort that produces a confident wrong answer elsewhere — but it is
kept as a fix, not as an explanation.

Per the milestone's guardrail, no second hypothesis was tried and no second run was
spent. The first fix had no implementation error to re-run: the netting is visible
in the Gerber, the mesh refinement is visible in the grid, and the run completed
normally.

### 1.4 The signature that replaces it

What is worth carrying forward is that the new evidence is more specific than the
old. Reading the raw four-port matrix at the 6.25 GHz peak, **before any mixed-mode
combination**:

| | \|S\| |
|---|---|
| `S(2,1)` — through, one half of the pair | **1.003** |
| `S(4,3)` — through, the other half | **1.112** |
| `S(1,1)` | 0.226 |
| `S(3,3)` | 0.339 |

**The excess gain is single-ended and it is asymmetric.** One conductor returns
eleven per cent more than went into it on its own; mixed-mode arithmetic is not
manufacturing this, it is only averaging it. And across the band the differential
excess is not noise but a shape — 0.956 at 0.5 GHz, 1.113 at 1.5, 1.141 at 3,
**1.220 at 6.25**, 1.108 at 8 — rising to a peak inside the band and falling above
it.

That points at the ports rather than at the interior of the line, and this link has
something specific about its ports: it launches at **0.5 mm pitch** at the
controller end and **1.0 mm at the card edge**, against a coupled run at 0.3346 mm.
Both ports therefore sit on geometry whose differential impedance is a long way from
the 85 Ω they are terminated at, *and the two ends sit on different such geometries*
— which is the asymmetry the single-ended numbers show. The impedance profile agrees
that the structure is strongly non-uniform: 47.4 Ω minimum, 123.1 Ω maximum, 79.6 Ω
median.

This is the next hypothesis and it is on the roadmap, not in this milestone. Stated
so the next person can test it the way the last two were tested: it predicts that
the excess gain scales with the launch-to-line pitch mismatch, so it is checkable by
slicing a link whose ends and run share a pitch and one whose ends do not, and
comparing — with no change to the tool at all.

## 2. The invariant, and the removal that stopped being quiet

### 2.1 What the check is, and what it deliberately is not

M13.6 proved one sentence with four solver runs: **a slice's return path has to be a
single connected conductor.** M13.7 stops taking it on trust. `si/integrity.py`
walks a slice's copper once and answers two questions:

* **Is every sheet of area copper bonded to the others?** A zone declared on three
  layers is *three* sheets until a via joins them, so zones are exploded per layer
  and the vias are what put them back together. Connectivity is net-gated, which is
  KiCad's own rule: a GND via inside a GND pour ties it, a signal via crossing the
  same pour does not.
* **Is the plane the pair's class names as its `reference:` one of them?** An
  impedance number is a statement about a line *and* its return path.

Either violation raises `SliceError` with `fatal=True`, which `si/run.py` turns into
an **error** and a `failed` pair rather than the warning an unrouted pair gets. The
distinction is whether carrying on would produce a *number*.

The message names the copper, not the rule:

```
PCIE_RXN+PCIE_RXP's slice leaves copper at no defined potential:
In2.Cu (P3V3), 151 mm2. A return path that is not one conductor is a
resonator, and the impedance it produces is not the board's
```

**What it cannot see, said out loud.** The slice is checked *before* it is filled —
no `kicad-cli`, no `pcbnew`, because this has to be cheap enough to run on every
slice every time — so a zone's copper is its outline rather than its poured polygon.
That answers "is this sheet tied to anything", which is the question M13.6's defect
turned on. It does not answer "is this sheet in one piece once it is filled", which
is `checks/planes.py`'s question, on the real board, where the fill exists. The two
are deliberately not merged.

### 2.2 The sweep: sixteen slices, four examples, nothing floating

The invariant was run against every simulatable pair in the corpus before anything
was written about it:

| example | pairs | verdict | cost per slice |
|---|---|---|---|
| `pcie-sata` | 11 | all clean | 18–41 ms total build, of which **~12 ms is the check** |
| `usb-port` | 2 | all clean | 10–17 ms |
| `mcu-4layer` | 2 | all clean | 9–13 ms |
| `diff-pair` | 1 | clean | 8 ms |

**Nothing failed, which is the answer a new invariant should give on a corpus that
was just repaired** — M13.6 fixed exactly this, and a check that fired now would
mean the fix had not held. What makes the sweep worth its lines is the opposite
test: with `_grounded_planes` disabled — the one M13.6 change that ties `In2.Cu` —
`PCIE_RX` fails immediately and by name, with the layer, the net and the area. That
is `test_a_slice_that_leaves_a_plane_floating_is_refused`, and it is M13.5's board
reconstructed and refused instead of simulated.

### 2.3 The clip band, and the 16 stitching vias nobody could see

M13.6's finding was that the launch corridor counted its removals and the 0.5 mm
clip band did not, so `REFCLK`'s slice reported `0 via(s) were removed` while
carrying none of the stitching inside its own window. Both bands record now, into
one list the slice carries and its summary counts. Only vias inside the slice's own
window count as removals — a via outside `rect` was never in this pair's window and
saying so would be noise, not loudness.

What that made visible, on the eleven `pcie-sata` slices:

| slice | clip band | of which 0.6 mm stitching | launch corridor |
|---|---|---|---|
| `PCIE_RXN+PCIE_RXP` | 1 | 0 | 0 |
| `PCIE_TXN+PCIE_TXP` | 1 | 0 | 0 |
| `REFCLKN+REFCLKP` | 1 | 0 | 0 |
| `SATA0_RXN+SATA0_RXP` | **4** | **4** | 0 |
| `SATA1_TXN+SATA1_TXP` | **4** | **4** | 0 |
| `SATA2_RXN+SATA2_RXP` | **4** | **4** | 0 |
| `SATA3_TXN+SATA3_TXP` | **4** | **4** | 0 |
| the other four | 0 | 0 | 1 each |
| **total** | **19** | **16** | **4** |

**Sixteen of M10's stitching vias are still being dropped, and until this milestone
nothing said so.** M13.6 closed the symptom — no slice has a floating plane any more,
because `enclose_vias` grows the window by a bounded 0.8 mm and the fence stitches
the boundary — but it did not close the class, and the bounded constant was chosen
precisely to *avoid* the cascade that would have. So the residue is a deliberate
trade-off that nobody had numbers for. Now every one of them is named:

```
4 via(s) inside the slice window sat in the 0.50 mm clip band just inside the
outline and were removed: GND at (144.000, 128.000), GND at (152.000, 128.000),
GND at (160.000, 128.000), GND at (176.000, 128.000)
```

Four vias, all at `y = 128.000`, which is M10's 8 mm grid line — the same
coincidence-of-geometry M13.6 diagnosed, one row further out. Whether it matters is
now a question somebody can ask with a number in front of them; it is on the
roadmap, and it is not this milestone's to answer.

## 3. Three solvers at once, and why there is no win in it

### 3.1 The premise that was false

ADR 0011 Decision 4 declined `--parallel N` because "openEMS already uses every core
— it reported 750–1270 MCells/s on this machine's sixteen". M13.6 read the engine's
own startup benchmark off every link of a batch and found four or five threads of
sixteen at 256–451 MC/s. M13.7, on an idle machine, found five or six at 489–619:

```
Multithreaded Engine: Best performance found using 5 threads.
Multithreaded Engine: Best performance found using 6 threads.
```

So the auto-tuner's answer moves with the model and with the load, and what it never
does is take the machine. This is the `CLAUDE.md` pattern for the third time, and
the flag was built to collect what the corrected premise seemed to promise.

### 3.2 The measurement, which says no

Three links, the same slices, first one at a time and then all three at once:

| link | cells | alone: wall | MC/s | threads | ×3: wall | MC/s | threads |
|---|---|---|---|---|---|---|---|
| `PCIE_TXN+PCIE_TXP` | 0.94 M | 199 s | 619 | 6 | 986 s | **95** | 4 |
| `PCIE_RXN+PCIE_RXP` | 1.00 M | 170 s | 606 | 6 | 1 022 s | **67** | 2 |
| `REFCLKN+REFCLKP` | 1.37 M | 324 s | 489 | 5 | 953 s | **154** | 6 |
| **batch wall clock** | | **693 s** | | | **1 023 s** | | |

**48 % slower, and the aggregate throughput of three solvers — 316 MC/s — is below
what one solver gets on its own.** Mid-run the three together drew about 750 % of a
CPU where one alone draws about 600 %, and each held only ~300 MB, so neither cores
nor memory was the limit. What ran out is **memory bandwidth** — which is also the
reason the engine declines the other ten cores in the first place, and running three
processes does not create any. The engine makes it worse by re-benchmarking under
contention and choosing *worse* thread counts than it would alone (one solver
settled on two), then keeping them for the whole run.

**So Decision 4's conclusion stands and its reasoning does not.** The default stays
sequential. The flag ships because this answer is a property of one memory system: a
host with more channels may go the other way, and every run now reports the
throughput and thread count it got so another machine's answer is comparable.

Two things the concurrency did **not** change, both checked rather than assumed:
impedances agree with the sequential run to within 0.04 % (72.97 / 49.53 / 79.56 Ω
against 72.94 / 49.53 / 79.59), and the batch reports in pair order rather than in
finishing order, so a concurrent run produces the same `manifest.json`.

### 3.3 The confound, which is real and is this host's fault

**This machine cannot pin a container to a set of CPUs**, so the numbers above are
for *unpinned* concurrency. Rootless podman on cgroup v2 is delegated
`cpu memory pids` and not `cpuset`:

```
crun: controller `cpuset` is not available under /sys/fs/cgroup/user.slice/...
$ cat /sys/fs/cgroup/user.slice/user-1000.slice/user@1000.service/cgroup.controllers
cpu memory pids
```

`--cpuset-cpus` is accepted by the podman CLI and refused by the OCI runtime at
container start, which is exactly the shape of failure that costs an afternoon if it
is discovered inside a batch. So `runner.supports_cpuset` probes for it once — a
`/bin/true` container, about a second — and the batch falls back to unpinned
concurrency, says so as an `info`, and records `pinned: false` in its manifest.
Pinned and shared-pool numbers are not comparable and a report that does not say
which it got cannot be used.

Granting the controller is a `Delegate=` drop-in on `user@.service`. That is a root
change to somebody's machine, and not something a PCB tool should require.

### 3.4 One thing the measurement fixed on its way past

`RunOutcome.cells` had been `None` on every run this tool has ever done. Three
patterns for the mesh size were being matched and the one openEMS actually prints
was not among them — and the number changes notation partway up: a 0.94 M mesh
prints `942354` and a 1.37 M one prints `1.37063e+06`, in the same line of the same
log. Both are read now, which is why the table in §3.2 has a cells column at all.

## 4. What changed, and what it cost

### Source

| file | what |
|---|---|
| `si/integrity.py` | **new.** `inspect_return_path`, `ReturnPath`, `Floating`; net-gated connectivity over zones-per-layer, tracks, via spans and pads |
| `si/slice.py` | `_Hop`, `_bridge_tracks` (the bridge in two netted halves), `RemovedVia`, `_Assembly`, `_removal_notes`, `_check_return_path`; `SliceError` gains `fatal`/`status`; `Slice.removed_vias` |
| `si/runner.py` | `CPUS_PER_SOLVER`, `cpu_slots`, `default_parallel`, `supports_cpuset`, `arm_cleanup`, `_throughput`; `run_gerber2ems(cpus=...)`; `RunOutcome.mcells_per_s/threads/cpus`; `_CELLS` matches what the image prints |
| `si/run.py` | `simulate_pairs(parallel=...)`, a slot free-list over a thread pool, per-pair `Report`s merged in pair order, `SimulationBatch.parallel/pinned` |
| `cli_simulate.py` | `--parallel` / `-j` |
| `docs/decisions/0011-si-simulation.md` | Decision 4 amended; **Decision 4a** added with the measurement, the version and the expiry |
| `docs/format.md` | the bridge carries its nets; the two checks documented with what they cannot see; a "running several at once" section that leads with the measurement |
| `docs/roadmap.md` | `PCIE_TX` rewritten around the refuted hypothesis and the new signature; the parallelism entry closed with numbers |

No design file changed, and no copper moved.

### Tests

The suite grew by **twelve**:

| test | what it holds |
|---|---|
| `test_a_via_the_clip_band_takes_is_named_and_counted` | the band that ate 22 vias silently names every one it takes |
| `test_every_slice_on_the_corpus_has_one_connected_return_path` | the invariant, asked of the board it was learnt on — and asking about *joined copper*, not about net tags |
| `test_a_slice_that_leaves_a_plane_floating_is_refused` | M13.6's defect reconstructed and refused, with the layer, net and area in the message |
| `test_a_reference_the_slice_does_not_bond_is_refused` | the second clause: the plane the number is measured against has to be there |
| `test_the_slots_are_disjoint_and_cover_the_machine` | two solvers are never handed the same core |
| `test_a_sequential_batch_pins_nothing` | one solver gets the machine, exactly as before |
| `test_the_cpuset_reaches_the_runtime` | `--cpuset-cpus` is on the command line, and absent when it should be |
| `test_a_runtime_that_cannot_pin_says_so_and_still_runs_concurrently` | the rootless-podman fallback, and that the manifest records which of the two happened |
| `test_a_parallel_batch_reports_in_pair_order` | pairs made to finish backwards still report forwards |
| `test_every_pair_gets_a_slot_of_its_own_while_it_runs` | the free-list: never two pairs on one cpuset |
| `test_the_mesh_size_comes_off_the_log_this_image_actually_writes` | both notations, because matching one of them would have looked fixed |
| `test_throughput_and_thread_count_come_off_the_log` | the median, so the warm-up sample does not move a measurement |

`test_a_stitching_via_inside_the_window_is_never_dropped` was **tightened rather than
added to**: it used to accept "some note mentions removals" and now compares what is
missing against what was recorded, so a third removal band could not be introduced
silently either.

### Gates

| check | result |
|---|---|
| `pytest -q` | **exit 0 — 1 204 passed, 2 skipped, 26 m 07 s** (1 206 collected, up from 1 194) |
| `ruff check .` | **All checks passed** |
| `mypy --strict src/aipcb` | **Success: no issues found in 87 source files** (up from 86) |
| goldens | **byte-identical on all eleven examples.** No design file was touched and no copper moved |

Solo run, machine to itself. Against M13.6's 26 m 01 s the suite is **6 s slower for
twelve more tests**, four of which build and route a board.

### Output

| | |
|---|---|
| `.kicad_pcb`, `.kicad_sch`, `.kicad_pro` | unchanged |
| slices | **`PCIE_TX`'s changed**, and only its: two bridge segments became four, carrying nets 4/5 and 6/7 instead of 0. The other ten are byte-identical, because netting a bridge is a change to the only pair that has one |
| `slice.json` | gains `vias_removed` and `vias_removed_detail` on every slice, and a clip-band note on the seven that lose something to it. Not part of the cache digest, so no cached result was invalidated by the reporting |
| `manifest.json` | gains `parallel` and `pinned`; each pair's `run` gains `mcells_per_s`, `threads`, `cpus`, and a `cells` count that had been `None` since M12 |

### Simulation time spent, per step

M12's eleven links cost 7 837 s, M13.5 spent 5 957 s, M13.6 spent 17 755 s. M13.7:

| step | what it needed | solver time |
|---|---|---|
| 1 — the bridge artifact and its mesh | reading files, and two `gerber2ems -g` geometry passes | **~8 s** (no solver) |
| 1 — the verification run | one link, full steps | **199 s** |
| 2 — the invariant and the sweep | sixteen slices, no solver at all | **0 s** |
| 3 — the parallelism baseline | two links, one at a time | **497 s** |
| 3 — the parallelism measurement | three links, all at once | **1 023 s** |
| **total** | | **1 719 s — 28 m 39 s** |

Inside the milestone's half-hour, and not comfortably. The reason is worth naming:
**the parallel measurement cost 1 023 s of the 1 719 precisely because its answer was
negative** — a concurrent batch that had been 2× faster would have cost 350 s and the
milestone would have come in at 17 minutes. A measurement whose cost depends on its
result is one to budget generously for.

## 5. What M13.7 leaves open

* **`PCIE_TX` is still the one link that is not physical**, and the coupling
  capacitors are now eliminated rather than suspected. The next hypothesis is the
  ports: single-ended gain, asymmetric between the halves, on the only link whose
  two ends launch at different pitches and both far from the run's. §1.4
* **Sixteen stitching vias are still lost to the clip band**, on four SATA slices,
  and now the slice says so. Whether closing that changes any number is unmeasured;
  the bounded 0.8 mm growth M13.6 chose was chosen to avoid a cascade, so this is a
  trade-off to re-open with evidence rather than a bug to fix. §2.3
* **The invariant cannot see fill fragmentation**, by construction, because it runs
  before the fill. If a slice ever fails in a way `checks/planes.py` would have
  caught on the real board, that is the seam. §2.1
* **`--numThreads` is unmeasured and unreachable** without patching the pinned
  image, and §3.2 is circumstantial evidence that the auto-tuner is close to right.
* **The four over-budget pairs, the skew-fit accuracy question and M12's degraded
  case** are untouched, as the milestone required.
