mikkelmi2/aipcb/docs/reports/m12.md

# M12 — signal-integrity simulation: delivery report

`aipcb simulate` exists. It cuts one slice per differential pair out of a routed
board, hands each slice to openEMS through Antmicro's gerber2ems in the container
[ADR 0011](../decisions/0011-si-simulation.md) pinned, and turns the S-parameters
that come back into the same source-referenced findings as every other check.

Everything below was measured on 2026-08-21 on the development machine (16 cores,
30 GB RAM), on the tree as committed. Where a number is an estimate or a closed form
rather than a measurement, it says so.

## Deviations, stated loudly

| Item | What happened |
|---|---|
| *"one pair simulated on `examples/mcu-4layer`, results within a plausible sanity band of its design target"* | **Simulated and converged, but the band had to be defined against physics the design target does not model.** The USB pair reads **≈74 Ω** differential. Both closed forms aipcb carries say 121 Ω (IPC-2141) and 127 Ω (Hammerstad) — and both are *bare microstrip formulas applied to a trace with a ground pour 0.2 mm away on each side*. The pair is a coplanar waveguide with ground, not a microstrip, and a 40 % drop is what that does. The band chosen, and the argument for it, are below under "The calibration". |
| *"`examples/diff-pair`'s declared 100 Ω is unreachable"* | **Confirmed, with different numbers than phase 0 assumed.** ADR 0011 wrote ≈270 Ω from a loosely-coupled reading of Hammerstad. aipcb's own formulas, using its own coupling factor, give **151 Ω (IPC-2141) / 156 Ω (Hammerstad)** for that geometry. Either way 100 Ω is not reachable and the example's target is wrong; the correction is recorded here rather than left as a discrepancy between two documents. |
| *"`pcie-sata`: all routed pairs simulated; the structured report renders with per-pair metrics; at least the impedance-vs-target comparison works against the M11a-declared targets"* | **Met.** All eleven logical links on `examples/pcie-sata` were simulated and every one carries a per-pair impedance-against-target row under “The batch”, with return loss, insertion loss, mode conversion, group delay and a verdict beside it. |
| *"whether simulation discriminates the two pairs M11 delivered over their skew budget"* | **Measured, and the answer is no.** Worst in-band \|Scd21\| is **−23.0 dB** for `REFCLKP/N` (0.292 mm of skew) and **−25.2 dB** for `PCIE_RXP/N` (0.256 mm) — and both **pass** the −20 dB default. The three links that come back `mode_conversion=warn` are `SATA3_RXP/N` (−14.3 dB), `SATA3_TXP/N` (−15.7 dB) and `SATA2_TXP/N` (−19.4 dB), whose skews are **0.004, 0.042 and 0.053 mm** against a 0.25 mm budget. The verdict is therefore not merely uninformative about skew on this board: it flags three well-matched pairs and passes both mismatched ones. The cause is a mode-conversion floor that varies by more than 25 dB from pair to pair, while the skew under test moves the number by about 3 dB. Worked through under “The two pairs M11 left open”. |
| Eight pairs of one class, alike in every declared way, simulate **29 Ω apart** | **Measured, unexplained, and the tightest bound in this report on what a single number is worth.** The eight `sata` links share a class, a derived width and gap, a layer, and coupled lengths inside 30.9–31.4 mm, with M11 measuring width and gap deviation at 0.0 on every one. They simulate at 62.5 to 91.9 Ω — −37.5 % to −8.1 % against one 100 Ω target. Deviation, ripple width and return loss move together across the set, which is consistent both with the low readings being real and with their being an artefact of an unconverged extraction. This pass could not separate the two. |
| Insertion loss comes back **positive** on most pairs | **Gain, which is impossible, and it is the same truncation noise as \|Sdd21\| > 1.** 11 of the 22 insertion-loss figures in the batch are above zero, by up to 0.78 dB. The `insertion_loss` verdict still reads `pass` everywhere, because its threshold is “not worse than −3 dB” — on this data that verdict means *no evidence of excess loss*, not a measured loss. Not fixed; the fix is a converged run, not a different threshold. |
| Worst-in-band \|Scd21\| is not comparable across net classes | **A limitation of the reported scalar, found while answering the skew question and deliberately left alone.** `mode_conversion_db` is the maximum over each class's *own* band, so a `pcie` pair swept to 8 GHz and a `sata` pair swept to 6 GHz are not compared over the same interval; and on four of the eleven that maximum lands between 0.50 and 0.61 GHz — the bottom of the band, where the extraction is noisiest and skew-driven conversion is smallest — including two of the three `warn`s. Recorded rather than changed, because changing it changes a metric this milestone publishes. |
| Simulated impedance sits systematically **below** every class target | **Not a defect in the router and not fixed.** Same cause as the first row: every bundled example pours ground up to its pairs at the class clearance, and neither closed form aipcb derives widths from knows about coplanar ground. The widths the tool derives are therefore systematically narrow for the boards it actually builds. Recorded in `docs/roadmap.md`; fixing it means a CPWG model and regenerating every controlled-impedance example. |
| "worst-case deviation **and its location along the trace** where derivable" | **The deviation is reported; the location is not.** Locating an impedance discontinuity along a trace needs a time-domain reflectometry transform of the reflection data, which is a second piece of numerics with its own convergence questions. What is reported instead is the median, the minimum and the maximum of the impedance across the swept band, which bounds the excursion without claiming to place it. Deliberately not built. |
| `--parallel N` | **Not built, and measured rather than assumed.** openEMS already uses every core — it sustained 300–1270 MCells/s on sixteen here — so a second process divides the same cores. ADR 0011 Decision 4. |
| scikit-rf | **Not adopted.** The post-processing is forty lines of `cmath`; adding a numeric stack to the install path of a YAML-and-pydantic tool for that is a bad trade. Every run writes a Touchstone `.s4p` so anyone who wants scikit-rf has the data. |
| `aipcb export` now writes **two** drill files where it wrote one | **A change to what a fab receives**, made deliberately: gerber2ems globs for `*-PTH.drl` and `sys.exit(1)`s when the glob is empty, and splitting by plating is what KiCad's own dialog does by default. ADR 0011, "the drill file had a name nothing globs for". |
| The `.kicad_pcb` stackup disagrees with the source stackup | **Found by this milestone and deliberately *not* fixed.** `compile/board.py` writes KiCad three equal 0.48 mm dielectrics for `examples/pcie-sata`, where the source declares 0.2104 / 1.065 / 0.2104 mm — and impedance is derived from the source. Fixing it changes every existing board, which M12's guardrails forbid. Simulation uses the source stackup and says so. ADR 0011 Decision 2. |
| `epsilon_r` per dielectric, and core-versus-prepreg typing | **Still unreachable**, for the same byte-stability reason. `loss_tangent` was made reachable because it costs nothing (no example sets it, so no board moves) and because it is the single number that decides insertion loss. |
| Energy decay | **The runs do not converge in time the way the vendor's examples do.** gerber2ems's own `stub_short` decays to −70 dB; the `pcie-sata` slices bottom out anywhere between −72 dB and −31 dB — the figure the tool records per pair, tabled under “What the batch cost” — because a slice with two plane layers and an artificial boundary is a resonant cavity, and the big ones are the worse cavities. The consequence is a few percent of truncation noise, visible as \|Sdd21\| a little above unity. It is characterised below rather than hidden, and it is why `max_steps` is a bounded default. |
| *"a deliberately degraded case … shows measurably worse results than the clean version — proving the simulation actually discriminates"* | **Not run as specified, and added to this table by the orchestrator rather than by the milestone.** No pair was deliberately re-routed over a plane split or given an undersized width override and then compared against its clean self. What stands in its place is weaker in one way and stronger in another: an *accidental* degraded case with a measured before/after (the collinear-launch defect, §4 — peak \|Sdd21\| 7.26 → 1.14, impedance 436.6 Ω → 66.6 Ω against an 85 Ω target, energy decay −35 dB plateaued → −70 dB), plus unit-level checks that an off-target line is measured off-target rather than rounded to the port. Those show the machinery discriminates a broken *slice*; they do not show it discriminates a deliberately worsened *layout*, which is what the acceptance asked. Read alongside the skew result below, where the honest answer to "does simulation discriminate" was **no**, this gap matters more than it would on its own. |
| Crosstalk, eye diagrams, IBIS, thermal, PDN | Out of scope by the milestone's own text; recorded in `docs/roadmap.md`. |

Nothing else was descoped.

## What was built

| Piece | Where it lives | Lines |
|---|---|---|
| M12a — which pairs there are, merged across AC-coupling parts | `si/pairs.py` | 181 |
| M12a — cutting one pair out of a routed board, ports and all | `si/slice.py` | 698 |
| M12a — the three files gerber2ems reads besides the Gerbers | `si/inputs.py` | 216 |
| M12b — the container, the cache, and the silent-failure checks | `si/runner.py` | 262 |
| M12b — the batch | `si/run.py` | 379 |
| M12c — S-parameters to verdicts, and Touchstone out | `si/results.py` | 414 |
| the command | `cli_simulate.py` | 226 |
| the `simulation:` source block | `model/simulation.py` | 136 |
| build-and-route, lifted out of `route all` so two commands can use it | `route/pipeline.py` | 108 |
| tests | `tests/test_simulation.py` | 608 |

Two existing files changed in ways a fab can see: `compile/export.py` (two flags) and
`compile/board.py` (`loss_tangent` reaches the KiCad stackup when the source sets
one). `model/layout.py` gained `StackupLayer.loss_tangent` and a named
`DEFAULT_LOSS_TANGENT`.

`route/pipeline.py` is a *move*, not a rewrite: `aipcb route all` now calls it and
its output is byte-identical to before, verified on `examples/mcu-4layer` and
`examples/diff-pair` before anything else was changed.

## How a pair becomes a simulation

```
routed .kicad_pcb
   │
   ├─ logical_pairs()      12 declared pairs on pcie-sata → 11 physical links
   │                       (the transmit lane's two pairs and two capacitors are one link)
   │
   ├─ build_slice()        the pair's copper + everything near it, clipped to a
   │                       tight outline; the capacitors bridged; a straight launch
   │                       grown at each end; four Simulation_Port footprints
   │
   ├─ export_board()       kicad-cli plots it like any other board — ADR 0001 holds,
   │                       aipcb still writes no Gerber itself
   │
   ├─ write_inputs()       stackup.json from the *source* stackup, simulation.json,
   │                       netinfo.json
   │
   ├─ nets_in_gerbers()    read the export back before spending a minute on it
   │
   ├─ slice_digest()       sha256(slice.kicad_pcb + simulation.json + stackup.json)
   │                       → skip if unchanged
   │
   ├─ podman run           gerber2ems -a, geometry + two excitations + postprocess
   │
   └─ analyse()            mixed-mode extraction → Zdiff, RL, IL, verdicts, Touchstone
```

Four things in the slice are not on the real board, and each is an approximation
with a reason:

* **The coupling capacitors become copper.** At 4 GHz a 100 nF capacitor is a
  milliohm; the part under test is the trace on both sides of it. aipcb knows which
  parts those are because the source says `role: ac_coupling` — this is the one place
  where a source-level slicer can do something a geometric one cannot, and on
  `examples/pcie-sata` it is the difference between one 18 mm link and two 10 mm
  stubs with a port in the middle of a capacitor.
* **Each end grows a 1.5 mm straight launch.** openEMS builds a microstrip port
  along a grid axis; a trace that ends on a diagonal at a pad has nowhere to be fed
  from. The port occupies exactly the launch, so it adds no trace — but the pad and
  its antipad are replaced by a uniform line, and the discontinuity that was really
  there is not modelled.
* **The corridor the launches occupy is cleared** of other nets' copper. Past the
  pad is the component, and with the footprints gone that region holds the next
  pins' fanout — on `examples/pcie-sata`, a ground track within a millimetre of every
  pair end. See failure 5 below.
* **Footprints are dropped.** The interior of a run, which is what an impedance
  target is about, is untouched. The last few tenths of a millimetre at each end are
  not modelled.

## Five silent failures, and what caught each one

Phase 0's most useful conclusion was that this integration's failure mode is a
confident wrong answer at a zero exit code, and that whatever aipcb built must assert
the solver saw its inputs rather than trusting the exit status. That turned out to be
exactly right — and to be an understatement. Two of the five below were in the export
(phase 0 predicted them), one was in KiCad's behaviour on a board with no footprints,
and **two were in the slicer this milestone wrote**. Every one of them produced a
board that looked correct, a solver that exited zero, and a number that was wrong.

### 1. The placement file was in the wrong frame (found by reading the file)

Phase 0's fix gave the file a name the consumer globs for. It did not give it the
right *coordinates*: `pcb export pos` defaults to absolute page coordinates, so every
row read like

```
"C1","C_100N_0603","C_0603_1608Metric",145.500000,-122.500000,0.000000,top
```

— the board's position on an A4 sheet, with KiCad's downward Y. Adding
`--use-drill-file-origin` turns that into `45.500000,21.500000`: the part's position
on the board. Verified by reading the exported rows back against the board's own
footprint positions, because the *drill* half of this bug survived a flag that was
already correct, and a test that checks flags would have missed both.

### 2. The drill file had a name nothing globs for

`<board>.drl`, one `MixedPlating` file. gerber2ems globs `*-PTH.drl` and exits 1.
Now `--excellon-separate-th`, which is KiCad's own default in the GUI. This changes
the fabrication package for every design and is flagged as a deviation above.

### 3. KiCad prunes padless nets by renumbering — the one nobody predicted

A slice has tracks and, before this fix, no footprints at all. `pcbnew` drops every
net that no pad references when it loads a board, and it drops them by
**renumbering**: the tracks keep their stored codes, which now point at other nets.
On the first `mcu-4layer` slice that actually ran end to end, the pair's copper came
back labelled `DEV_DM` / `DEV_DP` — its neighbours.

Measured, on that run:

| | |
|---|---|
| Segments in the slice board | 18 `USB_DM`, 17 `USB_DP`, 2 `DEV_DM`, 2 `DEV_DP` |
| Draws in the exported `F_Cu.gbr` under `%TO.N,DEV_DM*%` | **40** |
| Net names the Gerber carried | `DEV_DM`, `DEV_DP`, `GND`, `VBUS` — no `USB_*` |
| What gerber2ems then refined the mesh around | nothing |
| Resulting grid on a 12.5 × 17.5 mm slice | 109 × 109 × 62, **114 µm** average cell |
| What that does to a 0.25 mm trace with 0.2 mm of clearance | merges it into the ground pour it sits in |
| What came back after 4 min 16 s of solving | S₀₀ = −1.005 (a short), \|S₁₀\| = 0.0007 |
| Exit code | **0** |

The fix is two-part and both parts matter. Each port footprint carries one 50 µm pad
on the launch it sits on — copper entirely inside a 200–250 µm trace, so no geometry
moves, and the net survives the load. And **every run now reads its own Gerbers back**
before starting the container: if the pair's net attributes are not in the copper
Gerbers, the pair fails with a diagnostic instead of being solved for a minute and
answered wrongly.

After the fix, the same slice: `USB_DM` and `USB_DP` present in the Gerber, grid
105 × 152 × 28 at the *coarsest* setting tried, \|S₁₀\| = 0.95.

### 4. The two launches of one pair ran on the same line — ours

The launch direction was the average of the two traces' outgoing directions. That is
right for a pair that runs *along* the board and wrong for a pair that leaves its pads
**broadside** — and `examples/pcie-sata`'s three PCIe lanes leave the controller
exactly like that: 0.5 mm apart in x, both heading down the board. The average comes
out along x, both launches run on one line, they overlap, and P is welded to N.

Measured on the transmit lane before the fix, with a completely plausible-looking
board:

| | before | after |
|---|---|---|
| peak \|Sdd21\| | **7.26** | 1.14 |
| worst return loss | **+40.7 dB** | −8.3 dB |
| differential impedance | **436.6 Ω** against 85 Ω | 66.6 Ω |
| energy decay | −35 dB, plateaued | **−70 dB** |
| exit code | 0 | 0 |

The rule is now perpendicular to the pair's own separation, with only the *sign* taken
from where the conductor heads. Five of pcie-sata's twenty-two pair ends were
collinear before it; a test now asserts the property on every pair on the board.

The verdict machinery did its job here — the run came back `impedance=unusable` on the
\|Sdd21\| > 1.15 rule, so nothing wrong was ever reported as a result. But it was one
threshold away from being reported as an impedance, and finding it took reading the
copper rather than reading the numbers.

### 5. The launch ran out past the pad, into the next pin's fanout — also ours

Subtler, with no wrong-looking geometry at all. A launch runs *outward* from where the
pair ends. Where a pair ends is a pad, and past the pad is the component. A slice drops
the footprints, so that region is not empty — it is the neighbouring pins' escape
routing. Measured on `examples/pcie-sata`: **every one of the twenty-two pair ends has
a ground track crossing within a millimetre of it.** A 1.5 mm launch laid straight
through is shorted to ground, and the first working batch was doing that on all eleven
pairs.

Shortening the launch until it fits was tried first and measured badly: on this board
there is frequently no collision-free length at all, so every port collapsed to a
0.4 mm floor — two trace widths, too short to de-embed. What ships instead **clears the
corridor**: foreign tracks are cut where they cross it, vias inside it are dropped, and
the slice reports how much it removed.

| Pair | foreign track removed | vias dropped |
|---|---|---|
| `PCIE_TXN+PCIE_TXP` | 5.02 mm | 0 |
| `SATA2_RXN+SATA2_RXP` | 4.02 mm | 0 |
| `SATA2_TXN+SATA2_TXP` | 3.90 mm | 1 |
| `REFCLKN+REFCLKP` | 3.61 mm | 1 |
| `PCIE_RXN+PCIE_RXP` | 2.48 mm | 0 |
| the other six | 1.00–2.32 mm | 0–1 |

That is a deliberate modification of the same kind as dropping the footprints and
bridging the coupling capacitors: **the port stands in for the pad and for everything
past it** — the driver, the connector, the cable — and the neighbouring pins' fanout is
not the transmission line under test. What matters is that it is visible: it is in the
slice's own `notes`, in `--json`, and in the console output.

## The source block, and what it does not contain

```yaml
simulation:
  classes:
    sata:    { stop_ghz: 6.0 }     # SATA III: 3 GHz fundamental
    pcie_tx: { stop_ghz: 8.0 }     # PCIe Gen3: 4 GHz fundamental
    pcie_rx: { stop_ghz: 8.0 }
```

That is the whole of what `examples/pcie-sata` had to say. Everything else —
which nets are a pair, which capacitors are shorts, what the laminate is, what the
impedance target is, which plane each pair is referenced to, how wide the trace is —
was already in the design, because M8 through M11 put it there. Mesh density, slice
margin and the pass thresholds are settable and are left at their defaults.

`impedance_tolerance`, `return_loss_db` and `insertion_loss_db` default to ±10 %,
−10 dB and −3 dB. **These are engineering defaults, not standards compliance.** Ten
percent and −10 dB are what most controlled-impedance fabrication notes ask for;
nothing here certifies a design against PCIe or SATA, and a link with a real budget
should state its own numbers.

Adding the block to `examples/pcie-sata` left its `.kicad_pcb`, `.kicad_sch` and
`.kicad_pro` byte-identical to the golden files — verified before anything else.

## What a run leaves behind

`out/si/<pair>/` per pair:

| File | What it is |
|---|---|
| `slice.kicad_pcb` | the slice, openable in KiCad and byte-stable |
| `slice.json` | the ports, the outline, the conductor length, and any notes |
| `fab/` | the slice's Gerbers, drill and placement file, plus `stackup.json` |
| `simulation.json`, `netinfo.json` | what gerber2ems was told |
| `ems/` | the solver's own geometry, S-parameters and plots |
| `<pair>.s4p` | the raw S-matrix as Touchstone, for scikit-rf or anything else |
| `result.json` | the cache entry: the digest, the timing and the metrics |
| `run.log` | the full solver log, which a failure's hint points at |

and `manifest.json` beside them, recording every pair, its status, its digest, its
wall clock and the image digest the batch actually ran on.

The Touchstone file says what it does not know: only two of the four columns were
excited, because a differential pair needs both halves of one end driven and the
other two columns are the reciprocal of those. The header states it rather than
letting a reader assume a full four-port sweep.
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
