mikkelmi2/aipcb/docs/reports/m10.md

# M10 — copper pours, stitching vias & plane integrity: delivery report

**Delivered.** M10 stopped once, on 2026-08-21, because `kicad-cli` 9.0.8 cannot
fill a zone and the milestone's own guardrail said to stop rather than work around
it. The project owner accepted [ADR 0009](../decisions/0009-pours.md) Option 1 —
drive KiCad's own filler through a `pcbnew` subprocess, with a version lock — and
this report replaces the stop report with the milestone built on that decision.
**The stop is kept, in "The stop, and what it measured"**: the measurements that
caused it are the reason the implementation looks the way it does, and the
performance table it produced is the pre-pours baseline this one is compared
against.

## Deviations, stated loudly

Everything not delivered as the specification wrote it, in one place and at the top.
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
