mikkelmi2/aipcb/docs/format.md

# The aipcb source format

A design is one YAML file plus the part libraries it names. This document is the
reference; [`examples/`](../examples) holds working designs that exercise
everything described here.

The format is validated by pydantic models, so this document and the schema cannot
drift apart: run `aipcb schema` to emit the JSON Schema for editor completion, and
`aipcb validate` to check a file. Unknown fields are always an error — a misspelled
key must be reported, never silently ignored.
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
