mikkelmi2/aipcb/src/aipcb/checks/mapping.py

# SPDX-FileCopyrightText: 2026 The aipcb Authors
# SPDX-License-Identifier: Apache-2.0
"""Mapping KiCad's UUIDs back to the source that produced them.

``kicad-cli``'s ERC and DRC reports identify every offending item by UUID:

```json
{"description": "Symbol J1 [DB9]", "pos": {"x": 0.3, "y": 0.9},
 "uuid": "00000000-0000-0000-0000-0000442a4c93"}
```

Because every UUID we emit is a hash of the element's path in the source, that
field is a perfect reverse index -- no matching on coordinates, no parsing of
description strings, no ambiguity when two parts have the same value. Rebuilding
the same mapping here is just re-deriving the hashes we already know how to
compute.

This is the payoff for the determinism requirement, and the reason ADR 0001 ruled
out a library that rewrites UUIDs.
"""

from __future__ import annotations

from dataclasses import dataclass

from aipcb.compile.preserve import FINGERPRINT_PROPERTY
from aipcb.ids import element_uuid
from aipcb.kicad.footprints import FootprintNotFound, resolve_footprint
from aipcb.kicad.sexpr import SNode
from aipcb.netlist import ElabComponent, ElabNet, Netlist
from aipcb.source import Loc

__all__ = ["SourceRef", "UuidIndex", "build_index"]


@dataclass(frozen=True, slots=True)
class SourceRef:
    """What a KiCad UUID refers to in the source."""

    kind: str
    """``component``, ``pin``, ``pad``, ``net``, ``label``, ``wire``, ``edge``, …"""
    label: str
    """A human-readable name for it, e.g. ``U1`` or ``U1 pin 8``."""
    path: tuple[str | int, ...] = ()
    loc: Loc | None = None
    component: str | None = None
    net: str | None = None

    def describe(self) -> str:
        return f"{self.kind} {self.label}"


class UuidIndex:
    """Reverse lookup from KiCad UUIDs, and from net names, to source elements."""

    __slots__ = ("_by_net", "_by_refdes", "_by_uuid")

    def __init__(self) -> None:
        self._by_uuid: dict[str, SourceRef] = {}
        self._by_net: dict[str, SourceRef] = {}
        self._by_refdes: dict[str, SourceRef] = {}

    def add(self, uuid: str, ref: SourceRef) -> None:
        self._by_uuid.setdefault(uuid, ref)

    def add_net(self, name: str, ref: SourceRef) -> None:
        self._by_net.setdefault(name, ref)

    def add_refdes(self, refdes: str, ref: SourceRef) -> None:
        self._by_refdes.setdefault(refdes, ref)

    def lookup(self, uuid: str | None) -> SourceRef | None:
        return self._by_uuid.get(uuid) if uuid else None

    def net(self, name: str | None) -> SourceRef | None:
        if not name:
            return None
        # KiCad prefixes sheet-local net names with a path, and invents names for
        # unconnected pads; neither corresponds to a net the source declares.
        return self._by_net.get(name) or self._by_net.get(name.lstrip("/"))

    def refdes(self, refdes: str | None) -> SourceRef | None:
        return self._by_refdes.get(refdes) if refdes else None

    def __len__(self) -> int:
        return len(self._by_uuid)


def build_index(netlist: Netlist) -> UuidIndex:
    """Build the reverse index for a compiled design.

    Every UUID the emitters produce is re-derived here. Keeping the two in step
    matters, so the tests assert that every UUID appearing in a generated file is
    one this index knows.
    """
    index = UuidIndex()

    for component in netlist.sorted_components():
        _index_component(index, component)

    for net in netlist.sorted_nets():
        _index_net(index, net, netlist)

    _index_edges(index, netlist)
    _index_pours(index, netlist)
    _index_sheet_blocks(index, netlist)
    return index


def _index_sheet_blocks(index: UuidIndex, netlist: Netlist) -> None:
    """Map a schematic cluster's frame and name back to the module instance it draws.

    The frames are graphics -- no pin, no net, nothing ERC looks at -- but they are
    still generated elements in a generated file, and an element nothing can account
    for is exactly what the M4 index exists to make impossible.
    """
    for name, members in sorted(netlist.module_instances().items()):
        if not name or not members:
            continue
        first = members[0]
        ref = SourceRef(
            kind="module instance",
            label=name,
            path=("instances", name),
            loc=netlist.locs.get(("instances", name)) or first.loc,
        )
        for prefix in ("block-frame", "block-text"):
            index.add(element_uuid(prefix, f"module:{name}"), ref)


def _index_pours(index: UuidIndex, netlist: Netlist) -> None:
    """Map a zone and every stitching via back to the block that asked for them.

    Without this a clearance violation on a poured plane comes back as "not one
    aipcb generated", which is exactly the wrong answer: the pour *is* declared, and
    the fix belongs on its line in the YAML rather than in KiCad.
    """
    from aipcb.compile.edge import EDGE_ROLE
    from aipcb.compile.zones import finger_keepout_uuid, keepout_uuid, zone_uuid
    from aipcb.route.stitch import MAX_STITCH_VIAS, stitch_uuid
    from aipcb.route.transition import MAX_TRANSITION_VIAS, transition_uuid

    for position, pour in enumerate(netlist.pours):
        index.add(
            zone_uuid(position),
            SourceRef(
                "copper pour",
                pour.reason or pour.label,
                path=("pours", position),
                loc=netlist.locs.get(("pours", position)),
                net=pour.net,
            ),
        )
    keepouts = netlist.layout.placement.keepouts if netlist.layout else ()
    for position, keepout in enumerate(keepouts if netlist.pours else ()):
        index.add(
            keepout_uuid(position),
            SourceRef(
                "keepout",
                keepout.reason or f"region {list(keepout.region_mm)}",
                path=("layout", "placement", "keepouts", position),
            ),
        )
    # The keepout M11b puts round a card edge's fingers is generated rather than
    # declared, so it needs mapping back to the component that caused it.
    if netlist.pours:
        for component in netlist.components_with_role(EDGE_ROLE):
            index.add(
                finger_keepout_uuid(component.refdes),
                SourceRef(
                    "card-edge pour keepout",
                    f"the finger field of {component.refdes}, kept clear of pour",
                    path=netlist.mech_path("placement", component.refdes),
                    loc=netlist.mech_loc("placement", component.refdes),
                ),
            )

    for position, stitching in enumerate(netlist.stitching):
        ref = SourceRef(
            "stitching via",
            stitching.reason or stitching.label,
            path=("stitching", position),
            loc=netlist.locs.get(("stitching", position)),
            net=stitching.net,
        )
        for ordinal in range(MAX_STITCH_VIAS):
            index.add(stitch_uuid(position, ordinal), ref)

    for position, transition in enumerate(netlist.transitions):
        ref = SourceRef(
            "pair via transition",
            transition.reason or transition.label,
            path=("transitions", position),
            loc=netlist.locs.get(("transitions", position)),
            net=transition.pair[0],
        )
        for ordinal in range(MAX_TRANSITION_VIAS):
            index.add(transition_uuid(position, ordinal), ref)


#: How many outline and cutout graphics to index. A DRC violation names a UUID, and
#: the only way back to the source line is to have that UUID in the table -- so the
#: table covers more segments than any real board has rather than guessing.
_MAX_EDGE_SEGMENTS = 256


def _index_edges(index: UuidIndex, netlist: Netlist) -> None:
    """Map every ``Edge.Cuts`` graphic back to the block that declared it.

    Cutouts are indexed separately from the outline, because "copper too close to
    the edge" and "copper inside the flex-tail window" are different problems with
    different fixes, and a diagnostic that pointed at `board.outline` for both would
    send the reader to the wrong block.
    """
    where = ("board", "outline") if netlist.board is not None else ("layout", "outline")
    for position in range(_MAX_EDGE_SEGMENTS):
        index.add(
            element_uuid("edge", position),
            SourceRef("board outline", f"edge segment {position + 1}", path=where),
        )
    for cut, cutout in enumerate(netlist.board.cutouts if netlist.board else ()):
        for position in range(_MAX_EDGE_SEGMENTS):
            index.add(
                element_uuid("edge", "cutout", cut, position),
                SourceRef(
                    "board cutout",
                    cutout.reason or cutout.label,
                    path=("board", "cutouts", cut),
                ),
            )


def _index_component(index: UuidIndex, component: ElabComponent) -> None:
    ref = SourceRef(
        kind="component",
        label=component.refdes,
        path=component.source_path,
        loc=component.loc,
        component=component.path_text,
    )
    # The same UUID identifies the schematic symbol and the board footprint, which
    # is exactly what ties the two together for schematic parity.
    index.add(component.uuid, ref)
    index.add_refdes(component.refdes, ref)

    pins = component.part.pins if component.part is not None else {}
    for number in pins:
        net = component.connections.get(number)
        pin_ref = SourceRef(
            kind="pin",
            label=f"{component.refdes} pin {number}",
            path=(*component.source_path, "pins", number),
            loc=component.loc,
            component=component.path_text,
            net=net,
        )
        for prefix in ("pin", "wire", "label", "nc"):
            index.add(element_uuid(prefix, *component.hier, number), pin_ref)
        # M14: a rail or ground pin carries a power symbol on the end of its stub
        # rather than a text label, and the symbol has a pin of its own. Both map
        # back to the same place a label did -- the pin that asked for the rail.
        symbol_uuid = element_uuid("pwrsym", *component.hier, number)
        index.add(symbol_uuid, pin_ref)
        index.add(element_uuid("pwrsym-pin", symbol_uuid, "1"), pin_ref)
        index.add(
            element_uuid("fp", *component.hier, "pad", number),
            SourceRef(
                kind="pad",
                label=f"{component.refdes} pad {number}",
                path=(*component.source_path, "pins", number),
                loc=component.loc,
                component=component.path_text,
                net=net,
            ),
        )

    _index_footprint_items(index, component)


def _index_footprint_items(index: UuidIndex, component: ElabComponent) -> None:
    """Index a footprint's own graphics and text.

    DRC reports against silkscreen and courtyards as readily as against pads --
    ``silk_over_copper`` names an ``fp_line`` -- so those UUIDs have to resolve too,
    or a real violation arrives with nowhere to point. Reading the library footprint
    is the only way to know how many items it has and in what order, which is the
    same order the board writer numbered them in.
    """
    if component.part is None:
        return
    try:
        footprint = resolve_footprint(component.part.footprint)
    except FootprintNotFound:
        return

    body = SourceRef(
        kind="footprint",
        label=component.refdes,
        path=component.source_path,
        loc=component.loc,
        component=component.path_text,
    )

    counters: dict[str, int] = {}
    for item in footprint.node.items:
        if not isinstance(item, SNode):
            continue
        if item.name == "property":
            key = item.value(0)
            if key is not None:
                index.add(
                    element_uuid("fp-prop", *component.hier, key),
                    SourceRef(
                        kind="footprint text",
                        label=f"{component.refdes} {str(key).lower()}",
                        path=component.source_path,
                        loc=component.loc,
                        component=component.path_text,
                    ),
                )
            continue
        if not _takes_uuid(item.name):
            continue
        position = counters.get(item.name, 0)
        counters[item.name] = position + 1
        # The board writer keys a pad on its number and everything else on its
        # ordinal, and falls back to the ordinal for a pad that has no number --
        # which a QFN's paste-only sub-pads do not. Mirroring that here is what
        # keeps "every UUID we emit maps back to source" true: `index.add` keeps
        # the first entry, so a numbered pad keeps the richer reference the pin
        # loop above already gave it.
        key = (item.value(0) if item.name == "pad" else None) or str(position)
        index.add(element_uuid("fp", *component.hier, item.name, key), body)

    # Reference and Value are always rewritten, and the fingerprint is added by the
    # board writer, so none of the three need exist in the library footprint.
    for key in ("Reference", "Value", FINGERPRINT_PROPERTY):
        index.add(
            element_uuid("fp-prop", *component.hier, key),
            SourceRef(
                kind="footprint text",
                label=f"{component.refdes} {key.lower()}",
                path=component.source_path,
                loc=component.loc,
                component=component.path_text,
            ),
        )


def _takes_uuid(name: str) -> bool:
    """Mirrors the board writer's rule for which footprint children carry a UUID."""
    return name.startswith("fp_") or name in ("pad", "zone", "dimension", "group")


def _index_net(index: UuidIndex, net: ElabNet, netlist: Netlist) -> None:
    ref = SourceRef(
        kind="net",
        label=net.name,
        path=net.source_path or ("nets", net.name),
        loc=net.loc,
        net=net.name,
    )
    index.add(net.uuid, ref)
    index.add_net(net.name, ref)
    for prefix in ("pwrflag", "pwrflag-wire", "pwrflag-label", "pwrflag-sym"):
        index.add(element_uuid(prefix, net.name), ref)
    index.add(element_uuid("pwrflag-pin", net.name, "1"), ref)
    # The flag drives a rail symbol through a short wire (M14); the symbol and its
    # pin belong to the same net the flag does.
    index.add(
        element_uuid("pwrsym-pin", element_uuid("pwrflag-sym", net.name), "1"), ref
    )
