mikkelmi2/aipcb/src/aipcb/route/pairs.py

# SPDX-FileCopyrightText: 2026 The aipcb Authors
# SPDX-License-Identifier: Apache-2.0
"""Differential pairs: routed as one thing, realized as two runs with a neck.

A pair is not two nets that happen to run alongside each other -- its impedance
comes from the coupling between them -- so it is routed as a single object with a
single path, and only becomes two pieces of copper at the last moment. The centre
line is tightened once, as though it were one fat track wide enough for both traces
and the gap, and then offset to either side; the gap is correct everywhere by
construction, corners included.

What is *not* by construction is either end. Where the two halves leave the pair's
own pitch for pads that are somewhere else, they are on their own, and this module
is mostly about being honest about that:

* the fan-out is tightened rather than drawn, so it goes round what is in its way;
* it necks down to the class's ordinary trace width, because it is not coupled to
  anything and because a pair trace often cannot land on a fine-pitch pad at all;
* the coupled run is trimmed to the part of it that is genuinely clear;
* and every check that could refuse the pair is a measurement, reported with its
  number, rather than a shrug.

Where the answer is "this is not a pair on this board", it says so and the caller
routes the halves separately -- which is worse, and true.
"""

from __future__ import annotations

import math
from dataclasses import dataclass, replace
from itertools import pairwise
from typing import Any

from aipcb.diagnostics import Report, Severity
from aipcb.netlist import Netlist
from aipcb.route.diffpair import DiffPair, split_centre_line
from aipcb.route.geometry import (
    geometry_for,
    resample,
    rules_for,
    simplify,
    tighten_leg,
    track_obstacles,
)
from aipcb.route.graph import RoutePath
from aipcb.route.meander import lengthen
from aipcb.route.negotiate import Connection
from aipcb.route.obstacles import Obstacle, RoutingEnvironment
from aipcb.route.stack import RoutingStack
from aipcb.route.stretch import (
    LayerGeometry,
    RoutedConnection,
    RouteRules,
    StretchError,
    StretchResult,
    stretch_guided,
)
from aipcb.route.triangulate import FreeSpaceError

__all__ = [
    "MAX_UNCOUPLED",
    "PairAudit",
    "WallHug",
    "measure_skew",
    "realize_pair",
]

Point = tuple[float, float]

#: M11d rule 2, the two numbers. A controlled-impedance segment that runs within
#: ``HUG_DISTANCE x gap`` of another copper feature for more than
#: ``HUG_LENGTH x gap`` is hugging a wall: close enough for that feature to be part
#: of the field the pair sees, and for long enough that it matters. Both are
#: multiples of the pair's own gap because the gap is the length the coupling works
#: at -- a feature three gaps away is most of a decade down in influence, and a
#: run of five gaps is where the discontinuity stops being a corner and starts
#: being a section of transmission line with the wrong impedance.
HUG_DISTANCE = 3.0
HUG_LENGTH = 5.0

#: How much of a pair may be fan-out before it stops being worth calling coupled.
#: A short uncoupled breakout at each end is normal and unavoidable -- pads are
#: never at the pair's own pitch -- so this is a judgement call rather than a
#: physical limit, and the actual figure is reported either way.
#:
#: A third, rather than M7's quarter. The fan-out is now *tightened* rather than
#: drawn straight at the pads, so it goes round what is in its way and is honestly
#: longer for it -- on `usb-port` the device-side pair measures 28%, where the
#: straight line that used to be drawn measured less and went through a pad.
MAX_UNCOUPLED = 1 / 3

#: How far inside an inflated hull a path has to go before it counts as a collision
#: rather than as a tightened path wrapped around it, in millimetres. A nanometre --
#: KiCad's own resolution, so anything this close is the same point.
_GRAZE = 1e-6

#: How finely the coupled run is sampled when looking for the part of it that is
#: genuinely clear, in millimetres.
_TRIM_STEP = 0.05

#: How finely rule 2 samples a stretch that passes close to something, in
#: millimetres. Only the part already inside the skirt is sampled, so this is a
#: few dozen points per feature rather than a few hundred per board.
_HUG_STEP = 0.05


@dataclass(frozen=True, slots=True)
class WallHug:
    """A stretch of coupled run that spent too long too close to something else."""

    feature: str
    """The obstacle's key -- ``J1.6#7`` for a pad, ``track:GND/...`` for copper."""
    net: str | None
    layer: str
    length_mm: float
    """How far the pair ran within :data:`HUG_DISTANCE` gaps of it."""
    closest_mm: float
    """The nearest the two came, copper edge to copper edge."""

    def to_dict(self) -> dict[str, Any]:
        return {
            "feature": self.feature,
            "net": self.net,
            "layer": self.layer,
            "length_mm": round(self.length_mm, 4),
            "closest_mm": round(self.closest_mm, 4),
        }
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
